tschicki/PS2-Portable/Documentation/assets/EE_Thermal_Pad.jpg

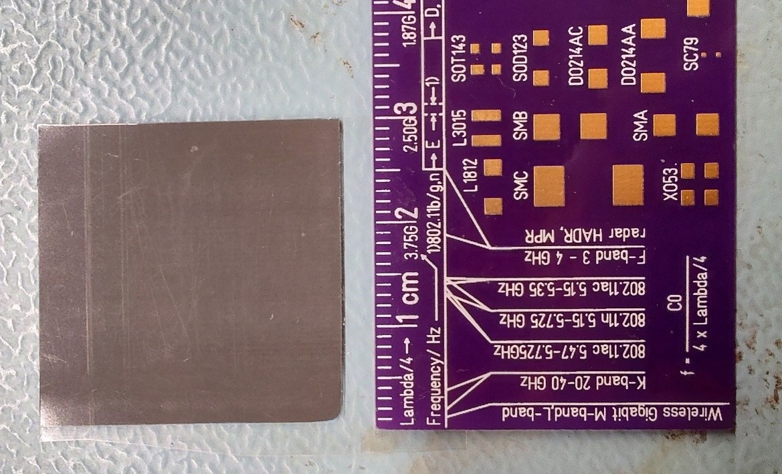
Documentation/assets/EE_Thermal_Pad.jpg
