tschicki/PS2-Portable/Documentation/assets/PS2_Impedances_Back.png

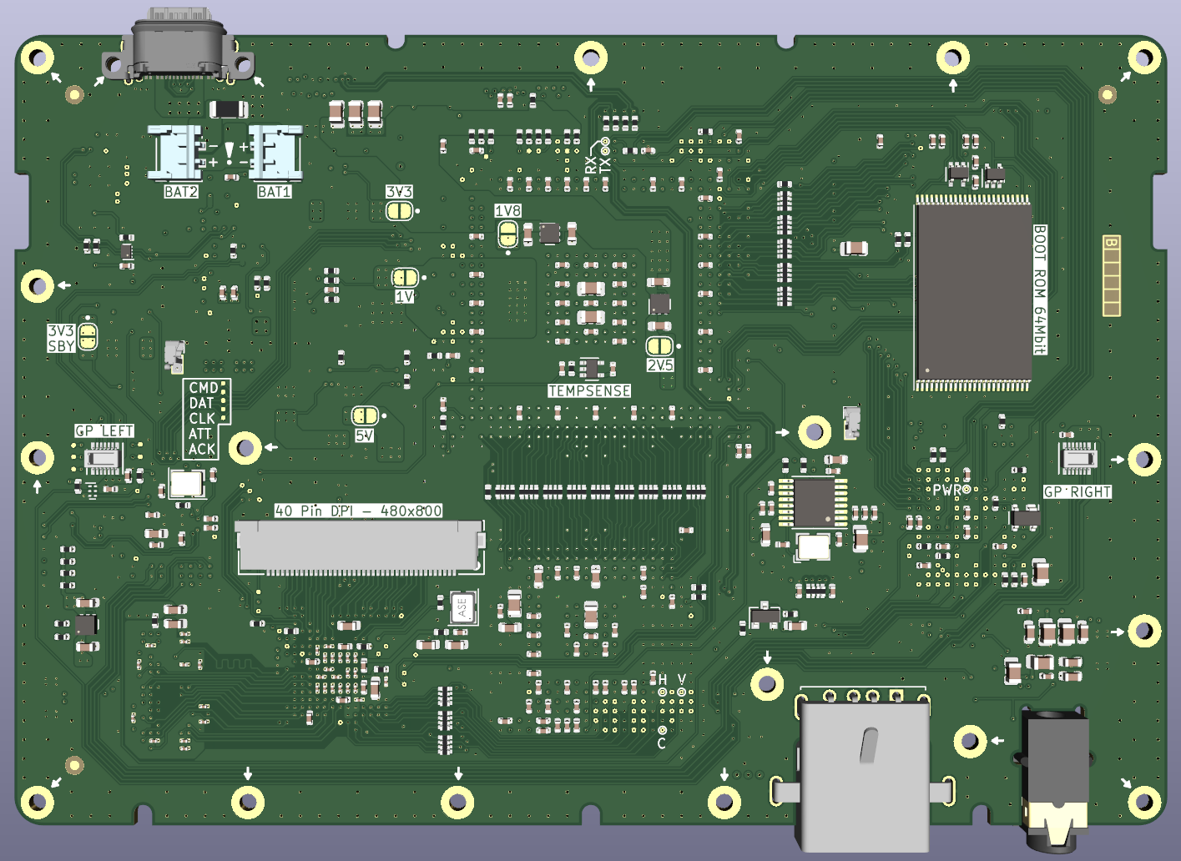
Documentation/assets/PS2_Impedances_Back.png
