tschicki/PS2-Portable/Electronics/PS2_79004_Rev_0_4/Images/LCD_Pinout.PNG

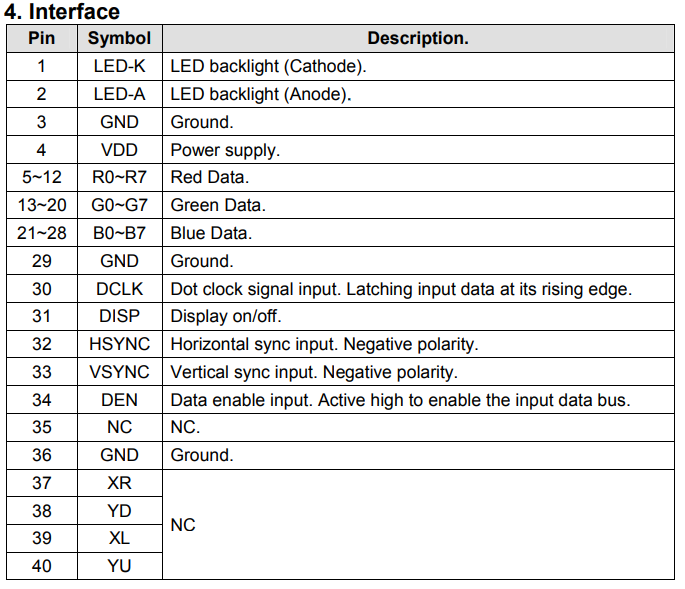
Electronics/PS2_79004_Rev_0_4/Images/LCD_Pinout.PNG
