tschicki/PS2-Portable/SysCon Firmware/SysCon_FW/ps2_video_processor/sdc/input.PNG

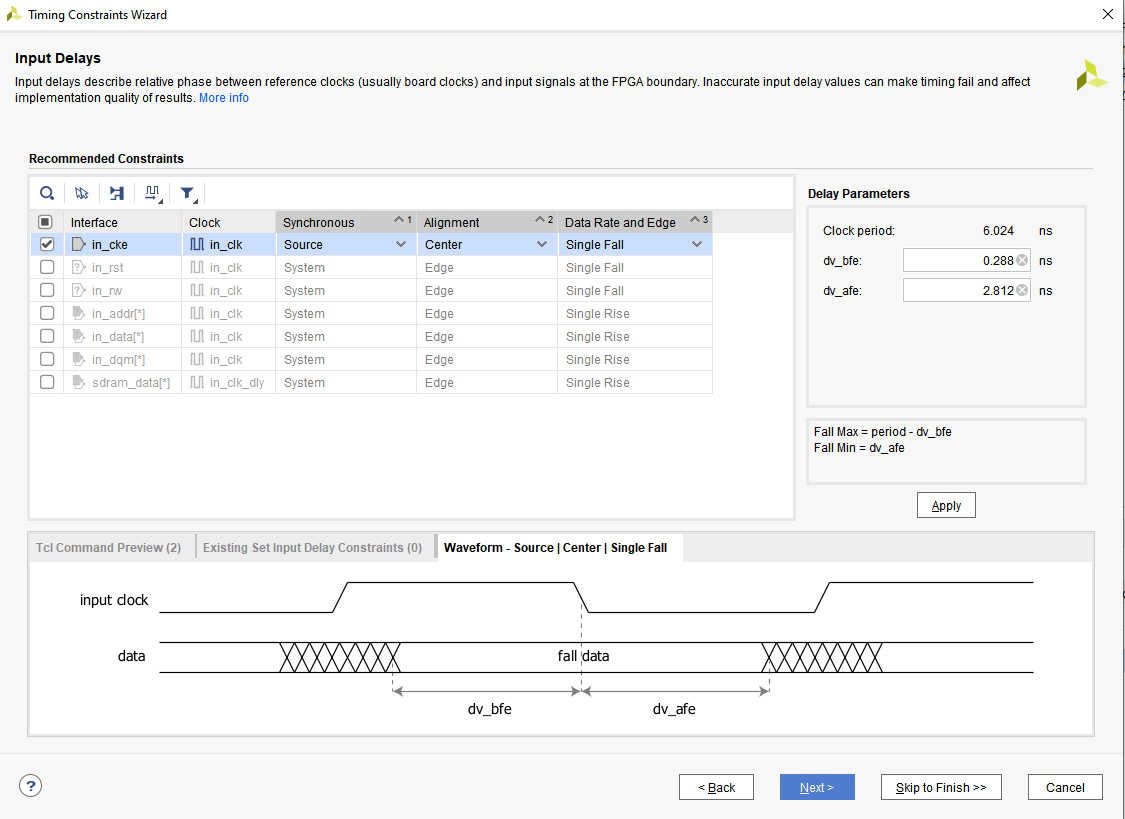
SysCon Firmware/SysCon_FW/ps2_video_processor/sdc/input.PNG
