tschicki/PS2-Portable/SysCon Firmware/SysCon_FW/ps2_video_processor/sdc/output1.PNG

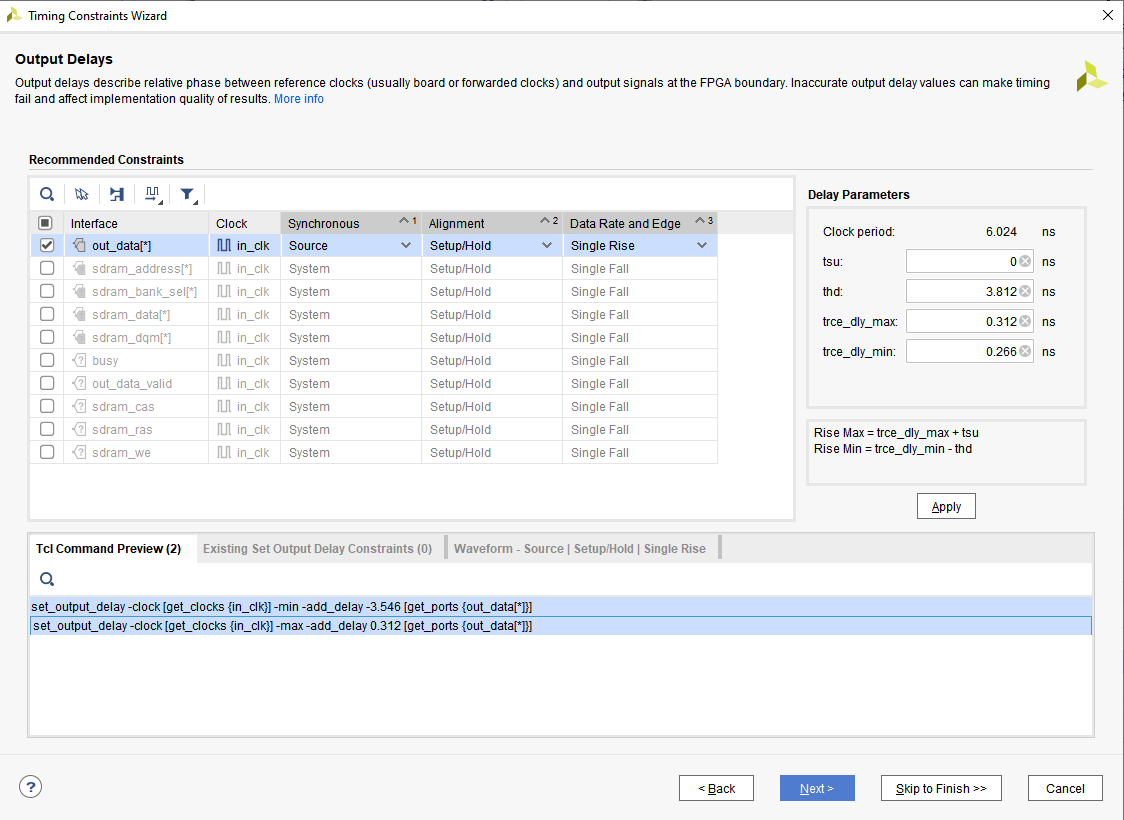
SysCon Firmware/SysCon_FW/ps2_video_processor/sdc/output1.PNG
