tschicki/PS2-Portable/Electronics/PS2_79004_Rev_0_4/Images/Ordering.png

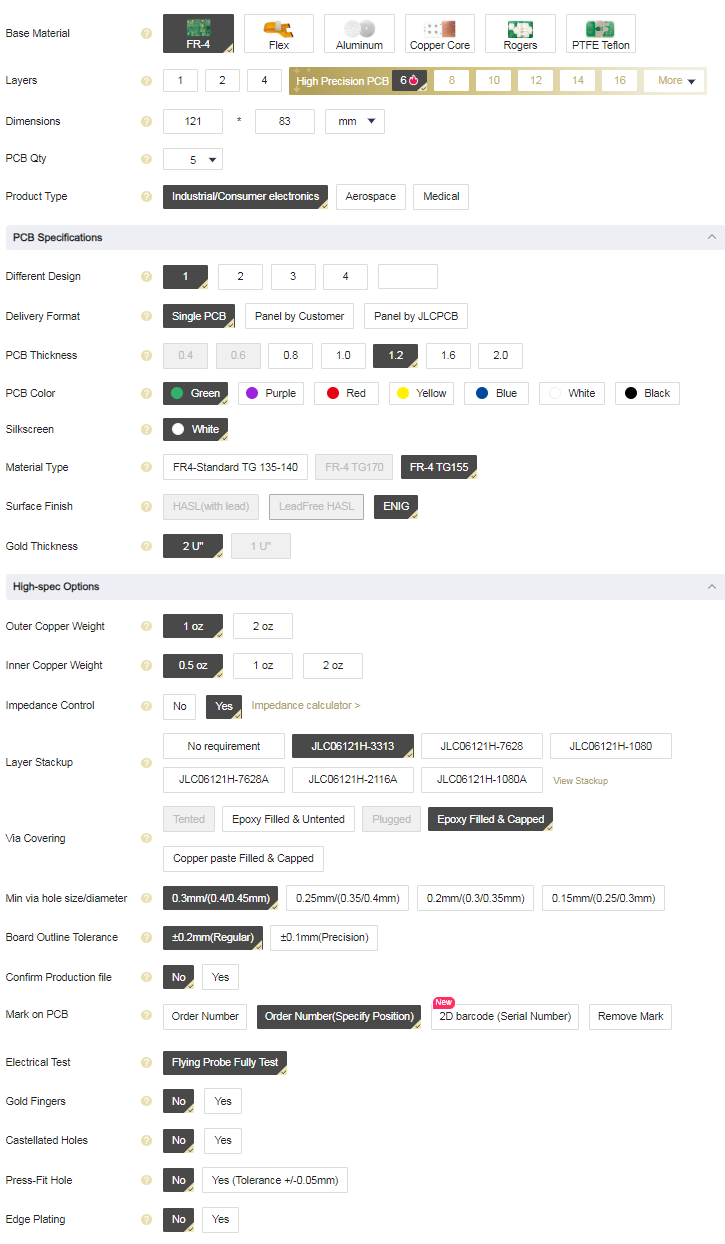
Electronics/PS2_79004_Rev_0_4/Images/Ordering.png
