tschicki/PS2-Portable/Solidworks/uSD2PSX/uSD2PSX_Base.SLDPRT

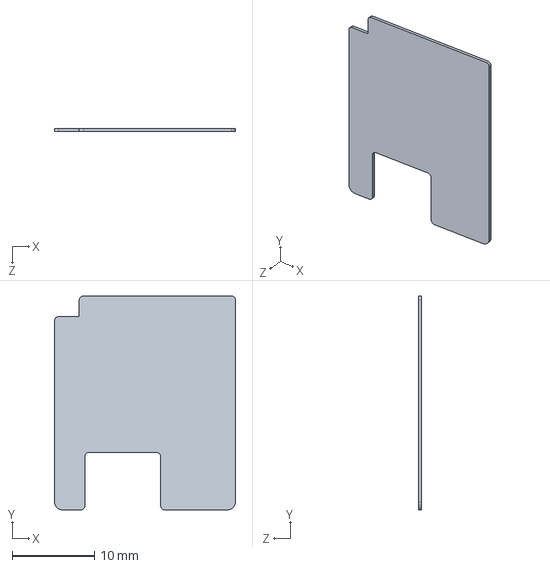
[picture p54: CAD file, 2025-11-29]
Solidworks/uSD2PSX/uSD2PSX_Base.SLDPRT
22.0 x 26.0 x 0.4 mm
