tschicki/PS2-Portable/_LIBRARIES/3D/FTSH-105-01-F-DV-K.stp

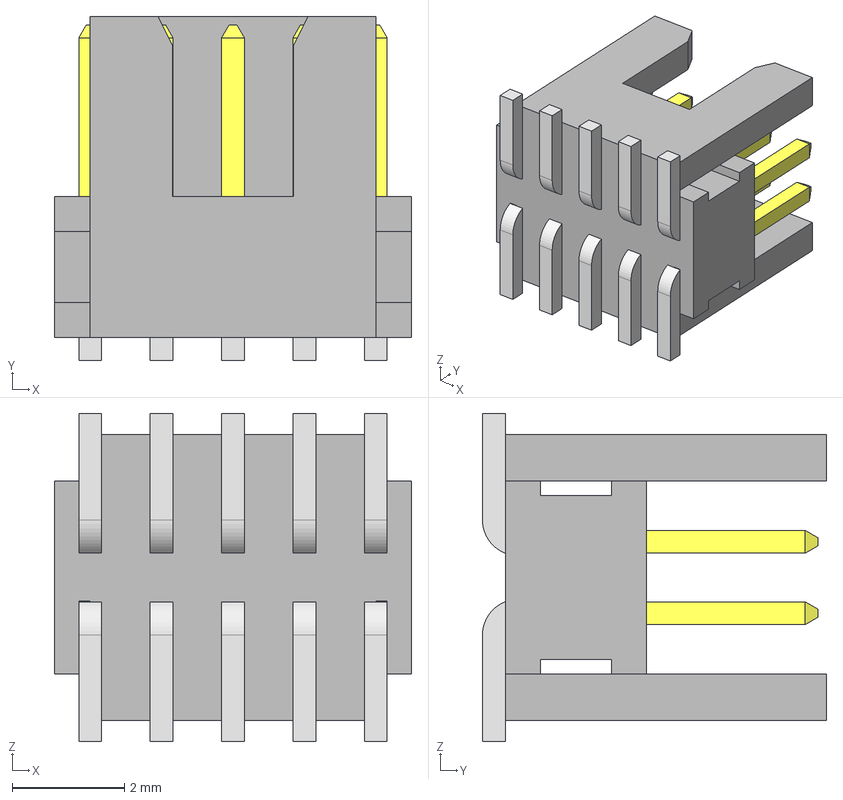
[picture p55: CAD file, 2025-11-29]
_LIBRARIES/3D/FTSH-105-01-F-DV-K.stp
6.35 x 6.12 x 5.84 mm
FTSH-105-01-F-DV-K_pins2
FTSH-105-01-F-DV-K_pins1
FTSH-105-01-F-DV-K_body
