tschicki/PS2-Portable/Solidworks/Button_Cover.SLDPRT

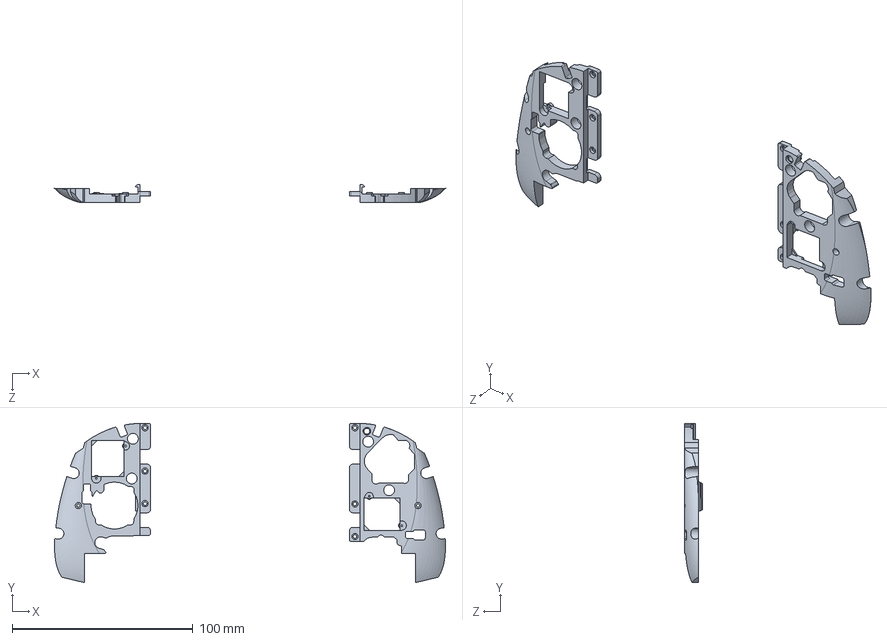
[picture p56: CAD file, 2025-11-29]
Solidworks/Button_Cover.SLDPRT
216.4 x 88.1 x 10.2 mm
