tschicki/PS2-Portable/Solidworks/CBA_Export/Gamepad_Right_export.SLDPRT

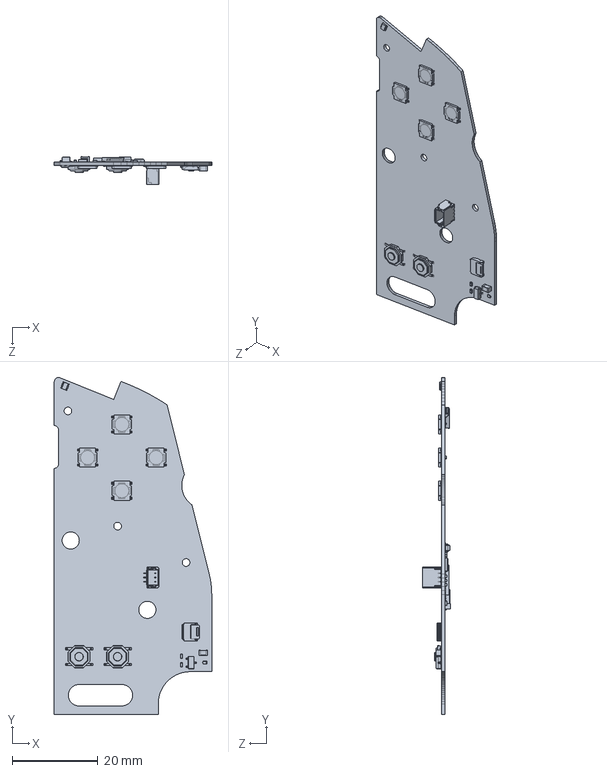
[picture p57: CAD file, 2025-11-29]
Solidworks/CBA_Export/Gamepad_Right_export.SLDPRT
36.8 x 78.7 x 6.50 mm
