tschicki/PS2-Portable/Solidworks/OTS_Parts/3DSXL_Screen_Lens.SLDPRT

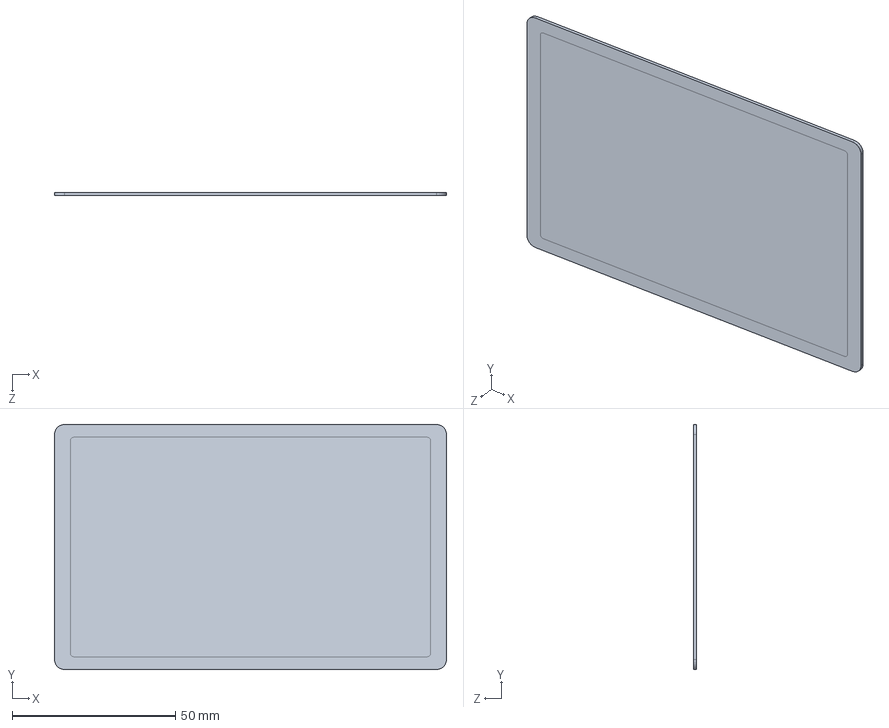
[picture p58: CAD file, 2025-11-29]
Solidworks/OTS_Parts/3DSXL_Screen_Lens.SLDPRT
120.0 x 75.0 x 1.00 mm
