tschicki/PS2-Portable/Solidworks/Output/Output Assembly/DPAD Sanding Tool.SLDPRT

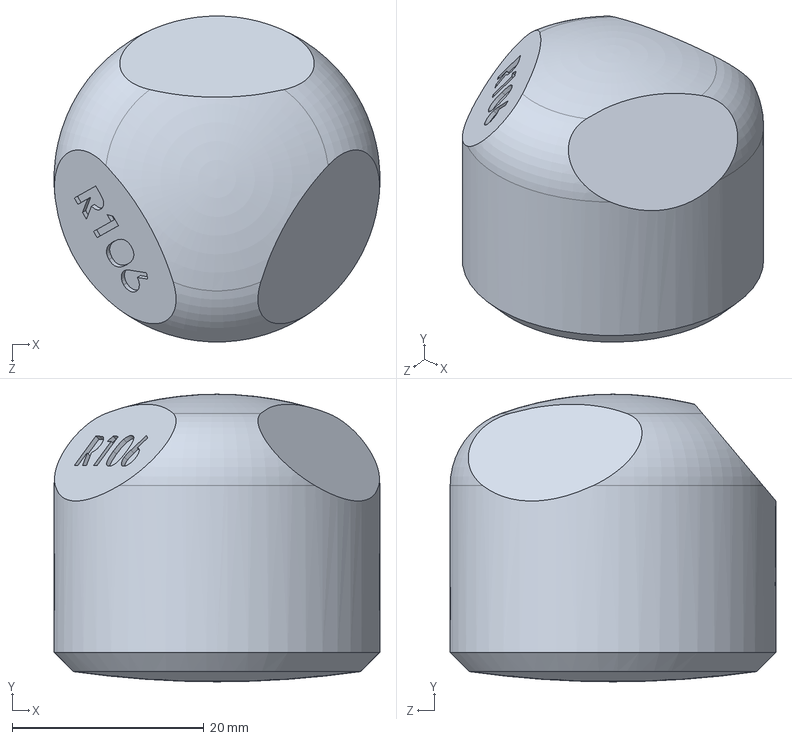
[picture p59: CAD file, 2026-04-04]
Solidworks/Output/Output Assembly/DPAD Sanding Tool.SLDPRT
34.0 x 30.0 x 34.0 mm
