tschicki/PS2-Portable/Solidworks/Output/STEP/Speaker Plug REF2016.STEP

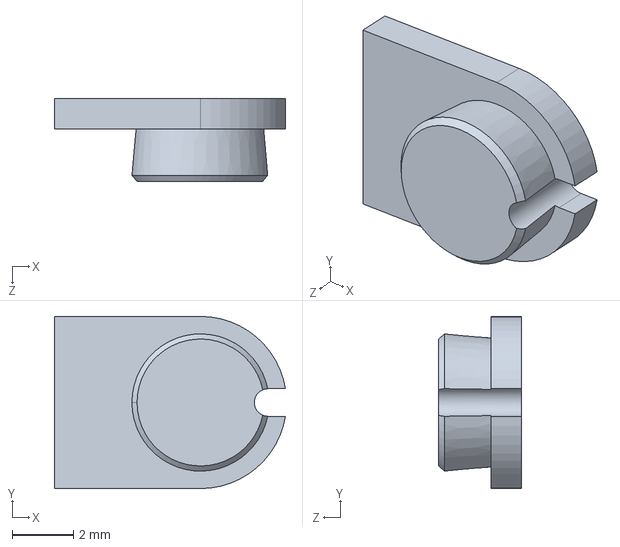
[picture p60: CAD file, 2026-04-04]
Solidworks/Output/STEP/Speaker Plug REF2016.STEP
7.51 x 5.60 x 2.70 mm
