tschicki/PS2-Portable/Solidworks/Output/STL/Export - Travel Case Top REF2020-1.STL

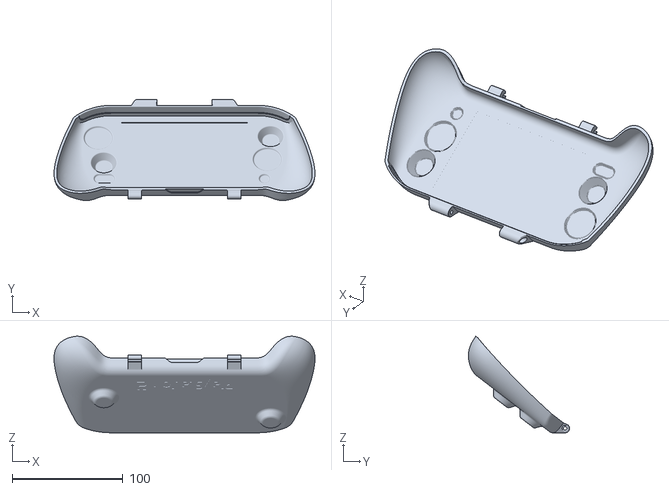
[picture p61: CAD file, 2026-04-04]
Solidworks/Output/STL/Export - Travel Case Top REF2020-1.STL
236.2 x 91.6 x 87.4
