tschicki/PS2-Portable/_LIBRARIES/3D/DF40C-80DP-0.4V_51_.step

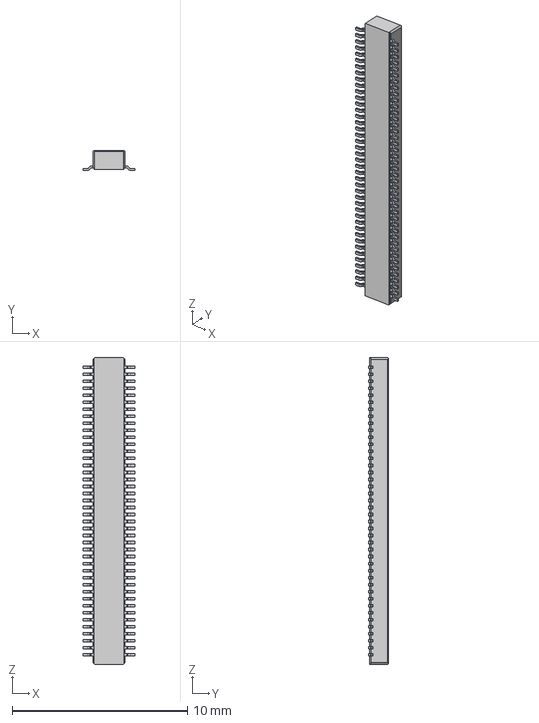
[picture p62: CAD file, 2025-11-29]
_LIBRARIES/3D/DF40C-80DP-0.4V_51_.step
2.97 x 1.14 x 17.5 mm
