tschicki/PS2-Portable/Solidworks/OTS_Parts/Switch_Joystick.SLDPRT

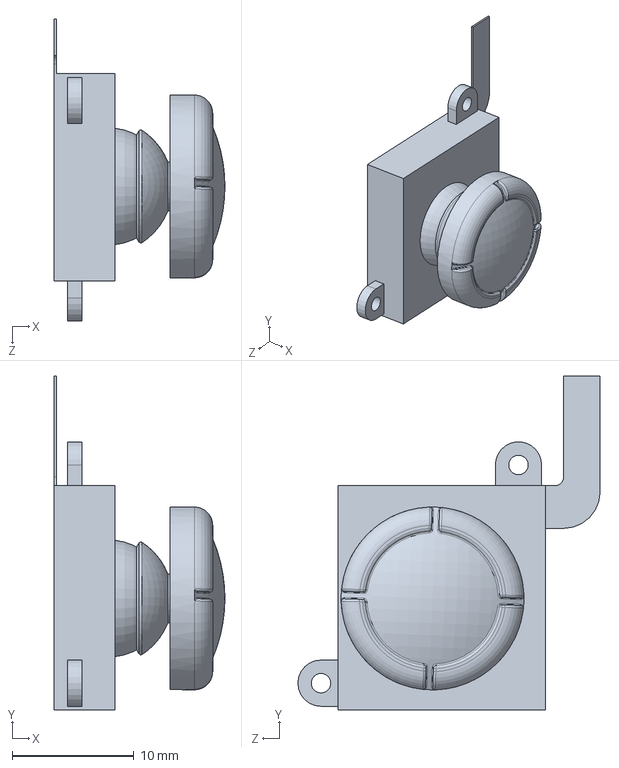
[picture p63: CAD file, 2025-11-29]
Solidworks/OTS_Parts/Switch_Joystick.SLDPRT
14.0 x 27.4 x 24.8 mm
