tschicki/PS2-Portable/Solidworks/Output/Output Assembly/PS2 Heatsink REF3000.SLDPRT

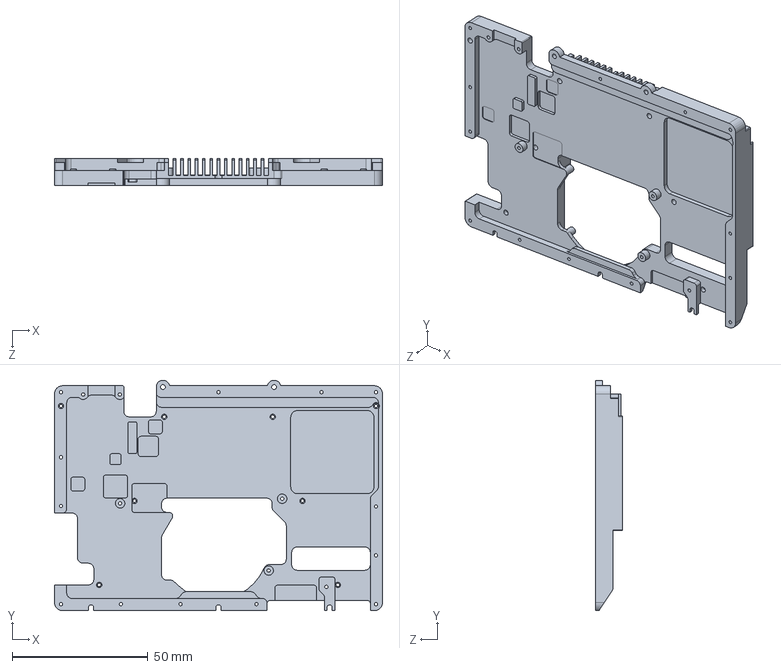
[picture p64: CAD file, 2026-04-04]
Solidworks/Output/Output Assembly/PS2 Heatsink REF3000.SLDPRT
121.0 x 85.0 x 10.0 mm
