tschicki/PS2-Portable/Solidworks/Output/STEP/L2 Button REF2011.STEP

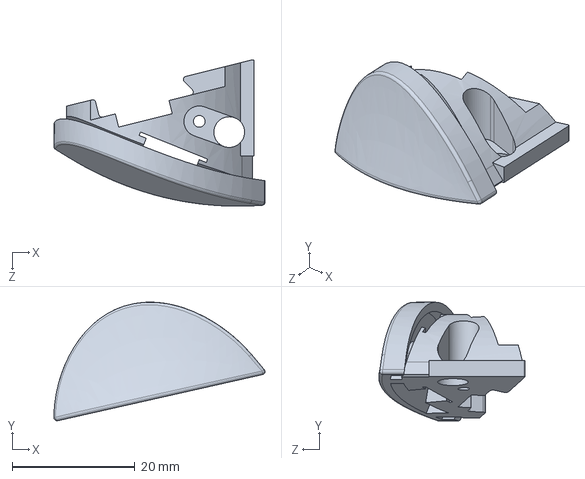
[picture p65: CAD file, 2026-04-04]
Solidworks/Output/STEP/L2 Button REF2011.STEP
34.4 x 19.3 x 23.9 mm
