tschicki/PS2-Portable/Solidworks/Output/STL/Export - Battery Compartment Left REF2004-1.STL

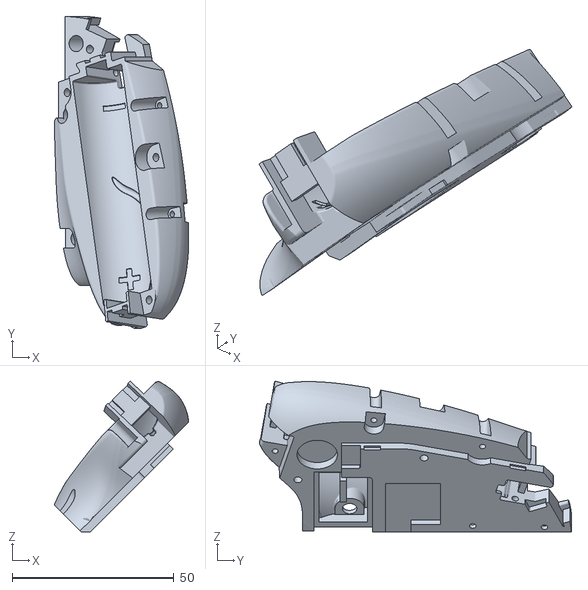
[picture p66: CAD file, 2026-04-04]
Solidworks/Output/STL/Export - Battery Compartment Left REF2004-1.STL
41.5 x 96.3 x 46.6
