tschicki/PS2-Portable/Solidworks/uSD2PSX/uSD2PSX_PCBA.SLDPRT

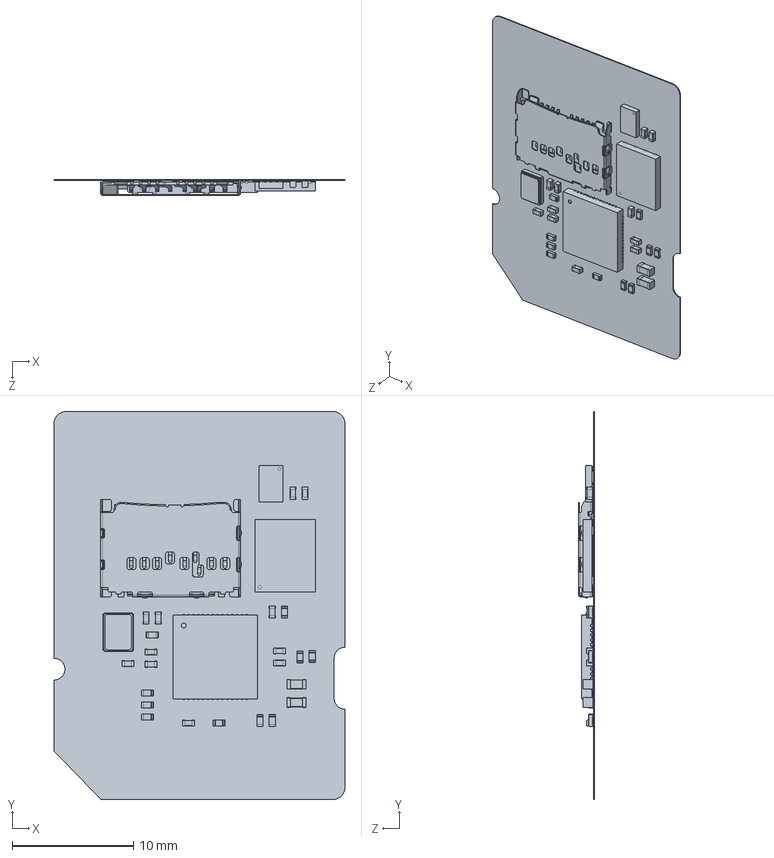
[picture p67: CAD file, 2025-11-29]
Solidworks/uSD2PSX/uSD2PSX_PCBA.SLDPRT
24.0 x 32.0 x 1.34 mm
