tschicki/PS2-Portable/_LIBRARIES/3D/EAST1616RGBA0.STEP

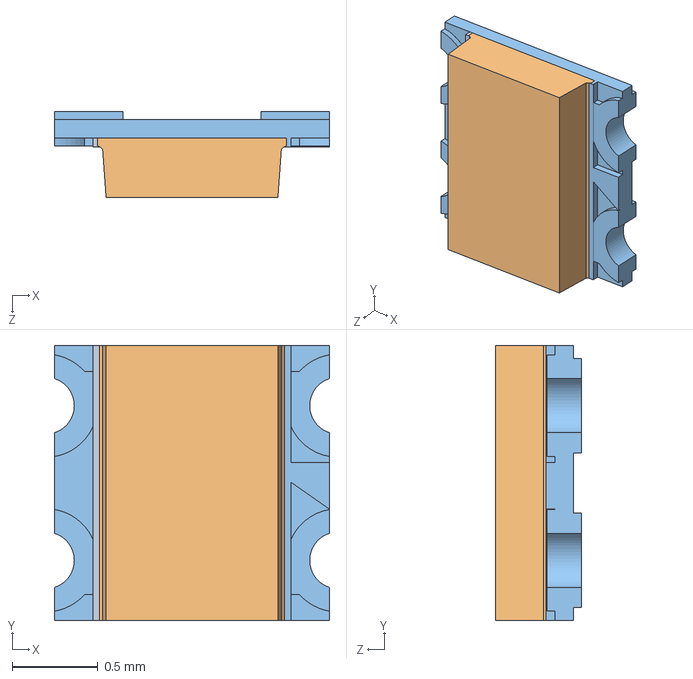
[picture p68: CAD file, 2025-11-29]
_LIBRARIES/3D/EAST1616RGBA0.STEP
1.60 x 1.60 x 0.5 mm
