tschicki/PS2-Portable/Solidworks/Mainboard/PS2_USB_A_90k.SLDPRT

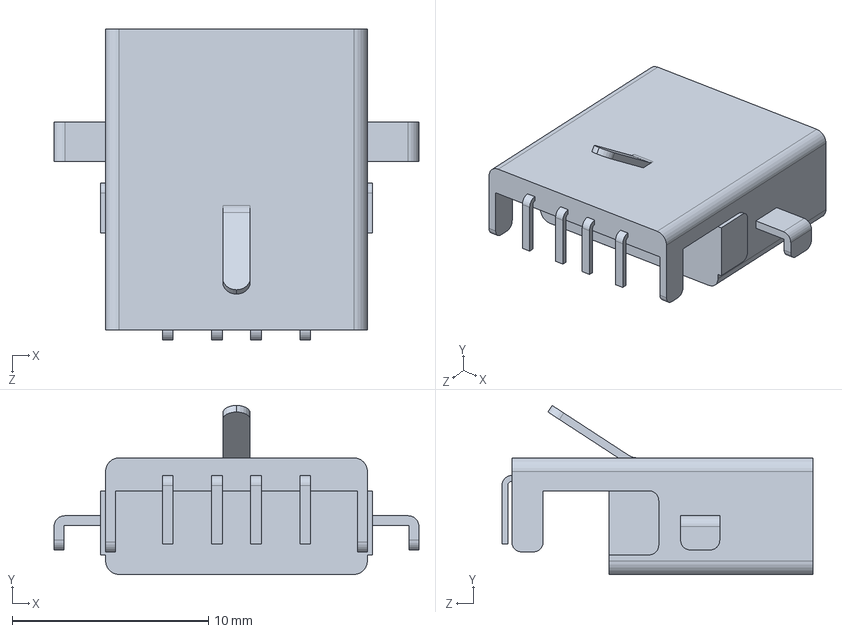
[picture p69: CAD file, 2025-11-29]
Solidworks/Mainboard/PS2_USB_A_90k.SLDPRT
18.6 x 8.62 x 15.9 mm
