tschicki/PS2-Portable/Solidworks/MemoryCard_Cover.SLDPRT

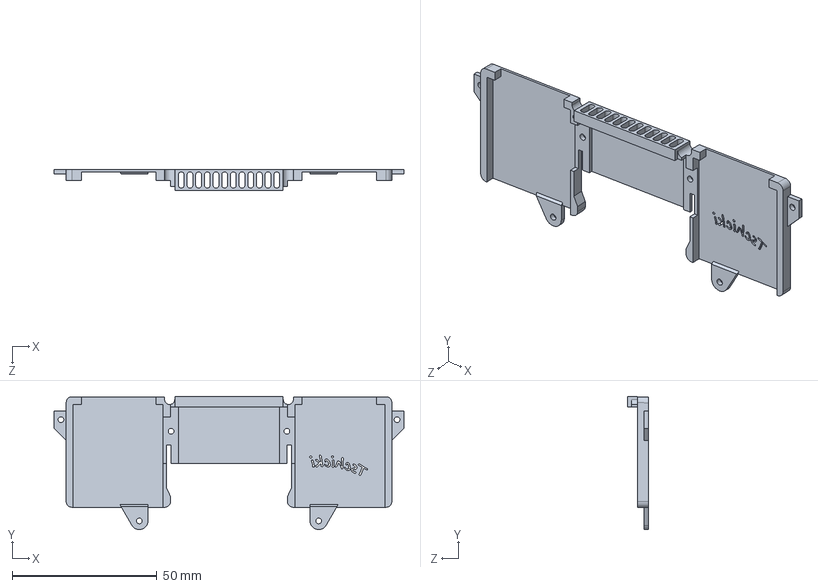
[picture p70: CAD file, 2025-11-29]
Solidworks/MemoryCard_Cover.SLDPRT
121.0 x 46.1 x 7.20 mm
