tschicki/PS2-Portable/Solidworks/OTS_Parts/D-PAD PSVITA2000.SLDPRT

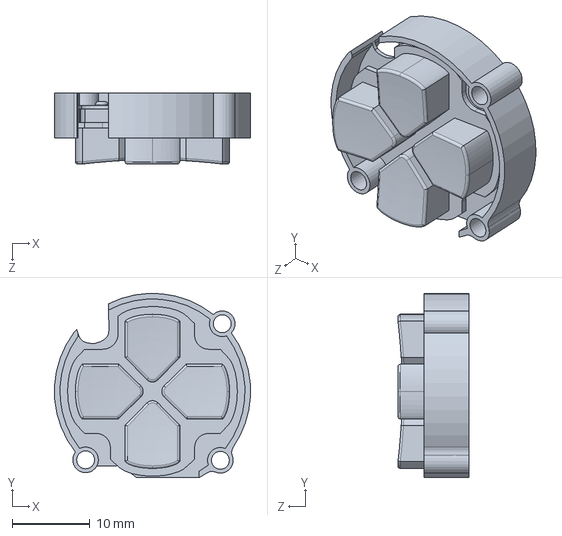
[picture p71: CAD file, 2025-11-29]
Solidworks/OTS_Parts/D-PAD PSVITA2000.SLDPRT
25.2 x 23.6 x 9.14 mm
