tschicki/PS2-Portable/Solidworks/Output/STEP/Battery Compartment Left REF2004.STEP

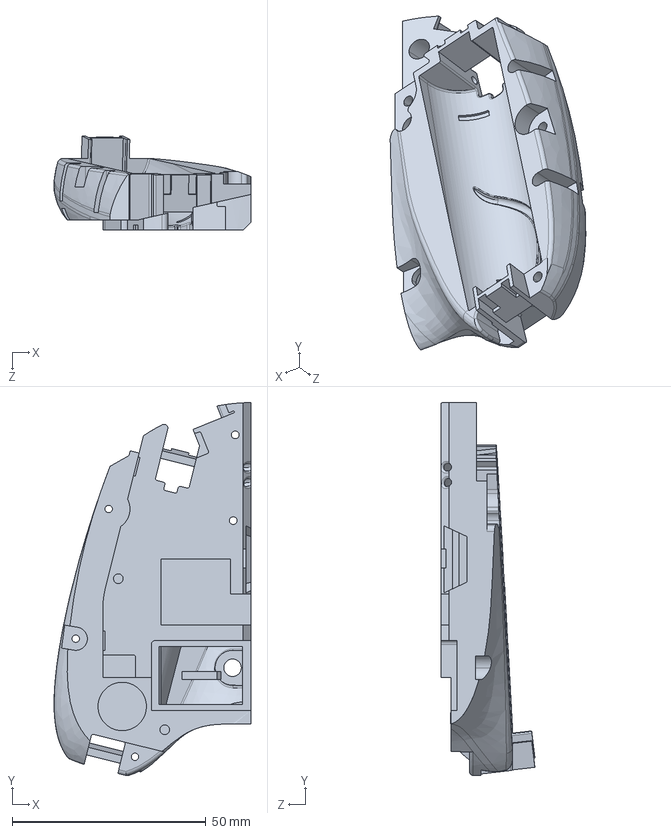
[picture p72: CAD file, 2026-04-04]
Solidworks/Output/STEP/Battery Compartment Left REF2004.STEP
50.9 x 96.3 x 24.2 mm
