tschicki/PS2-Portable/Solidworks/Output/STL/Export - Screen Lens Frame REF2008-1.STL

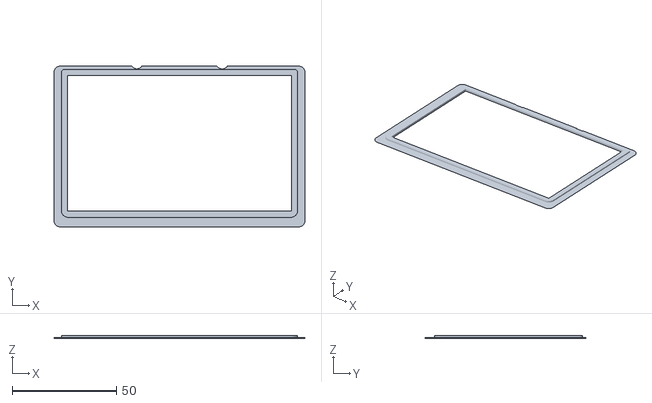
[picture p73: CAD file, 2026-04-04]
Solidworks/Output/STL/Export - Screen Lens Frame REF2008-1.STL
120.5 x 77.2 x 1.30
