tschicki/PS2-Portable/Solidworks/Gamepad_Flex.SLDPRT

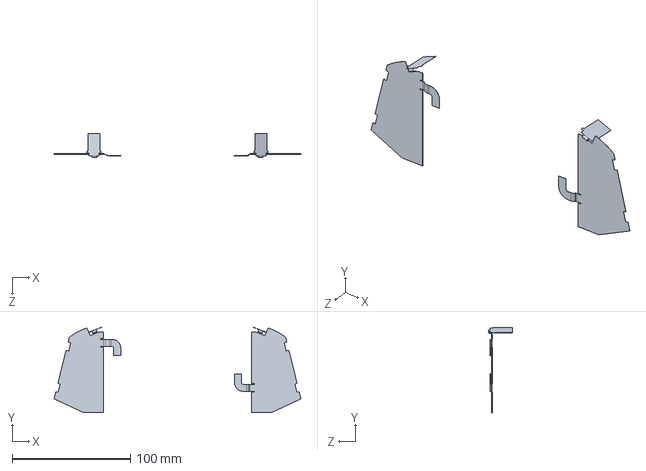
[picture p74: CAD file, 2025-11-29]
Solidworks/Gamepad_Flex.SLDPRT
208.9 x 72.1 x 20.0 mm
