tschicki/PS2-Portable/Solidworks/Mainboard/CXD2980CGB.SLDPRT

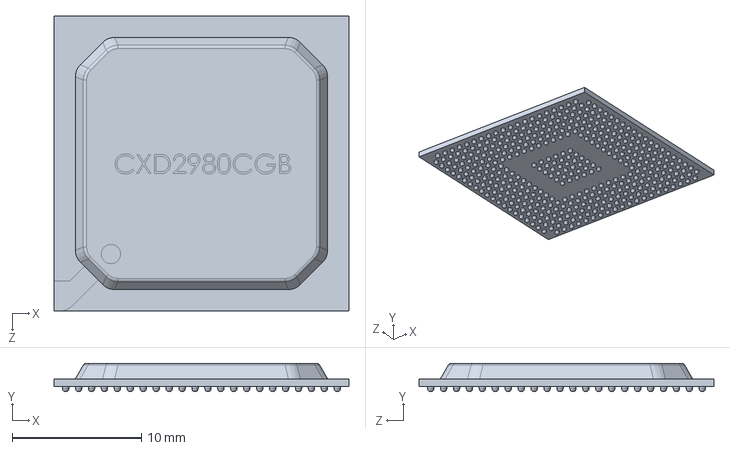
[picture p75: CAD file, 2025-11-29]
Solidworks/Mainboard/CXD2980CGB.SLDPRT
22.8 x 2.20 x 22.8 mm
