tschicki/PS2-Portable/Solidworks/OTS_Parts/Start_Select_PSVITA2000.SLDPRT

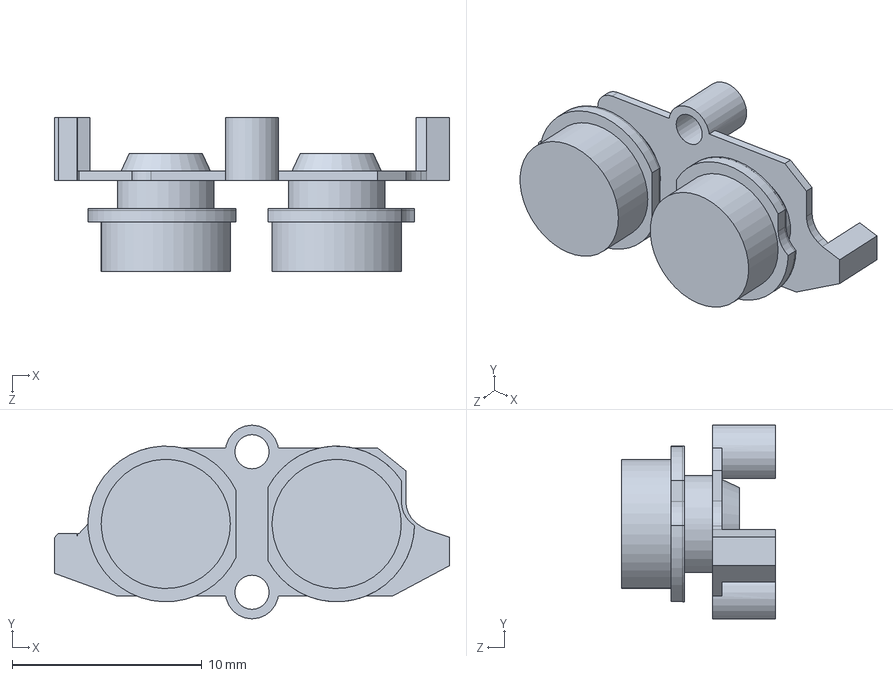
[picture p76: CAD file, 2025-11-29]
Solidworks/OTS_Parts/Start_Select_PSVITA2000.SLDPRT
20.8 x 10.2 x 8.10 mm
