tschicki/PS2-Portable/Solidworks/Output/STL/Export - Lower Display Mount REF2009-1.STL

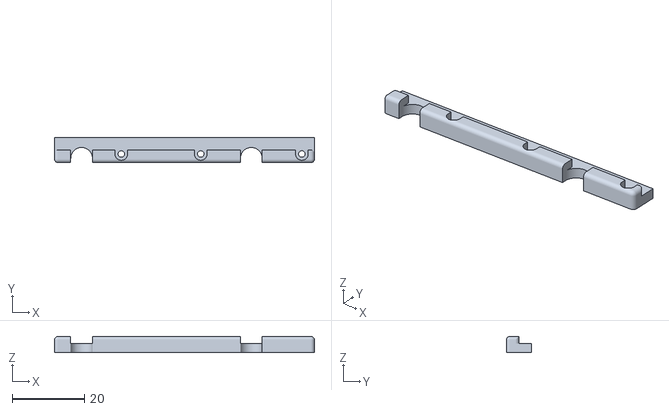
[picture p77: CAD file, 2026-04-04]
Solidworks/Output/STL/Export - Lower Display Mount REF2009-1.STL
72.0 x 7.00 x 4.50
