tschicki/PS2-Portable/Solidworks/Gamepad_Outline.SLDPRT

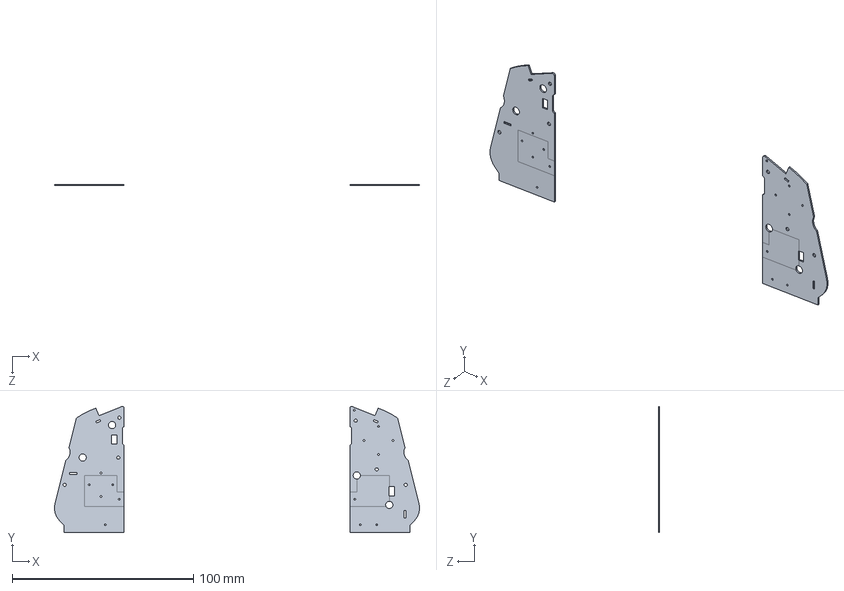
[picture p78: CAD file, 2025-11-29]
Solidworks/Gamepad_Outline.SLDPRT
201.2 x 69.5 x 0.8 mm
