tschicki/PS2-Portable/Solidworks/Mainboard/CXD3098AQ.SLDPRT

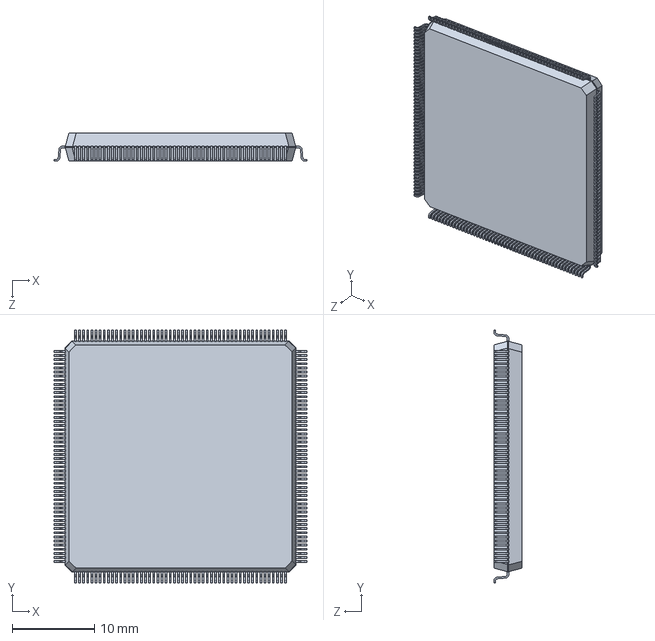
[picture p79: CAD file, 2025-11-29]
Solidworks/Mainboard/CXD3098AQ.SLDPRT
30.7 x 30.7 x 3.40 mm
