tschicki/PS2-Portable/Solidworks/OTS_Parts/Switch_Lite_Fan.SLDPRT

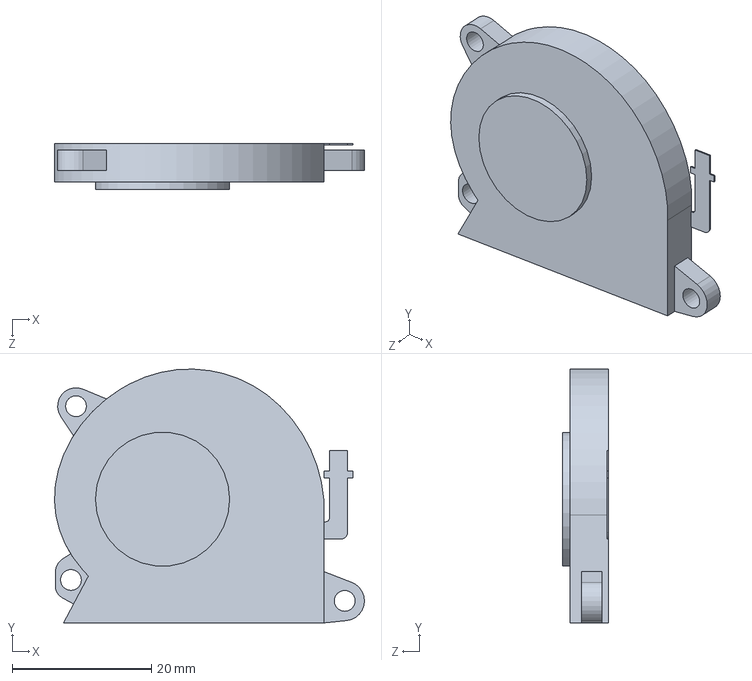
[picture p80: CAD file, 2025-11-29]
Solidworks/OTS_Parts/Switch_Lite_Fan.SLDPRT
44.6 x 36.5 x 6.60 mm
