tschicki/PS2-Portable/Solidworks/Output/Output Assembly/Backside Vent Cover REF2014.SLDPRT

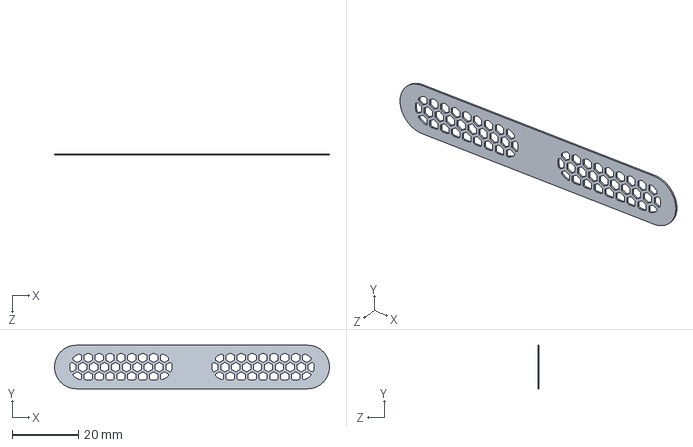
[picture p81: CAD file, 2025-11-29]
Solidworks/Output/Output Assembly/Backside Vent Cover REF2014.SLDPRT
83.2 x 13.2 x 0.45 mm
