tschicki/PS2-Portable/Solidworks/Output/STL/Export - Speaker Cover Right REF2007-1.STL

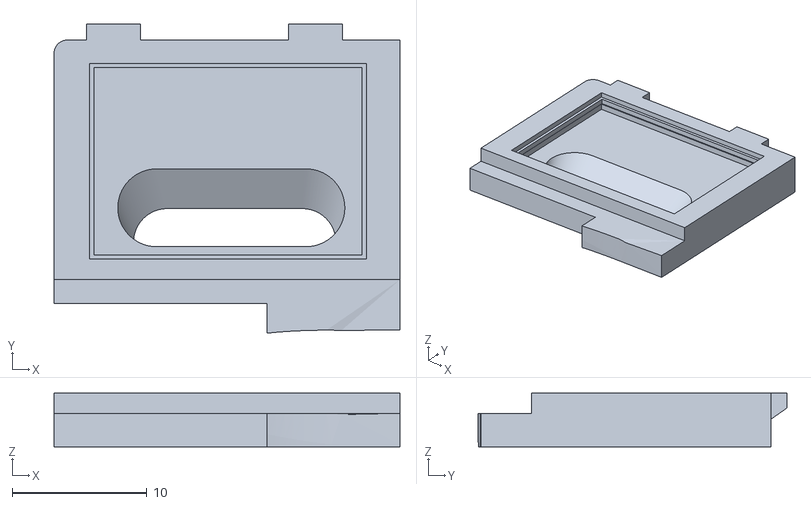
[picture p82: CAD file, 2026-04-04]
Solidworks/Output/STL/Export - Speaker Cover Right REF2007-1.STL
25.7 x 22.9 x 4.00
