tschicki/PS2-Portable/_LIBRARIES/3D/DF40C(2.0)-50DS.stp

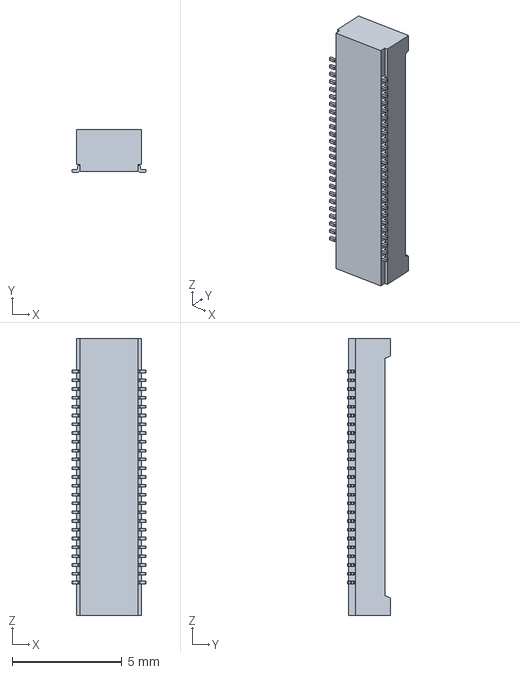
[picture p83: CAD file, 2025-11-29]
_LIBRARIES/3D/DF40C(2.0)-50DS.stp
3.38 x 1.95 x 12.6 mm
