tschicki/PS2-Portable/Solidworks/Mainboard/TSOP50-II.SLDPRT

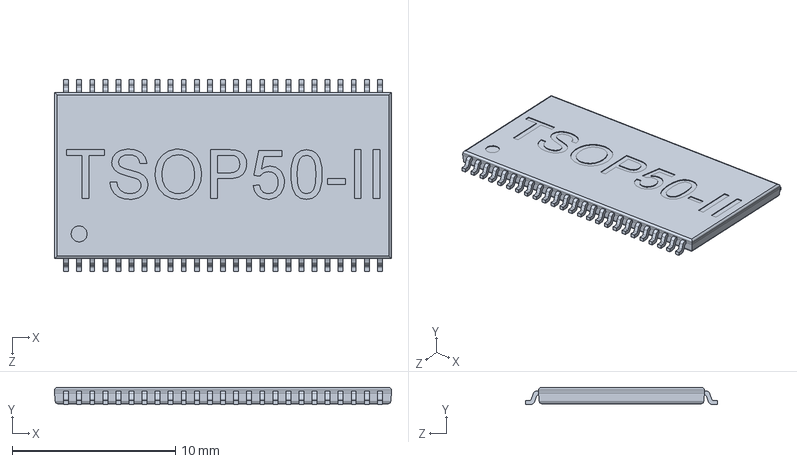
[picture p84: CAD file, 2025-11-29]
Solidworks/Mainboard/TSOP50-II.SLDPRT
20.6 x 1.05 x 11.8 mm
