tschicki/PS2-Portable/Solidworks/Output/Output Assembly/Display Stand REF2019.SLDPRT

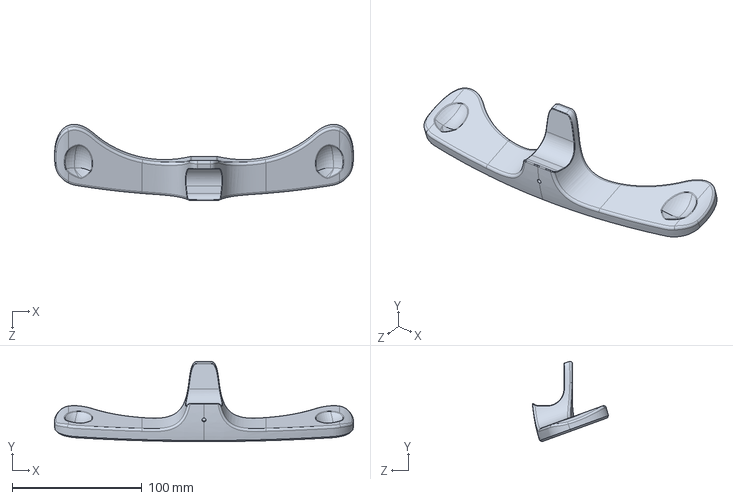
[picture p85: CAD file, 2025-11-29]
Solidworks/Output/Output Assembly/Display Stand REF2019.SLDPRT
230.4 x 61.9 x 58.8 mm
