tschicki/PS2-Portable/Solidworks/Output/STL/Export - Travel Case Latch Right REF2023-1.STL

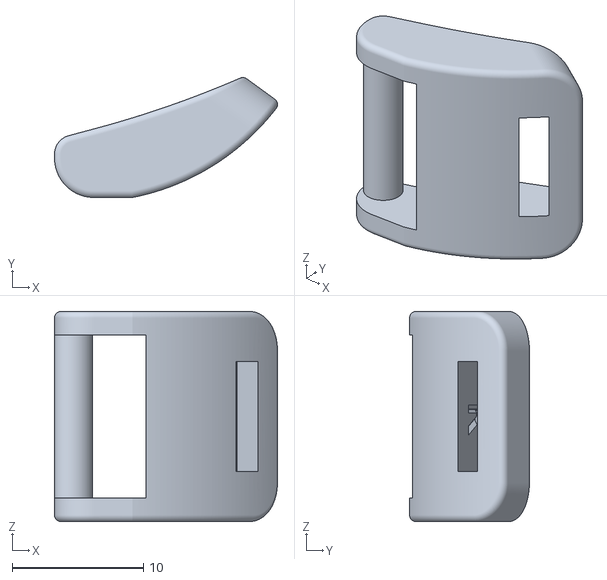
[picture p86: CAD file, 2026-04-04]
Solidworks/Output/STL/Export - Travel Case Latch Right REF2023-1.STL
17.0 x 9.13 x 16.0
