tschicki/PS2-Portable/_LIBRARIES/3D/CX70M-24P1.step

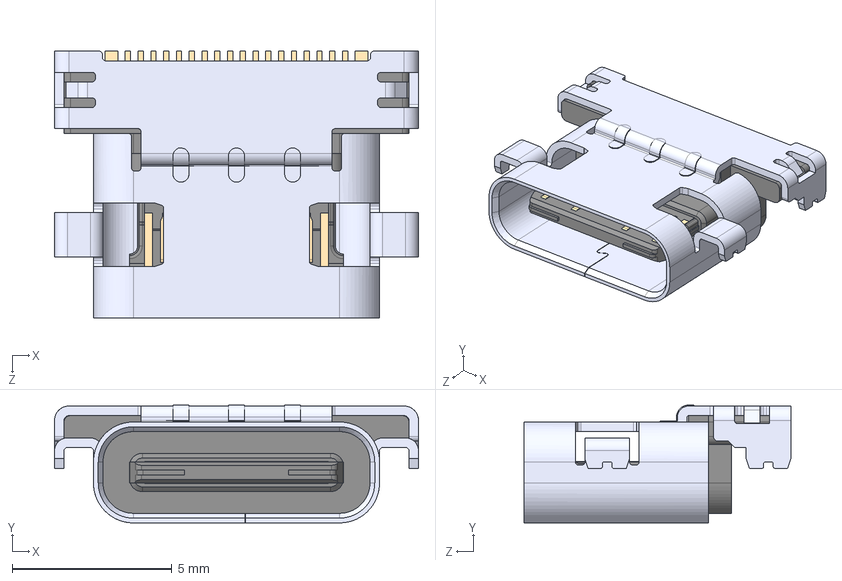
[picture p87: CAD file, 2025-11-29]
_LIBRARIES/3D/CX70M-24P1.step
11.4 x 3.69 x 8.35 mm
