tschicki/PS2-Portable/Solidworks/Mainboard/JST_BM02B-SURS-TF_DIY.SLDPRT

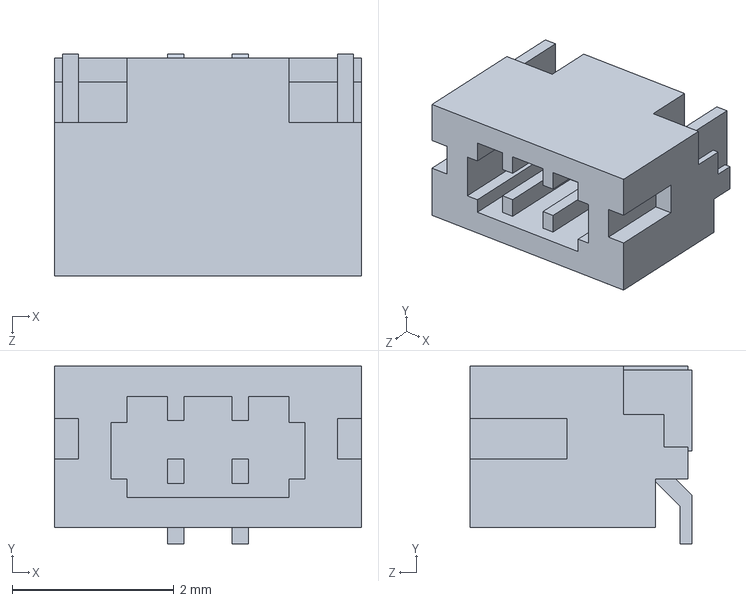
[picture p88: CAD file, 2025-11-29]
Solidworks/Mainboard/JST_BM02B-SURS-TF_DIY.SLDPRT
3.80 x 2.20 x 2.75 mm
