tschicki/PS2-Portable/Solidworks/OTS_Parts/vibration_motor_10mm.SLDPRT

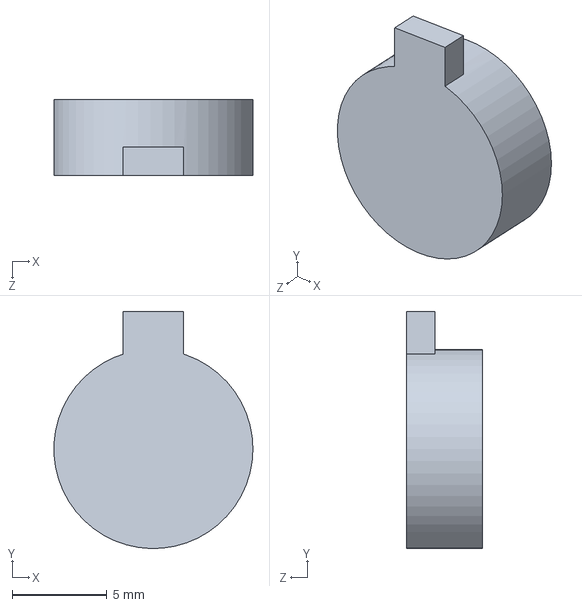
[picture p89: CAD file, 2025-11-29]
Solidworks/OTS_Parts/vibration_motor_10mm.SLDPRT
10.5 x 12.5 x 4.00 mm
