tschicki/PS2-Portable/Solidworks/Output/STEP/R2 Button REF2012.STEP

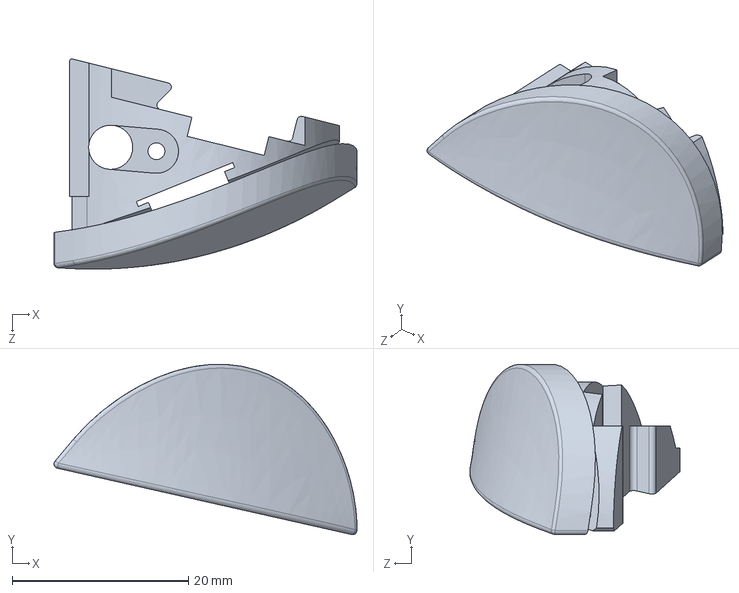
[picture p90: CAD file, 2026-04-04]
Solidworks/Output/STEP/R2 Button REF2012.STEP
34.4 x 19.3 x 23.9 mm
