tschicki/PS2-Portable/Solidworks/Output/STL/Export - MemoryCard Cover REF2013-1.STL

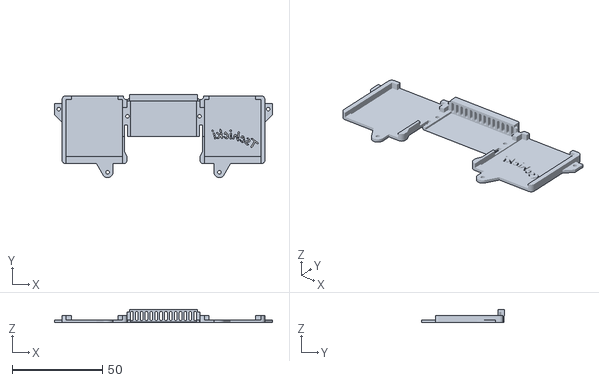
[picture p91: CAD file, 2026-04-04]
Solidworks/Output/STL/Export - MemoryCard Cover REF2013-1.STL
121.0 x 46.2 x 7.20
