tschicki/PS2-Portable/Solidworks/Speaker_Cover.SLDPRT

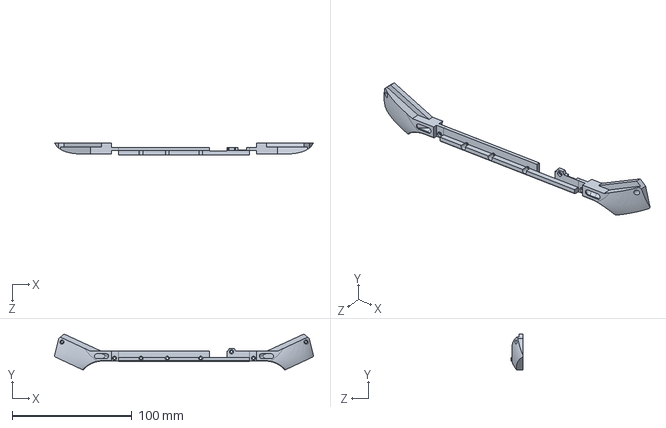
[picture p92: CAD file, 2025-11-29]
Solidworks/Speaker_Cover.SLDPRT
216.7 x 30.1 x 10.4 mm
