tschicki/PS2-Portable/_LIBRARIES/3D/W25Q16JVUXIQ_TR.step

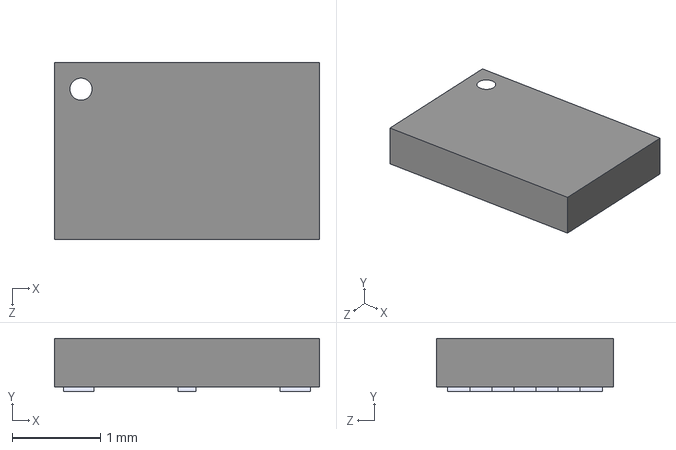
[picture p93: CAD file, 2025-11-29]
_LIBRARIES/3D/W25Q16JVUXIQ_TR.step
3.00 x 0.6 x 2.00 mm
