tschicki/PS2-Portable/Solidworks/OTS_Parts/LED_EAST1616RGBA0.SLDPRT

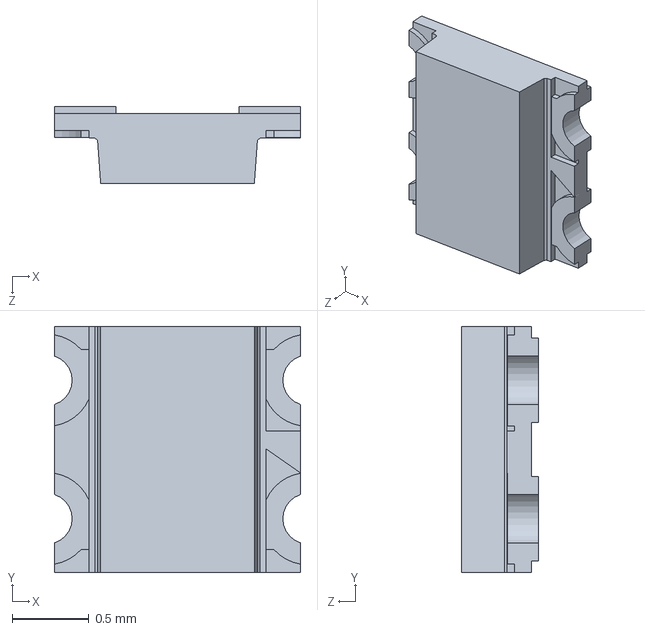
[picture p94: CAD file, 2025-11-29]
Solidworks/OTS_Parts/LED_EAST1616RGBA0.SLDPRT
1.60 x 1.60 x 0.5 mm
