tschicki/PS2-Portable/Solidworks/Output/STL/Export - uSD2PSX Frame REF2017-1.STL

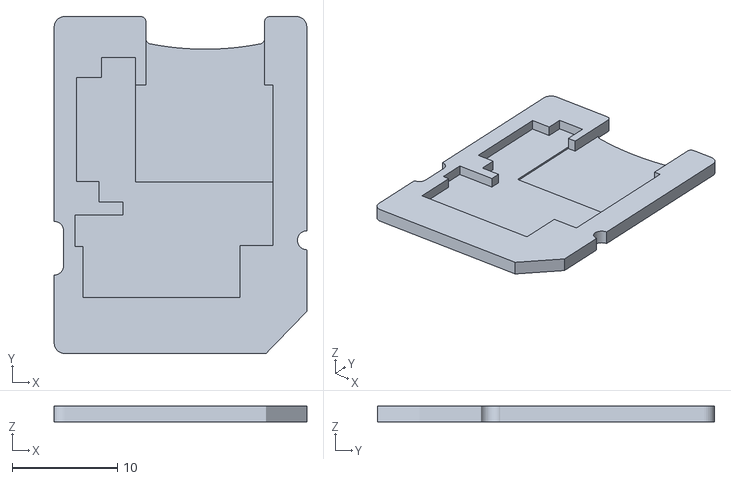
[picture p95: CAD file, 2026-04-04]
Solidworks/Output/STL/Export - uSD2PSX Frame REF2017-1.STL
24.0 x 32.0 x 1.50
