tschicki/PS2-Portable/Solidworks/R1-L1_Bar.SLDPRT

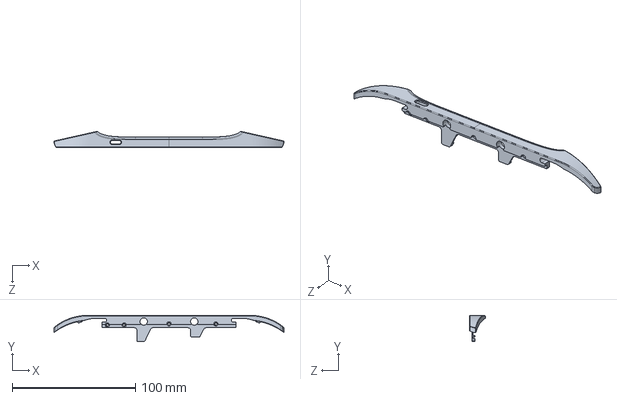
[picture p96: CAD file, 2025-11-29]
Solidworks/R1-L1_Bar.SLDPRT
186.4 x 21.2 x 13.3 mm
