tschicki/PS2-Portable/_LIBRARIES/3D/SOD-923_0P6X0P85_ONS.step

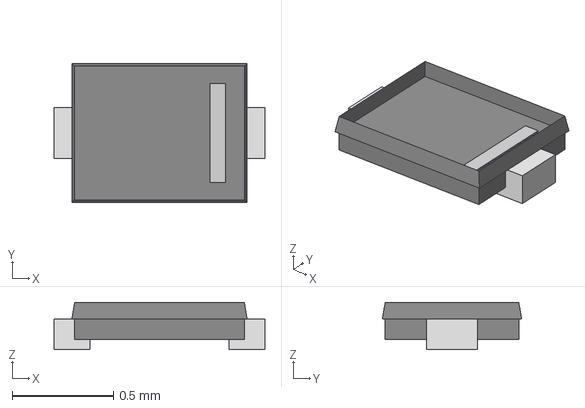
[picture p97: CAD file, 2025-11-29]
_LIBRARIES/3D/SOD-923_0P6X0P85_ONS.step
1.04 x 0.688 x 0.234 mm
