tschicki/PS2-Portable/Solidworks/OTS_Parts/KSC222J LFS.SLDPRT

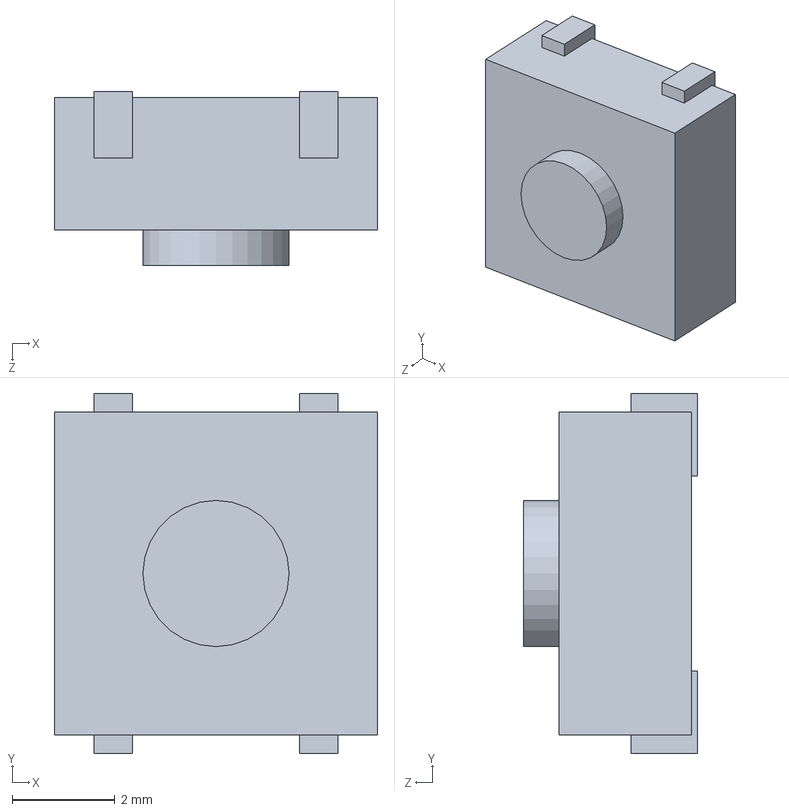
[picture p98: CAD file, 2025-11-29]
Solidworks/OTS_Parts/KSC222J LFS.SLDPRT
6.30 x 7.02 x 3.40 mm
