tschicki/PS2-Portable/_LIBRARIES/3D/FTDI - FT4232H Module.stp

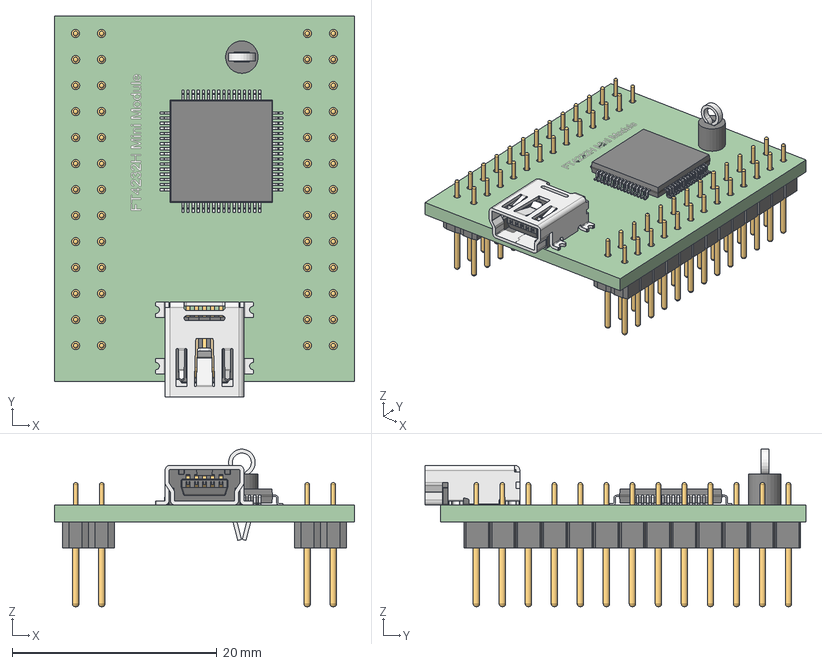
[picture p99: CAD file, 2025-11-29]
_LIBRARIES/3D/FTDI - FT4232H Module.stp
29.3 x 37.2 x 15.4 mm
FTDI - FT4232H Mini Module PCB
Keystone Electronics - 5006 PC TEST POINT COMPACT BLACK
Würth Elektronik - 65100516121 CONN RCPT USB2.0 MINI B SMD
Samtec - TD-113-T-A CONN HEADER VERT 26POS 2.54MM x 2
Package - 64-LQFP
