tschicki/PS2-Portable/Solidworks/OTS_Parts/Keystone_209.SLDPRT

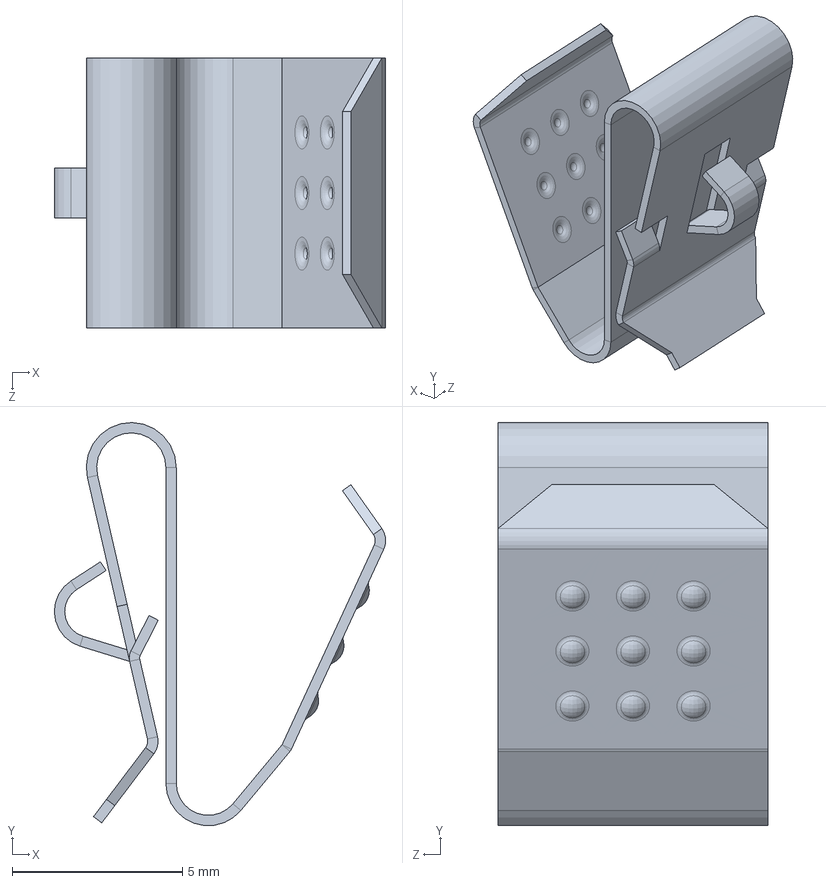
[picture p100: CAD file, 2025-11-29]
Solidworks/OTS_Parts/Keystone_209.SLDPRT
9.73 x 11.8 x 7.92 mm
