tschicki/PS2-Portable/Solidworks/R2-L2_Button.SLDPRT

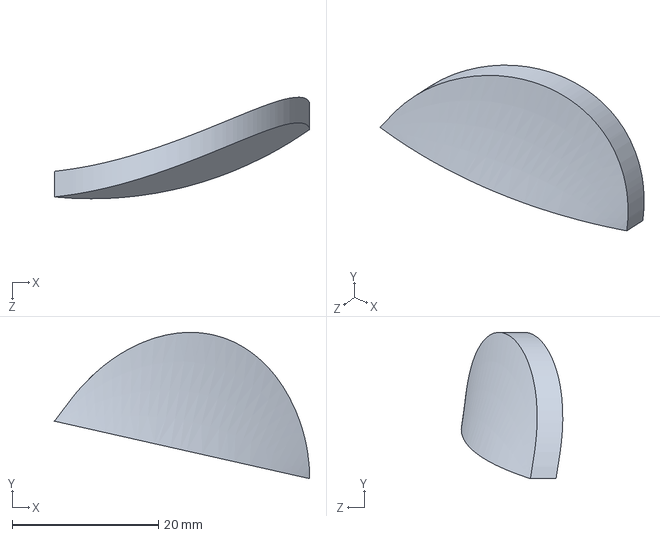
[picture p101: CAD file, 2025-11-29]
Solidworks/R2-L2_Button.SLDPRT
34.8 x 20.0 x 13.9 mm
