tschicki/PS2-Portable/_LIBRARIES/3D/LTST-C155KGJRKT.STEP

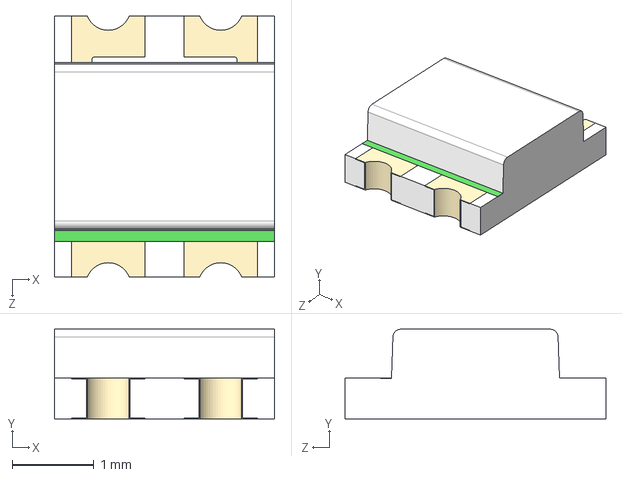
[picture p102: CAD file, 2025-11-29]
_LIBRARIES/3D/LTST-C155KGJRKT.STEP
2.70 x 1.10 x 3.20 mm
