tschicki/PS2-Portable/Solidworks/OTS_Parts/Home PSVITA2000.SLDPRT

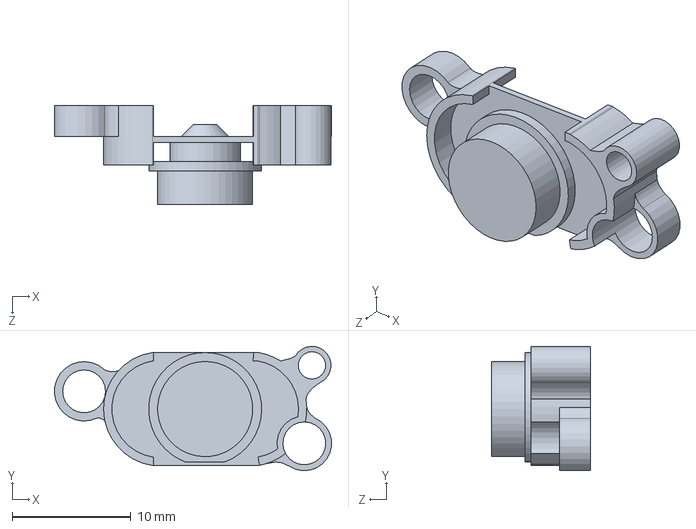
[picture p103: CAD file, 2025-11-29]
Solidworks/OTS_Parts/Home PSVITA2000.SLDPRT
23.3 x 10.5 x 8.30 mm
