tschicki/PS2-Portable/Solidworks/Output/Output Assembly/Travel Case Bot REF2021.SLDPRT

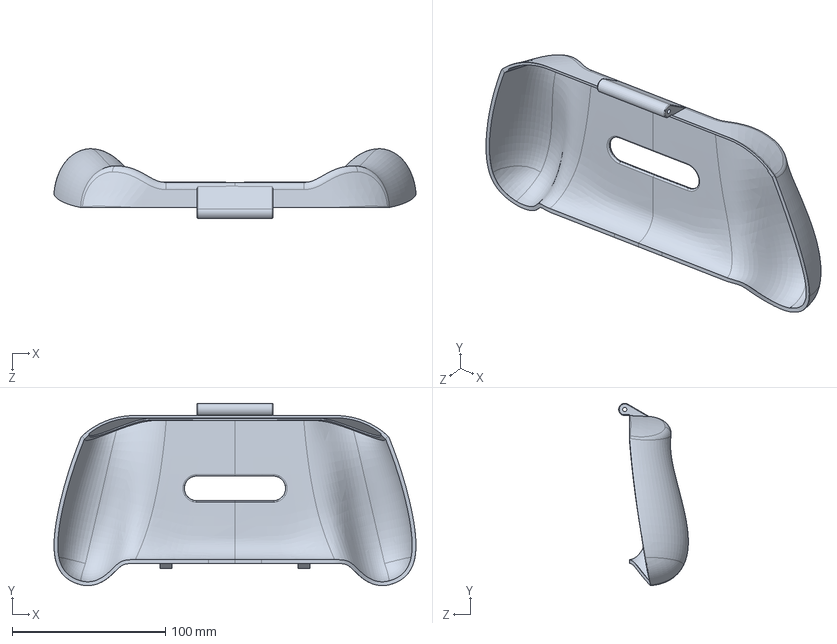
[picture p104: CAD file, 2025-11-29]
Solidworks/Output/Output Assembly/Travel Case Bot REF2021.SLDPRT
236.2 x 119.0 x 45.5 mm
