tschicki/PS2-Portable/_LIBRARIES/3D/TL3301NFxxxxG.stp

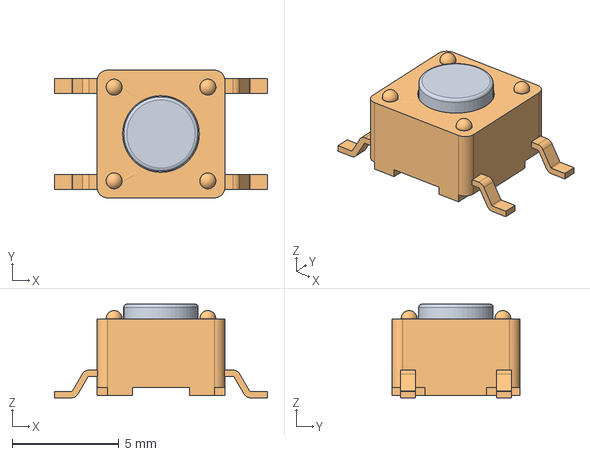
[picture p105: CAD file, 2025-11-29]
_LIBRARIES/3D/TL3301NFxxxxG.stp
10.0 x 6.00 x 4.40 mm
