tschicki/PS2-Portable/Solidworks/OTS_Parts/Attack Button PSVITA2000.SLDPRT

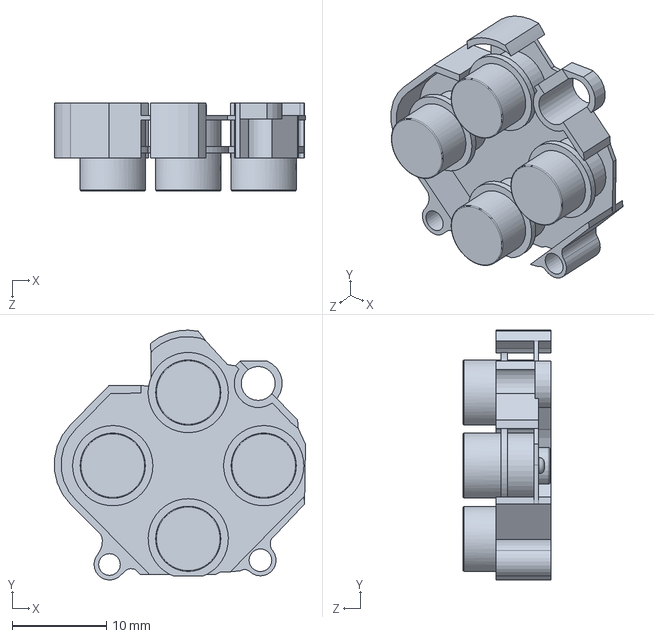
[picture p106: CAD file, 2025-11-29]
Solidworks/OTS_Parts/Attack Button PSVITA2000.SLDPRT
26.6 x 26.5 x 9.30 mm
