tschicki/PS2-Portable/Solidworks/Output/STL/Export - Button Cover Right REF2003-1.STL

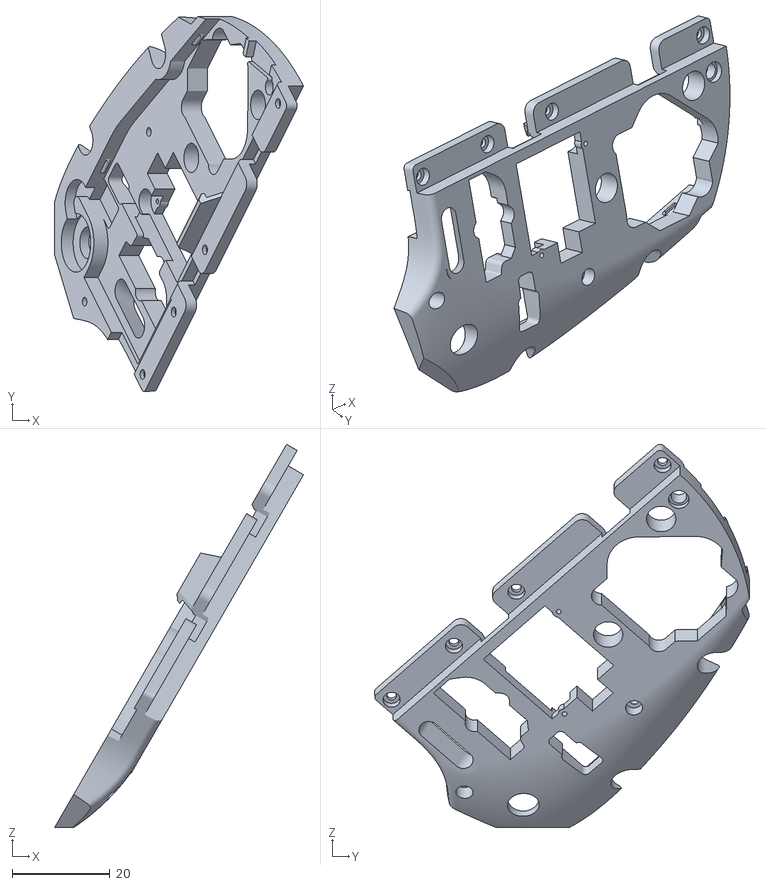
[picture p107: CAD file, 2026-04-04]
Solidworks/Output/STL/Export - Button Cover Right REF2003-1.STL
50.8 x 76.5 x 78.3
