tschicki/PS2-Portable/Solidworks/OTS_Parts/Bivar_PLP1_100.SLDPRT

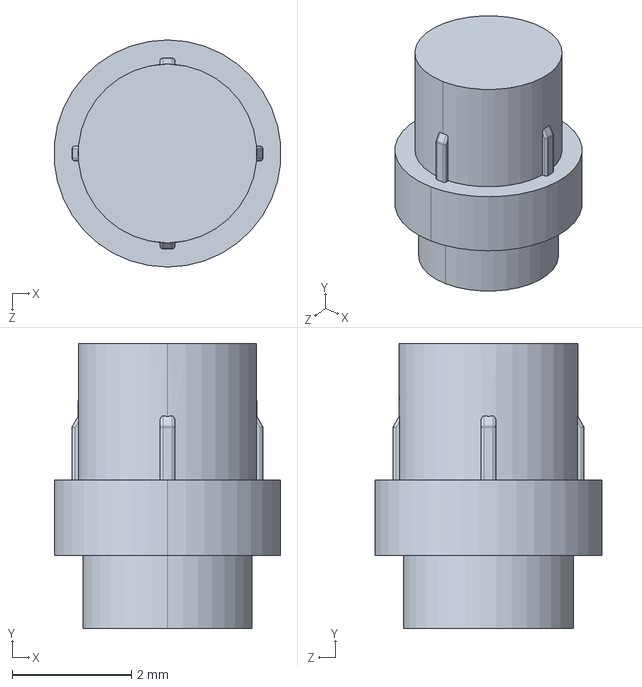
[picture p108: CAD file, 2025-11-29]
Solidworks/OTS_Parts/Bivar_PLP1_100.SLDPRT
3.80 x 4.78 x 3.81 mm
