tschicki/PS2-Portable/_LIBRARIES/3D/SM03B-SRSS-TB_LF__SN_.step

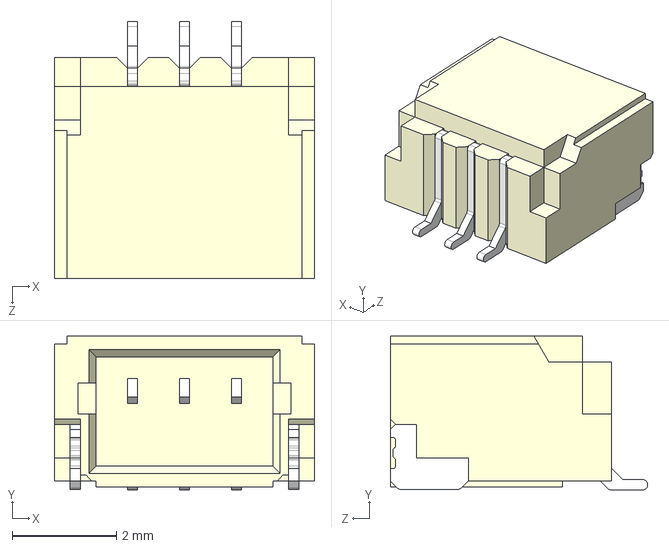
[picture p109: CAD file, 2025-11-29]
_LIBRARIES/3D/SM03B-SRSS-TB_LF__SN_.step
5.00 x 2.96 x 4.95 mm
