tschicki/PS2-Portable/Solidworks/Display_Stand.SLDPRT

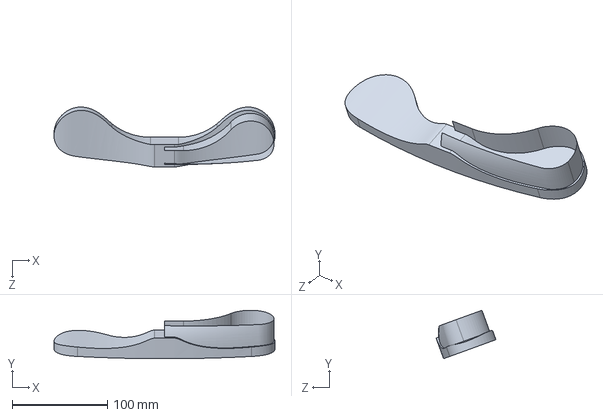
[picture p110: CAD file, 2025-11-29]
Solidworks/Display_Stand.SLDPRT
232.1 x 50.9 x 62.9 mm
