tschicki/PS2-Portable/Solidworks/OTS_Parts/switch_oled_speaker.SLDPRT

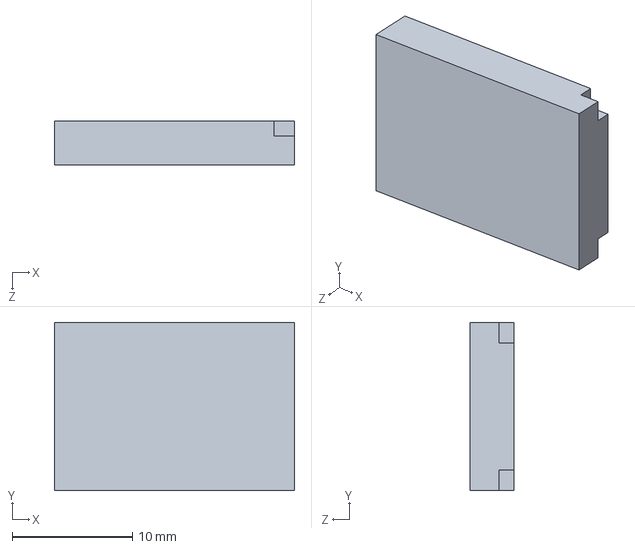
[picture p111: CAD file, 2025-11-29]
Solidworks/OTS_Parts/switch_oled_speaker.SLDPRT
20.0 x 14.0 x 3.65 mm
