tschicki/PS2-Portable/_LIBRARIES/3D/PS2_Controller_Socket.STEP

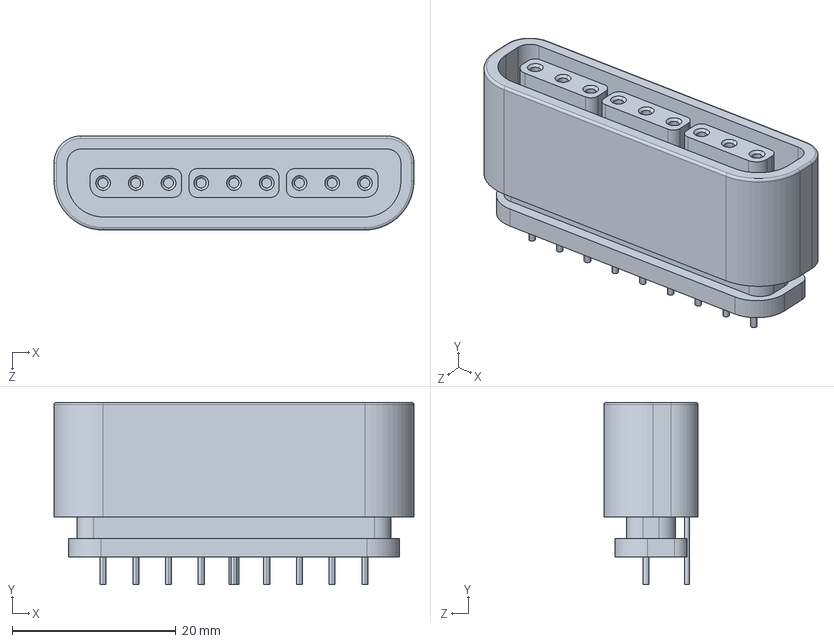
[picture p112: CAD file, 2025-11-29]
_LIBRARIES/3D/PS2_Controller_Socket.STEP
44.0 x 22.3 x 11.5 mm
