tschicki/PS2-Portable/Solidworks/Lower_Display_Mount.SLDPRT

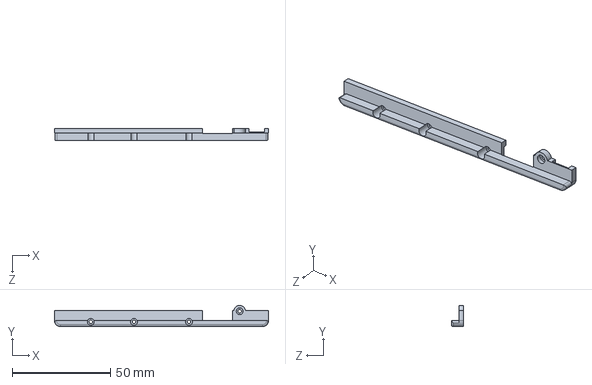
[picture p113: CAD file, 2025-11-29]
Solidworks/Lower_Display_Mount.SLDPRT
109.0 x 10.8 x 6.30 mm
