tschicki/PS2-Portable/Solidworks/OTS_Parts/LCD_5_INCH.SLDPRT

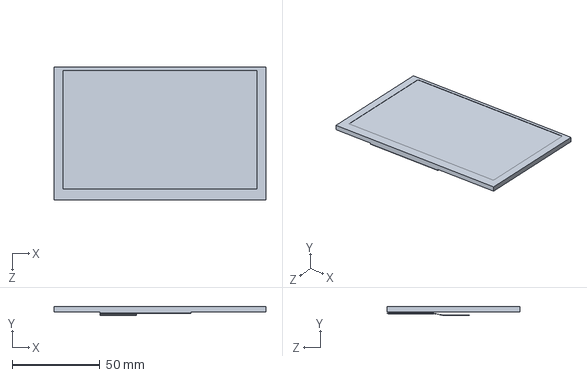
[picture p114: CAD file, 2025-11-29]
Solidworks/OTS_Parts/LCD_5_INCH.SLDPRT
120.7 x 5.00 x 75.9 mm
