tschicki/PS2-Portable/Solidworks/Output/Output Assembly/R1-L1 Bar REF2010.SLDPRT

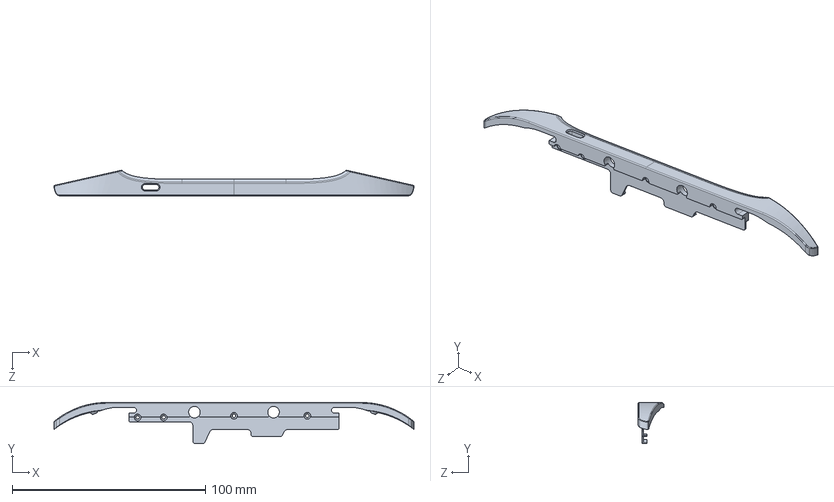
[picture p115: CAD file, 2025-11-29]
Solidworks/Output/Output Assembly/R1-L1 Bar REF2010.SLDPRT
186.4 x 21.2 x 13.3 mm
