tschicki/PS2-Portable/Solidworks/Output/STEP/Rumble Sleeve REF2015.STEP

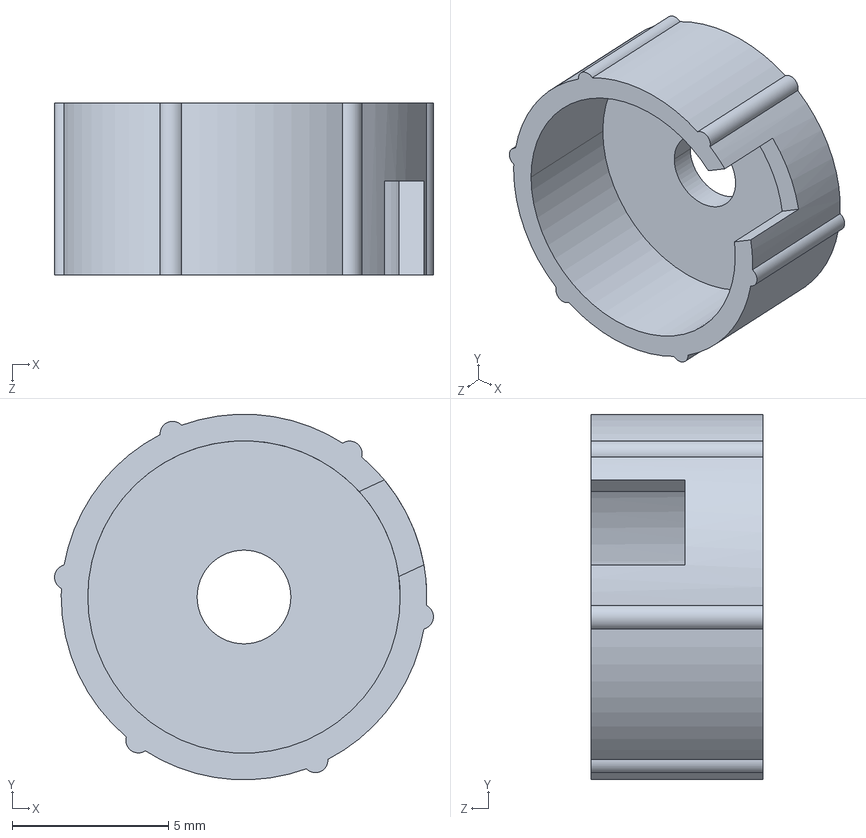
[picture p116: CAD file, 2026-04-04]
Solidworks/Output/STEP/Rumble Sleeve REF2015.STEP
12.1 x 11.7 x 5.50 mm
