tschicki/PS2-Portable/_LIBRARIES/3D/spm5030.step

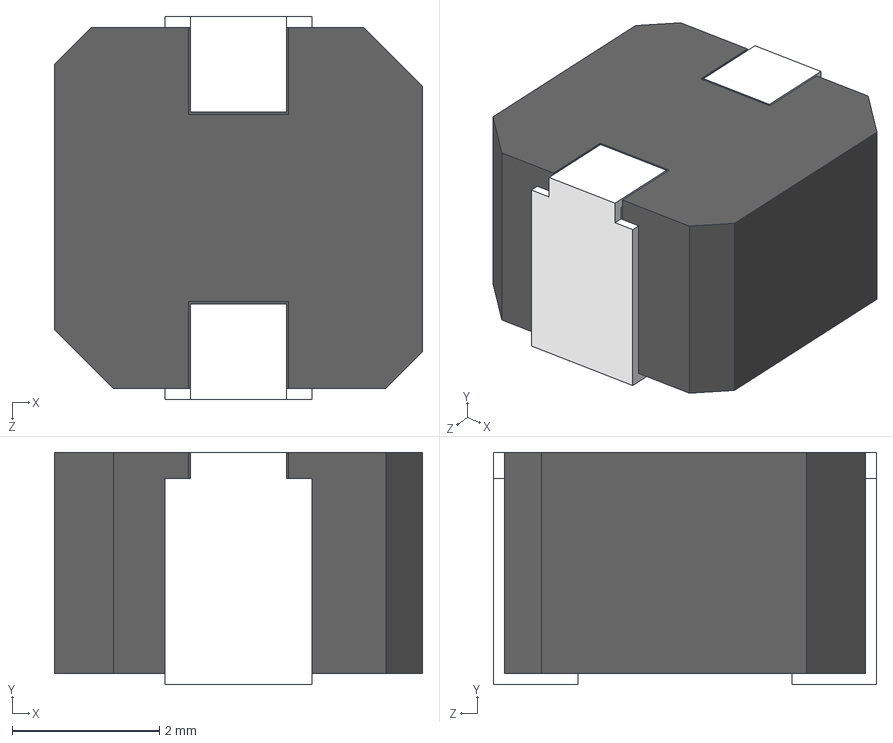
[picture p117: CAD file, 2025-11-29]
_LIBRARIES/3D/spm5030.step
5.00 x 3.15 x 5.20 mm
