tschicki/PS2-Portable/Solidworks/MemoryCard_Flex.SLDPRT

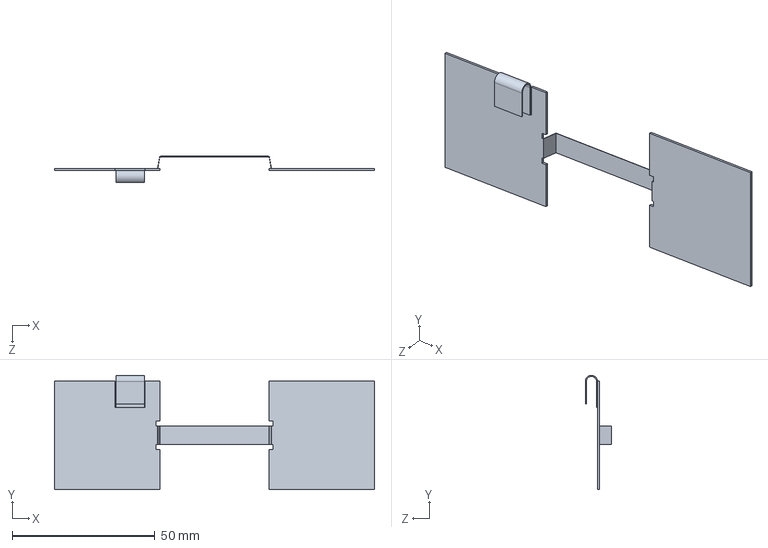
[picture p118: CAD file, 2025-11-29]
Solidworks/MemoryCard_Flex.SLDPRT
112.0 x 40.1 x 9.25 mm
