tschicki/PS2-Portable/_LIBRARIES/3D/1048_18650_holder.step

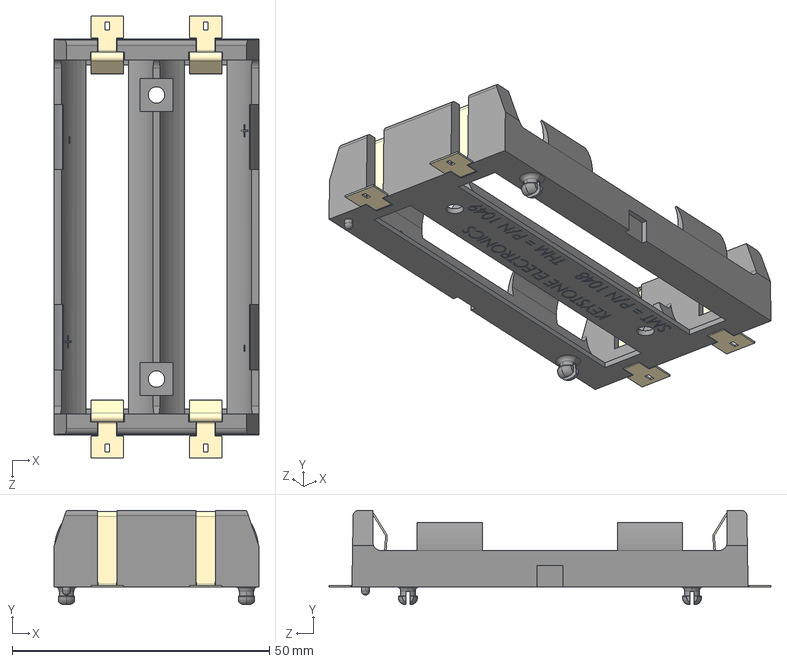
[picture p119: CAD file, 2025-11-29]
_LIBRARIES/3D/1048_18650_holder.step
39.8 x 18.3 x 86.0 mm
