tschicki/PS2-Portable/Solidworks/Output/STEP/Button Cover Left REF2002.STEP

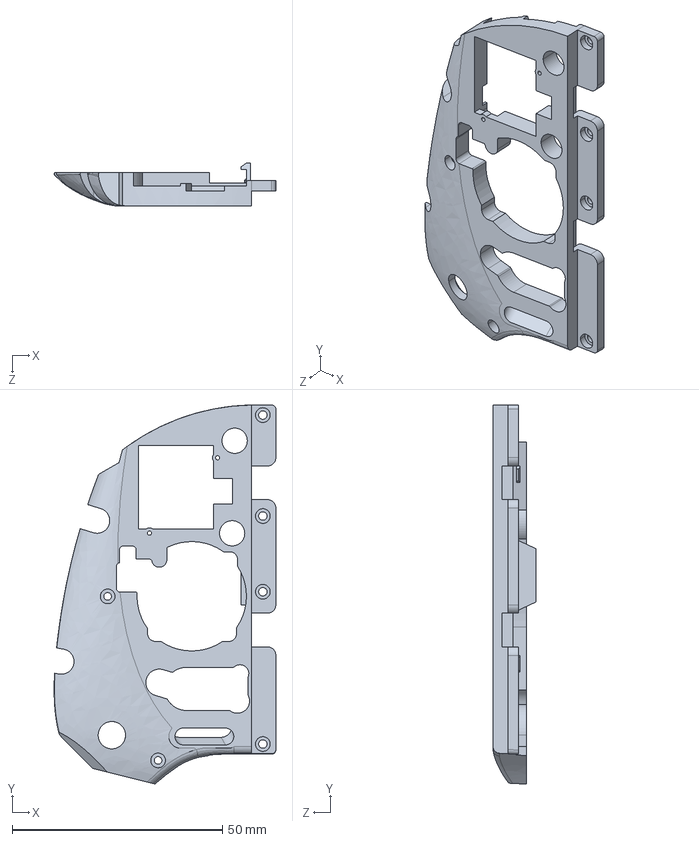
[picture p120: CAD file, 2026-04-04]
Solidworks/Output/STEP/Button Cover Left REF2002.STEP
52.7 x 90.1 x 10.2 mm
