tschicki/PS2-Portable/Solidworks/Output/STL/Export - DPAD Sanding Tool-1.STL

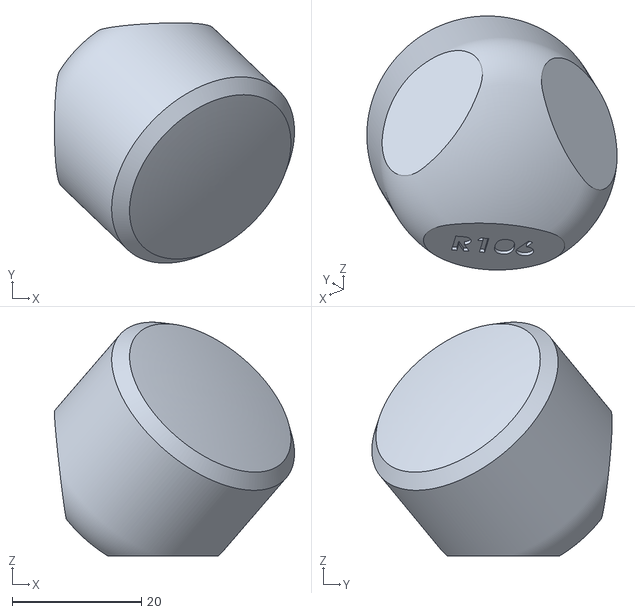
[picture p121: CAD file, 2026-04-04]
Solidworks/Output/STL/Export - DPAD Sanding Tool-1.STL
37.2 x 37.2 x 36.2
