tschicki/PS2-Portable/_LIBRARIES/3D/5134TR.step

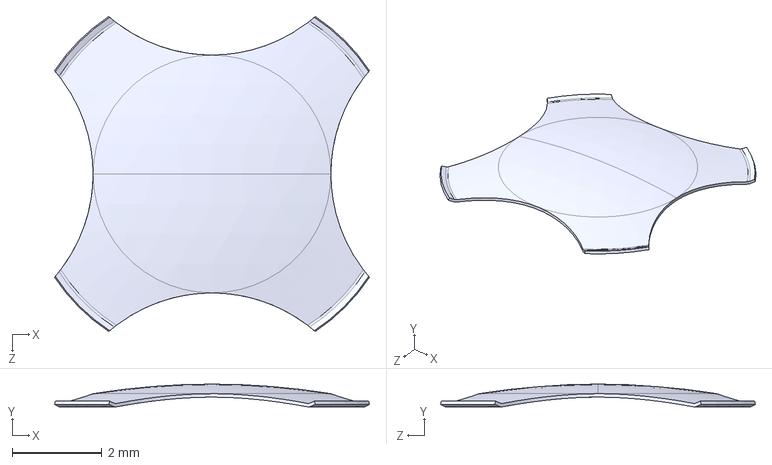
[picture p122: CAD file, 2025-11-29]
_LIBRARIES/3D/5134TR.step
7.01 x 0.508 x 7.01 mm
