tschicki/PS2-Portable/Solidworks/Output/Output Assembly/Heatsink Tapping Tool.SLDPRT

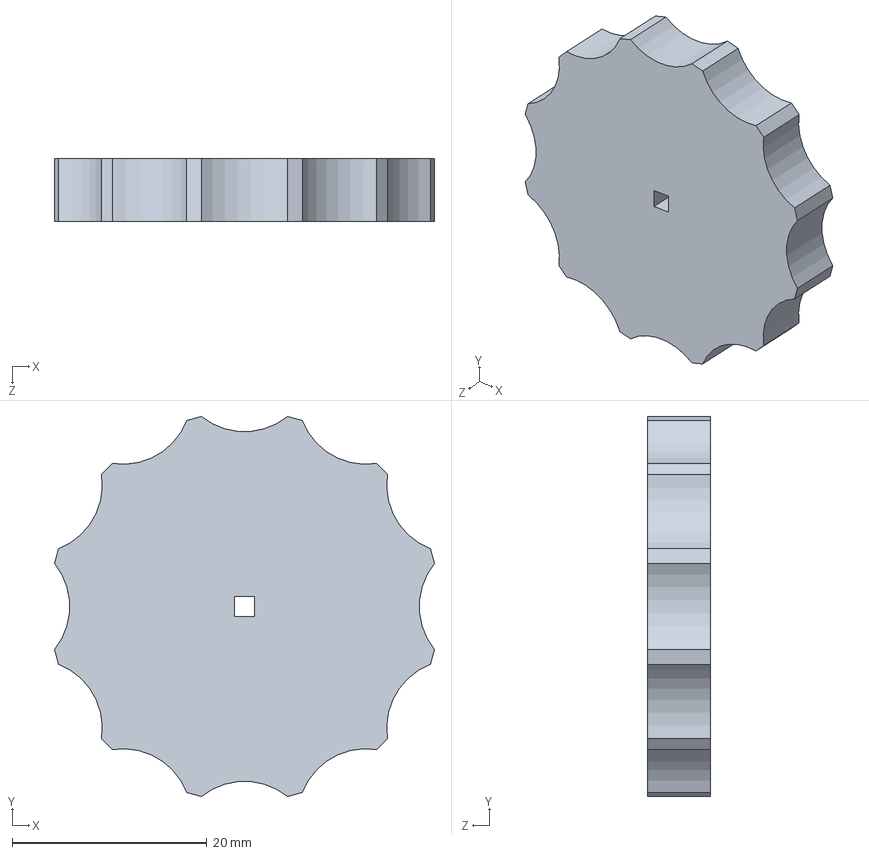
[picture p123: CAD file, 2025-11-29]
Solidworks/Output/Output Assembly/Heatsink Tapping Tool.SLDPRT
39.0 x 39.0 x 6.50 mm
