tschicki/PS2-Portable/_LIBRARIES/3D/CUI_DEVICES_SJ-3524-SMT-TR.step

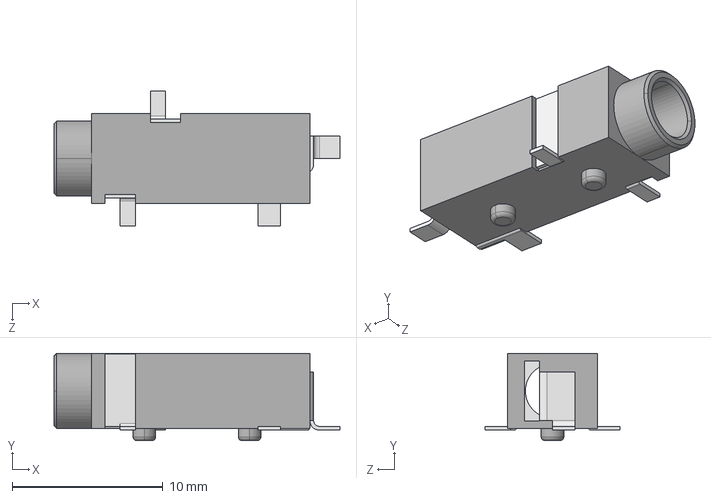
[picture p124: CAD file, 2025-11-29]
_LIBRARIES/3D/CUI_DEVICES_SJ-3524-SMT-TR.step
19.0 x 5.80 x 9.00 mm
