tschicki/PS2-Portable/Solidworks/Output/STL/Export - Travel Case Bot REF2021-1.STL

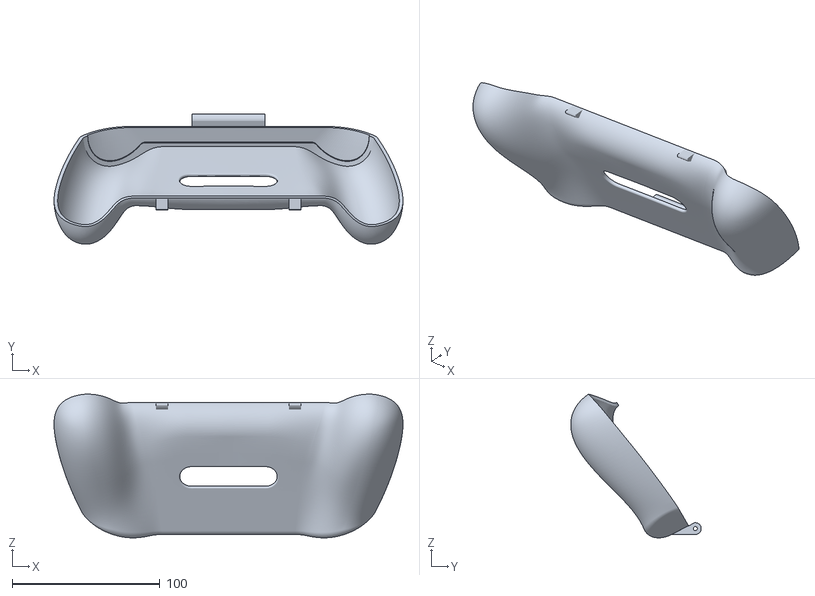
[picture p125: CAD file, 2026-04-04]
Solidworks/Output/STL/Export - Travel Case Bot REF2021-1.STL
236.2 x 88.3 x 97.3
