tschicki/PS2-Portable/Solidworks/Output/Output Assembly/Travel Case Top REF2020.SLDPRT

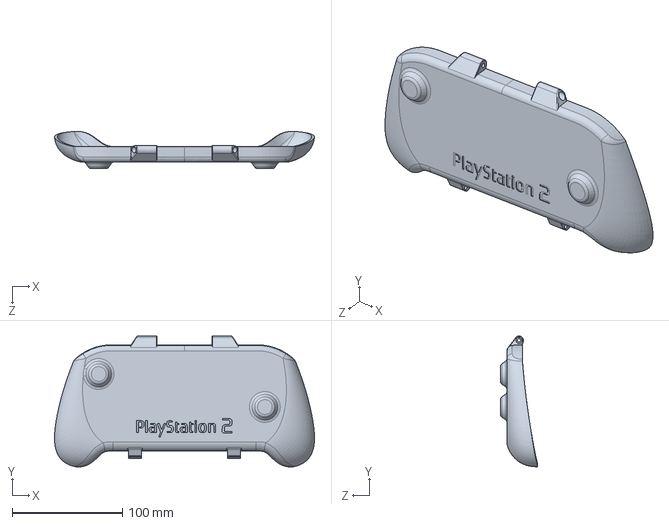
[picture p126: CAD file, 2025-11-29]
Solidworks/Output/Output Assembly/Travel Case Top REF2020.SLDPRT
236.2 x 119.0 x 33.9 mm
