tschicki/PS2-Portable/Solidworks/Output/STL/Export - L2 Button REF2011-1.STL

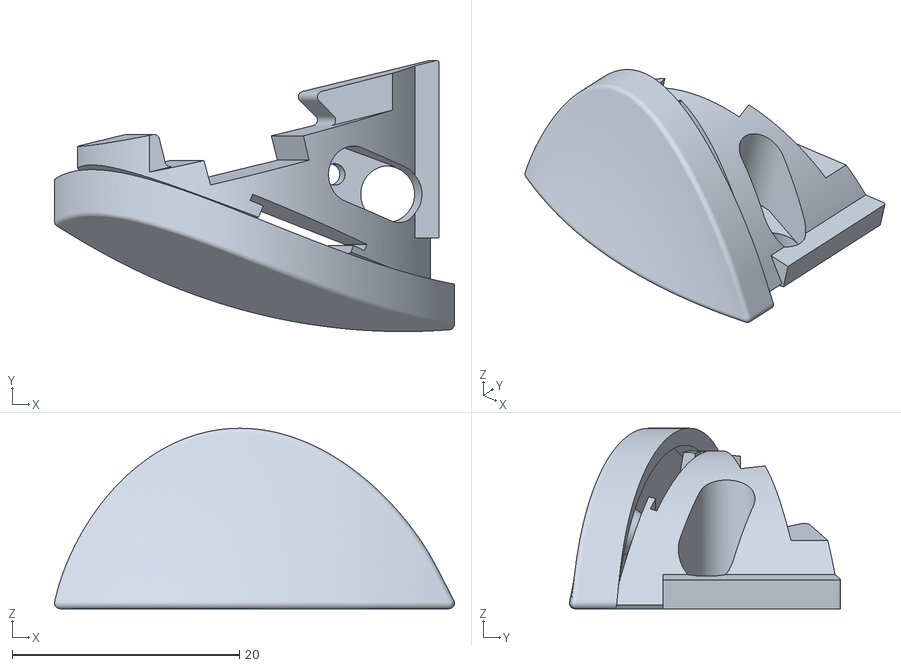
[picture p127: CAD file, 2026-04-04]
Solidworks/Output/STL/Export - L2 Button REF2011-1.STL
35.2 x 23.9 x 15.9
