tschicki/PS2-Portable/_LIBRARIES/3D/PowerPAK 1212-8.STEP

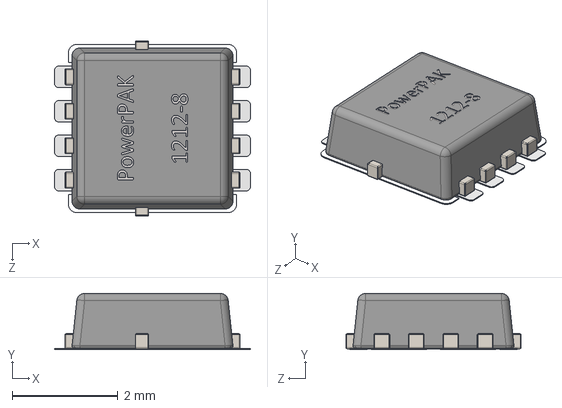
[picture p128: CAD file, 2025-11-29]
_LIBRARIES/3D/PowerPAK 1212-8.STEP
3.70 x 1.06 x 3.30 mm
