tschicki/PS2-Portable/Solidworks/Output/STL/Export - Display Stand REF2019-1.STL

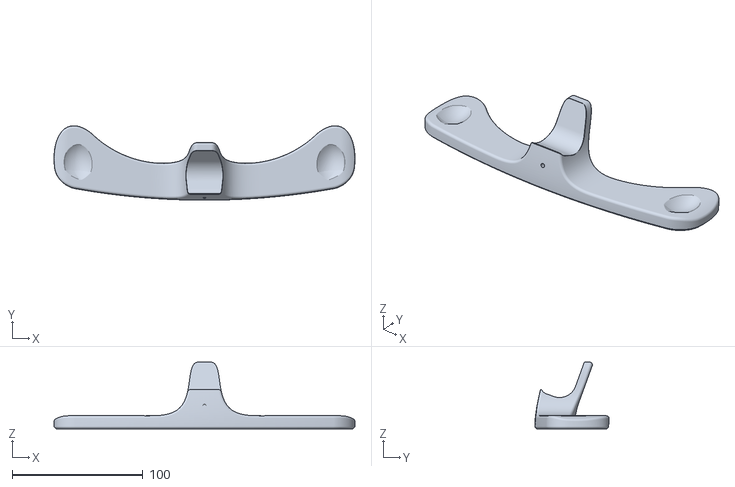
[picture p129: CAD file, 2026-04-04]
Solidworks/Output/STL/Export - Display Stand REF2019-1.STL
230.4 x 57.0 x 51.0
