tschicki/PS2-Portable/_LIBRARIES/3D/DF40C-40DP.stp

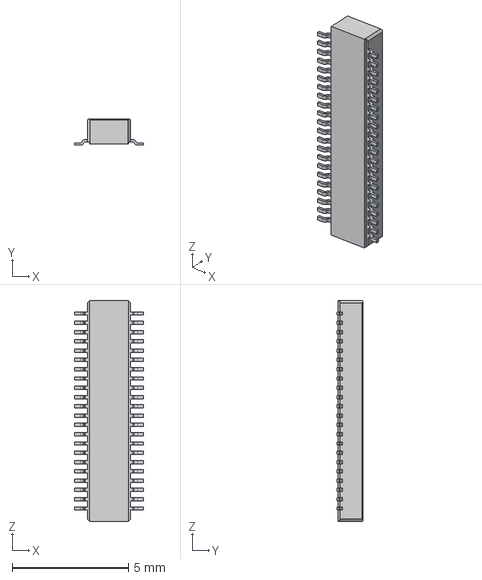
[picture p130: CAD file, 2025-11-29]
_LIBRARIES/3D/DF40C-40DP.stp
2.97 x 1.14 x 9.52 mm
