tschicki/PS2-Portable/Solidworks/Output/STL/Export - R2 Button REF2012-1.STL

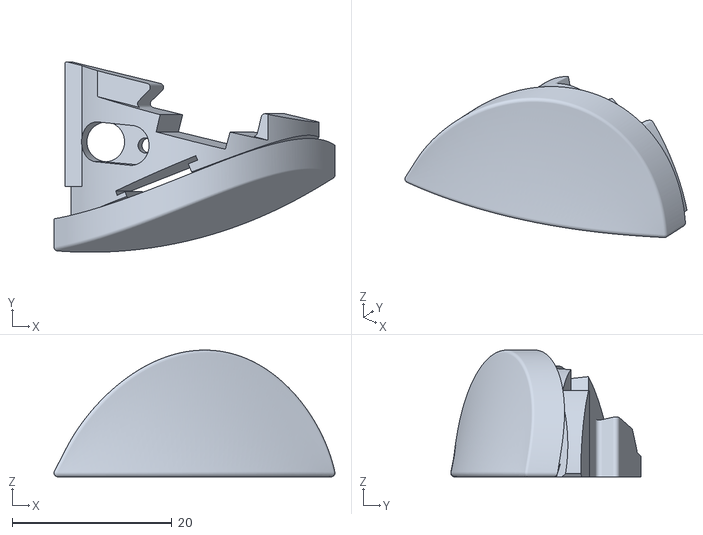
[picture p131: CAD file, 2026-04-04]
Solidworks/Output/STL/Export - R2 Button REF2012-1.STL
35.2 x 23.9 x 15.9
