tschicki/PS2-Portable/_LIBRARIES/3D/SJ-43504-SMT-TR.step

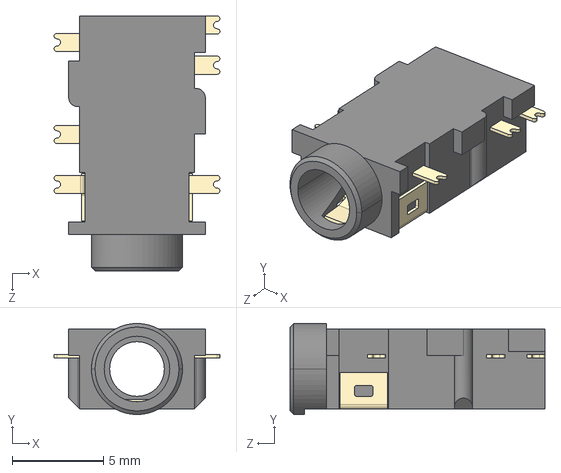
[picture p132: CAD file, 2025-11-29]
_LIBRARIES/3D/SJ-43504-SMT-TR.step
9.10 x 5.00 x 14.0 mm
