tschicki/PS2-Portable/_LIBRARIES/3D/DF40C-40DS.stp

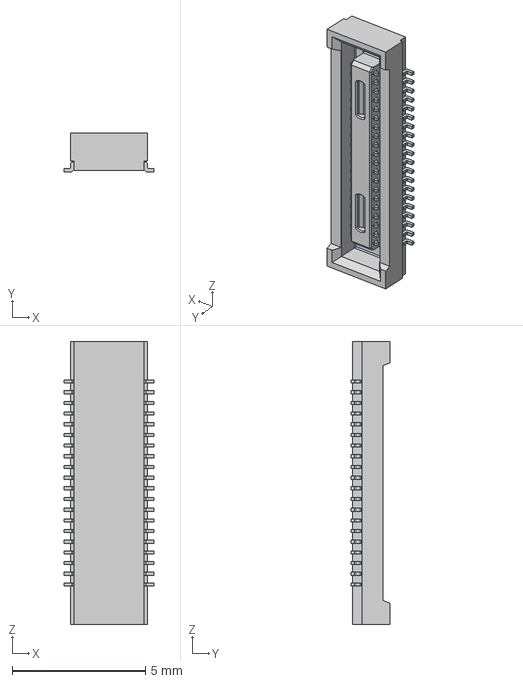
[picture p133: CAD file, 2025-11-29]
_LIBRARIES/3D/DF40C-40DS.stp
3.38 x 1.45 x 10.6 mm
