tschicki/PS2-Portable/SysCon Firmware/SysCon_FW/inc/BQ25792_Registers.h

#ifndef BQ25792_Registers_h
#define BQ25792_Registers_h
#include <stdint.h>
#include <stdio.h>
#include <string.h>


#define BQ_NO_OF_REGS UINT8_C(0x49)

/*Register Map*/
#define REG00_MINIMAL_SYSTEM_VOLTAGE UINT8_C(0x00)
    #define REG00_VSYSMIN_MASK UINT8_C(0x3F)
    #define REG00_VSYSMIN_POS UINT8_C(0x00)
#define REG01_CHARGE_VOLTAGE_LIMIT UINT8_C(0x01)
    #define REG01_VREG_MASK UINT8_C(0x07)
    #define REG01_VREG_POS UINT8_C(0x08)
#define REG02_CHARGE_VOLTAGE_LIMIT UINT8_C(0x02)
    #define REG02_VREG_MASK UINT8_C(0xFF)
    #define REG02_VREG_POS UINT8_C(0x00)
#define REG03_CHARGE_CURRENT_LIMIT UINT8_C(0x03)
    #define REG03_ICHG_MASK UINT8_C(0x01)
    #define REG03_ICHG_POS UINT8_C(0x08)
#define REG04_CHARGE_CURRENT_LIMIT UINT8_C(0x04)
    #define REG04_ICHG_MASK UINT8_C(0xFF)
    #define REG04_ICHG_POS UINT8_C(0x00)
#define REG05_INPUT_VOLTAGE_LIMIT UINT8_C(0x05)
    #define REG05_VINDPM_MASK UINT8_C(0xFF)
    #define REG05_VINDPM_POS UINT8_C(0x00)
#define REG06_INPUT_CURRENT_LIMIT UINT8_C(0x06)
    #define REG06_IINDPM_MASK UINT8_C(0x01)
    #define REG06_IINDPM_POS UINT8_C(0x08)
#define REG07_INPUT_CURRENT_LIMIT UINT8_C(0x07)
    #define REG07_IINDPM_MASK UINT8_C(0xFF)
    #define REG07_IINDPM_POS UINT8_C(0x00)
#define REG08_PRECHARGE_CONTROL UINT8_C(0x08)
    #define REG08_IPRECHG_MASK UINT8_C(0x3F)
    #define REG08_VBATLOWV_MASK UINT8_C(0xC0)
    #define REG08_IPRECHG_POS UINT8_C(0x00)
    #define REG08_VBATLOWV_POS UINT8_C(0x06)
#define REG09_TERMINATION_CONTROL UINT8_C(0x09)
    #define REG09_ITERM_MASK UINT8_C(0x1F)
    #define REG09_REG_RST_MASK UINT8_C(0x40)
    #define REG09_ITERM_POS UINT8_C(0x00)
    #define REG09_REG_RST_POS UINT8_C(0x06)
#define REG0A_RE_CHARGE_CONTROL UINT8_C(0x0A)
    #define REG0A_VRECHG_MASK UINT8_C(0x0F)
    #define REG0A_TRECHG_MASK UINT8_C(0x30)
    #define REG0A_CELL_MASK UINT8_C(0xC0)
    #define REG0A_VRECHG_POS UINT8_C(0x00)
    #define REG0A_TRECHG_POS UINT8_C(0x04)
    #define REG0A_CELL_POS UINT8_C(0x06)
#define REG0B_VOTG_REGULATION UINT8_C(0x0B)
    #define REG0B_VOTG_MASK UINT8_C(0x07)
    #define REG0B_VOTG_POS UINT8_C(0x08)
#define REG0C_VOTG_REGULATION UINT8_C(0x0C)
    #define REG0C_VOTG_MASK UINT8_C(0xFF)
    #define REG0C_VOTG_POS UINT8_C(0x00)
#define REG0D_IOTG_REGULATION UINT8_C(0x0D)
    #define REG0D_IOTG_MASK UINT8_C(0x7F)
    #define REG0D_PRECHG_TMR_MASK UINT8_C(0x80)
    #define REG0D_IOTG_POS UINT8_C(0x00)
    #define REG0D_PRECHG_TMR_POS UINT8_C(0x07)
#define REG0E_TIMER_CONTROL UINT8_C(0x0E)
    #define REG0E_TMR2X_EN_MASK UINT8_C(0x01)
    #define REG0E_CHG_TMR_MASK UINT8_C(0x06)
    #define REG0E_EN_CHG_TMR_MASK UINT8_C(0x08)
    #define REG0E_EN_PRECHG_TMR_MASK UINT8_C(0x10)
    #define REG0E_EN_TRICHG_TMR_MASK UINT8_C(0x20)
    #define REG0E_TOPOFF_TMR_MASK UINT8_C(0xC0)
    #define REG0E_TMR2X_EN_POS UINT8_C(0x00)
    #define REG0E_CHG_TMR_POS UINT8_C(0x01)
    #define REG0E_EN_CHG_TMR_POS UINT8_C(0x03)
    #define REG0E_EN_PRECHG_TMR_POS UINT8_C(0x04)
    #define REG0E_EN_TRICHG_TMR_POS UINT8_C(0x05)
    #define REG0E_TOPOFF_TMR_POS UINT8_C(0x06)
#define REG0F_CHARGER_CONTROL_0 UINT8_C(0x0F)
    #define REG0F_EN_TERM_MASK UINT8_C(0x02)
    #define REG0F_EN_HIZ_MASK UINT8_C(0x04)
    #define REG0F_FORCE_ICO_MASK UINT8_C(0x08)
    #define REG0F_EN_ICO_MASK UINT8_C(0x10)
    #define REG0F_EN_CHG_MASK UINT8_C(0x20)
    #define REG0F_FORCE_IBATDIS_MASK UINT8_C(0x40)
    #define REG0F_EN_AUTO_IBATDIS_MASK UINT8_C(0x80)
    #define REG0F_EN_TERM_POS UINT8_C(0x01)
    #define REG0F_EN_HIZ_POS UINT8_C(0x02)
    #define REG0F_FORCE_ICO_POS UINT8_C(0x08)
    #define REG0F_EN_ICO_POS UINT8_C(0x03)
    #define REG0F_EN_CHG_POS UINT8_C(0x05)
    #define REG0F_FORCE_IBATDIS_POS UINT8_C(0x06)
    #define REG0F_EN_AUTO_IBATDIS_POS UINT8_C(0x07)
#define REG10_CHARGER_CONTROL_1 UINT8_C(0x10)
    #define REG10_WATCHDOG_MASK UINT8_C(0x07)
    #define REG10_WD_RST_MASK UINT8_C(0x08)
    #define REG10_VAC_OVP_MASK UINT8_C(0x30)
    #define REG10_WATCHDOG_POS UINT8_C(0x00)
    #define REG10_WD_RST_POS UINT8_C(0x03)
    #define REG10_VAC_OVP_POS UINT8_C(0x04)
#define REG11_CHARGER_CONTROL_2 UINT8_C(0x11)
    #define REG11_SDRV_DLY_MASK UINT8_C(0x01)
    #define REG11_SDRV_CTRL_MASK UINT8_C(0x06)
    #define REG11_HVDCP_EN_MASK UINT8_C(0x08)
    #define REG11_EN_9V_MASK UINT8_C(0x10)
    #define REG11_EN_12V_MASK UINT8_C(0x20)
    #define REG11_AUTO_INDET_EN_MASK UINT8_C(0x40)
    #define REG11_FORCE_IDENT_MASK UINT8_C(0x80)
    #define REG11_SDRV_DLY_POS UINT8_C(0x00)
    #define REG11_SDRV_CTRL_POS UINT8_C(0x01)
    #define REG11_HVDCP_EN_POS UINT8_C(0x03)
    #define REG11_EN_9V_POS UINT8_C(0x04)
    #define REG11_EN_12V_POS UINT8_C(0x05)
    #define REG11_AUTO_INDET_EN_POS UINT8_C(0x06)
    #define REG11_FORCE_IDENT_POS UINT8_C(0x07)
#define REG12_CHARGER_CONTROL_3 UINT8_C(0x12)
    #define REG12_DIS_FWD_OOA_MASK UINT8_C(0x01)
    #define REG12_DIS_OTG_OOA_MASK UINT8_C(0x02)
    #define REG12_DIS_LDO_MASK UINT8_C(0x04)
    #define REG12_WKUP_DLY_MASK UINT8_C(0x08)
    #define REG12_PFM_FWD_DIS_MASK UINT8_C(0x10)
    #define REG12_PFM_OTG_DIS_MASK UINT8_C(0x20)
    #define REG12_EN_OTG_MASK UINT8_C(0x40)
    #define REG12_DIS_ACDRV_MASK UINT8_C(0x80)
    #define REG12_DIS_FWD_OOA_POS UINT8_C(0x00)
    #define REG12_DIS_OTG_OOA_POS UINT8_C(0x01)
    #define REG12_DIS_LDO_POS UINT8_C(0x02)
    #define REG12_WKUP_DLY_POS UINT8_C(0x03)
    #define REG12_PFM_FWD_DIS_POS UINT8_C(0x04)
    #define REG12_PFM_OTG_DIS_POS UINT8_C(0x05)
    #define REG12_EN_OTG_POS UINT8_C(0x06)
    #define REG12_DIS_ACDRV_POS UINT8_C(0x07)
#define REG13_CHARGER_CONTROL_4 UINT8_C(0x13)
    #define REG13_EN_IBUS_OCP_MASK UINT8_C(0x01)
    #define REG13_FORCE_VINDPM_DET_MASK UINT8_C(0x02)
    #define REG13_DIS_VOTG_UVP_MASK UINT8_C(0x04)
    #define REG13_DIS_VSYS_SHORT_MASK UINT8_C(0x08)
    #define REG13_DIS_STAT_MASK UINT8_C(0x10)
    #define REG13_PWM_FREQ_MASK UINT8_C(0x20)
    #define REG13_EN_ACDRV1_MASK UINT8_C(0x40)
    #define REG13_EN_ACDRV2_MASK UINT8_C(0x80)
    #define REG13_EN_IBUS_OCP_POS UINT8_C(0x00)
    #define REG13_FORCE_VINDPM_DET_POS UINT8_C(0x01)
    #define REG13_DIS_VOTG_UVP_POS UINT8_C(0x02)
    #define REG13_DIS_VSYS_SHORT_POS UINT8_C(0x03)
    #define REG13_DIS_STAT_POS UINT8_C(0x04)
    #define REG13_PWM_FREQ_POS UINT8_C(0x05)
    #define REG13_EN_ACDRV1_POS UINT8_C(0x06)
    #define REG13_EN_ACDRV2_POS UINT8_C(0x07)
#define REG14_CHARGER_CONTROL_5 UINT8_C(0x14)
    #define REG14_EN_BATOC_MASK UINT8_C(0x01)
    #define REG14_EN_EXTILIM_MASK UINT8_C(0x02)
    #define REG14_EN_IINDPM_MASK UINT8_C(0x04)
    #define REG14_IBAT_REG_MASK UINT8_C(0x18)
    #define REG14_EN_IBAT_MASK UINT8_C(0x20)
    #define REG14_SFET_PRESENT_MASK UINT8_C(0x80)
    #define REG14_EN_BATOC_POS UINT8_C(0x00)
    #define REG14_EN_EXTILIM_POS UINT8_C(0x01)
    #define REG14_EN_IINDPM_POS UINT8_C(0x02)
    #define REG14_IBAT_REG_POS UINT8_C(0x03)
    #define REG14_EN_IBAT_POS UINT8_C(0x05)
    #define REG14_SFET_PRESENT_POS UINT8_C(0x07)
#define REG15_RESERVED UINT8_C(0x15)
#define REG16_TEMPERATURE_CONTROL UINT8_C(0x16)
    #define REG16_VAC2_PD_EN_MASK UINT8_C(0x02)
    #define REG16_VAC1_PD_EN_MASK UINT8_C(0x04)
    #define REG16_VBUS_PD_EN_MASK UINT8_C(0x08)
    #define REG16_TSHUT_MASK UINT8_C(0x30)
    #define REG16_TREG_MASK UINT8_C(0xC0)
    #define REG16_VAC2_PD_EN_POS UINT8_C(0x01)
    #define REG16_VAC1_PD_EN_POS UINT8_C(0x02)
    #define REG16_VBUS_PD_EN_POS UINT8_C(0x03)
    #define REG16_TSHUT_POS UINT8_C(0x04)
    #define REG16_TREG_POS UINT8_C(0x06)
#define REG17_NTC_CONTROL_0 UINT8_C(0x17)
    #define REG17_JEITA_ISETC_MASK UINT8_C(0x06)
    #define REG17_JEITA_ISETH_MASK UINT8_C(0x18)
    #define REG17_JEITA_VSET_MASK UINT8_C(0xE0)
    #define REG17_JEITA_ISETC_POS UINT8_C(0x01)
    #define REG17_JEITA_ISETH_POS UINT8_C(0x03)
    #define REG17_JEITA_VSET_POS UINT8_C(0x05)
#define REG18_NTC_CONTROL_1 UINT8_C(0x18)
    #define REG18_TS_IGNORE_MASK UINT8_C(0x01)
    #define REG18_BCOLD_MASK UINT8_C(0x02)
    #define REG18_BHOT_MASK UINT8_C(0x0C)
    #define REG18_TS_WARM_MASK UINT8_C(0x30)
    #define REG18_TS_COOL_MASK UINT8_C(0xC0)
    #define REG18_TS_IGNORE_POS UINT8_C(0x00)
    #define REG18_BCOLD_POS UINT8_C(0x01)
    #define REG18_BHOT_POS UINT8_C(0x02)
    #define REG18_TS_WARM_POS UINT8_C(0x04)
    #define REG18_TS_COOL_POS UINT8_C(0x06)
#define REG19_ICO_CURRENT_LIMIT UINT8_C(0x19)
    #define REG19_ICO_ILIM_MASK UINT8_C(0x01)
    #define REG19_ICO_ILIM_POS UINT8_C(0x08)
#define REG1A_ICO_CURRENT_LIMIT UINT8_C(0x1A)
    #define REG1A_ICO_ILIM_MASK UINT8_C(0xFF)
    #define REG1A_ICO_ILIM_POS UINT8_C(0x00)
#define REG1B_CHARGER_STATUS_0 UINT8_C(0x1B)
    #define REG1B_VBUS_PRESENT_STAT_MASK UINT8_C(0x01)
    #define REG1B_AC1_PRESENT_STAT_MASK UINT8_C(0x02)
    #define REG1B_AC2_PRESENT_STAT_MASK UINT8_C(0x04)
    #define REG1B_PG_STAT_MASK UINT8_C(0x08)
    #define REG1B_POORSRC_STAT_MASK UINT8_C(0x10)
    #define REG1B_WD_STAT_MASK UINT8_C(0x20)
    #define REG1B_VINDPM_STAT_MASK UINT8_C(0x40)
    #define REG1B_IINDPM_STAT_MASK UINT8_C(0x80)
    #define REG1B_VBUS_PRESENT_STAT_POS UINT8_C(0x00)
    #define REG1B_AC1_PRESENT_STAT_POS UINT8_C(0x01)
    #define REG1B_AC2_PRESENT_STAT_POS UINT8_C(0x02)
    #define REG1B_PG_STAT_POS UINT8_C(0x03)
    #define REG1B_POORSRC_STAT_POS UINT8_C(0x04)
    #define REG1B_WD_STAT_POS UINT8_C(0x05)
    #define REG1B_VINDPM_STAT_POS UINT8_C(0x06)
    #define REG1B_IINDPM_STAT_POS UINT8_C(0x07)
#define REG1C_CHARGER_STATUS_1 UINT8_C(0x1C)
    #define REG1C_BC12_DONE_STAT_MASK UINT8_C(0x01)
    #define REG1C_VBUS_STAT_MASK UINT8_C(0x1E)
    #define REG1C_CHG_STAT_MASK UINT8_C(0xE0)
    #define REG1C_BC12_DONE_STAT_POS UINT8_C(0x00)
    #define REG1C_VBUS_STAT_POS UINT8_C(0x01)
    #define REG1C_CHG_STAT_POS UINT8_C(0x05)
#define REG1D_CHARGER_STATUS_2 UINT8_C(0x1D)
    #define REG1D_VBAT_PRESENT_STAT_MASK UINT8_C(0x01)
    #define REG1D_DPDM_STAT_MASK UINT8_C(0x02)
    #define REG1D_TREG_STAT_MASK UINT8_C(0x04)
    #define REG1D_ICO_STAT_MASK UINT8_C(0xC0)
    #define REG1D_VBAT_PRESENT_STAT_POS UINT8_C(0x00)
    #define REG1D_DPDM_STAT_POS UINT8_C(0x01)
    #define REG1D_TREG_STAT_POS UINT8_C(0x02)
    #define REG1D_ICO_STAT_POS UINT8_C(0x06)
#define REG1E_CHARGER_STATUS_3 UINT8_C(0x1E)
    #define REG1E_PRECHG_TMR_STAT_MASK UINT8_C(0x02)
    #define REG1E_TRICHG_TMR_STAT_MASK UINT8_C(0x04)
    #define REG1E_CHG_TMR_STAT_MASK UINT8_C(0x08)
    #define REG1E_VSYS_STAT_MASK UINT8_C(0x10)
    #define REG1E_ADC_DONE_STAT_MASK UINT8_C(0x20)
    #define REG1E_ACRB1_STAT_MASK UINT8_C(0x40)
    #define REG1E_ACRB2_STAT_MASK UINT8_C(0x80)
    #define REG1E_PRECHG_TMR_STAT_POS UINT8_C(0x01)
    #define REG1E_TRICHG_TMR_STAT_POS UINT8_C(0x02)
    #define REG1E_CHG_TMR_STAT_POS UINT8_C(0x03)
    #define REG1E_VSYS_STAT_POS UINT8_C(0x04)
    #define REG1E_ADC_DONE_STAT_POS UINT8_C(0x05)
    #define REG1E_ACRB1_STAT_POS UINT8_C(0x06)
    #define REG1E_ACRB2_STAT_POS UINT8_C(0x07)
#define REG1F_CHARGER_STATUS_4 UINT8_C(0x1F)
    #define REG1F_TS_HOT_STAT_MASK UINT8_C(0x01)
    #define REG1F_TS_WARM_STAT_MASK UINT8_C(0x02)
    #define REG1F_TS_COOL_STAT_MASK UINT8_C(0x04)
    #define REG1F_TS_COLD_STAT_MASK UINT8_C(0x08)
    #define REG1F_VBATOTG_LOW_STAT_MASK UINT8_C(0x10)
    #define REG1F_TS_HOT_STAT_POS UINT8_C(0x00)
    #define REG1F_TS_WARM_STAT_POS UINT8_C(0x01)
    #define REG1F_TS_COOL_STAT_POS UINT8_C(0x02)
    #define REG1F_TS_COLD_STAT_POS UINT8_C(0x03)
    #define REG1F_VBATOTG_LOW_STAT_POS UINT8_C(0x04)
#define REG20_FAULT_STATUS_0 UINT8_C(0x20)
    #define REG20_VAC1_OVP_STAT_MASK UINT8_C(0x01)
    #define REG20_VAC2_OVP_STAT_MASK UINT8_C(0x02)
    #define REG20_CONV_OCP_STAT_MASK UINT8_C(0x04)
    #define REG20_IBAT_OCP_STAT_MASK UINT8_C(0x08)
    #define REG20_IBUS_OCP_STAT_MASK UINT8_C(0x10)
    #define REG20_VBAT_OVP_STAT_MASK UINT8_C(0x20)
    #define REG20_VBUS_OVP_STAT_MASK UINT8_C(0x40)
    #define REG20_IBAT_REG_STAT_MASK UINT8_C(0x80)
    #define REG20_VAC1_OVP_STAT_POS UINT8_C(0x00)
    #define REG20_VAC2_OVP_STAT_POS UINT8_C(0x01)
    #define REG20_CONV_OCP_STAT_POS UINT8_C(0x02)
    #define REG20_IBAT_OCP_STAT_POS UINT8_C(0x03)
    #define REG20_IBUS_OCP_STAT_POS UINT8_C(0x04)
    #define REG20_VBAT_OVP_STAT_POS UINT8_C(0x05)
    #define REG20_VBUS_OVP_STAT_POS UINT8_C(0x06)
    #define REG20_IBAT_REG_STAT_POS UINT8_C(0x07)
#define REG21_FAULT_STATUS_1 UINT8_C(0x21)
    #define REG21_TSHUT_STAT_MASK UINT8_C(0x04)
    #define REG21_OTG_UVP_STAT_MASK UINT8_C(0x10)
    #define REG21_OTG_OVP_STAT_MASK UINT8_C(0x20)
    #define REG21_VSYS_OVP_STAT_MASK UINT8_C(0x40)
    #define REG21_VSYS_SHORT_STAT_MASK UINT8_C(0x80)
    #define REG21_TSHUT_STAT_POS UINT8_C(0x02)
    #define REG21_OTG_UVP_STAT_POS UINT8_C(0x04)
    #define REG21_OTG_OVP_STAT_POS UINT8_C(0x05)
    #define REG21_VSYS_OVP_STAT_POS UINT8_C(0x06)
    #define REG21_VSYS_SHORT_STAT_POS UINT8_C(0x07)
#define REG22_CHARGER_FLAG_0 UINT8_C(0x22)
    #define REG22_VBUS_PRESENT_FLAG_MASK UINT8_C(0x01)
    #define REG22_AC1_PRESENT_FLAG_MASK UINT8_C(0x02)
    #define REG22_AC2_PRESENT_FLAG_MASK UINT8_C(0x04)
    #define REG22_PG_FLAG_MASK UINT8_C(0x08)
    #define REG22_POORSRC_FLAG_MASK UINT8_C(0x10)
    #define REG22_WD_FLAG_MASK UINT8_C(0x20)
    #define REG22_VINDPM_FLAG_MASK UINT8_C(0x40)
    #define REG22_IINDPM_FLAG_MASK UINT8_C(0x80)
    #define REG22_VBUS_PRESENT_FLAG_POS UINT8_C(0x00)
    #define REG22_AC1_PRESENT_FLAG_POS UINT8_C(0x01)
    #define REG22_AC2_PRESENT_FLAG_POS UINT8_C(0x02)
    #define REG22_PG_FLAG_POS UINT8_C(0x03)
    #define REG22_POORSRC_FLAG_POS UINT8_C(0x04)
    #define REG22_WD_FLAG_POS UINT8_C(0x05)
    #define REG22_VINDPM_FLAG_POS UINT8_C(0x06)
    #define REG22_IINDPM_FLAG_POS UINT8_C(0x07)
#define REG23_CHARGER_FLAG_1 UINT8_C(0x23)
    #define REG23_BC12_DONE_FLAG_MASK UINT8_C(0x01)
    #define REG23_VBAT_PRESENT_FLAG_MASK UINT8_C(0x02)
    #define REG23_TREG_FLAG_MASK UINT8_C(0x04)
    #define REG23_VBUS_FLAG_MASK UINT8_C(0x10)
    #define REG23_ICO_FLAG_MASK UINT8_C(0x40)
    #define REG23_CHG_FLAG_MASK UINT8_C(0x80)
    #define REG23_BC12_DONE_FLAG_POS UINT8_C(0x00)
    #define REG23_VBAT_PRESENT_FLAG_POS UINT8_C(0x01)
    #define REG23_TREG_FLAG_POS UINT8_C(0x02)
    #define REG23_VBUS_FLAG_POS UINT8_C(0x04)
    #define REG23_ICO_FLAG_POS UINT8_C(0x06)
    #define REG23_CHG_FLAG_POS UINT8_C(0x07)
#define REG24_CHARGER_FLAG_2 UINT8_C(0x24)
    #define REG24_TOPOFF_TMR_FLAG_MASK UINT8_C(0x01)
    #define REG24_PRECHG_TMR_FLAG_MASK UINT8_C(0x02)
    #define REG24_TRICHG_TMR_FLAG_MASK UINT8_C(0x04)
    #define REG24_CHG_TMR_FLAG_MASK UINT8_C(0x08)
    #define REG24_VSYS_FLAG_MASK UINT8_C(0x10)
    #define REG24_ADC_DONE_FLAG_MASK UINT8_C(0x20)
    #define REG24_DPDM_DONE_FLAG_MASK UINT8_C(0x40)
    #define REG24_TOPOFF_TMR_FLAG_POS UINT8_C(0x00)
    #define REG24_PRECHG_TMR_FLAG_POS UINT8_C(0x01)
    #define REG24_TRICHG_TMR_FLAG_POS UINT8_C(0x02)
    #define REG24_CHG_TMR_FLAG_POS UINT8_C(0x03)
    #define REG24_VSYS_FLAG_POS UINT8_C(0x04)
    #define REG24_ADC_DONE_FLAG_POS UINT8_C(0x05)
    #define REG24_DPDM_DONE_FLAG_POS UINT8_C(0x06)
#define REG25_CHARGER_FLAG_3 UINT8_C(0x25)
    #define REG25_TS_HOT_FLAG_MASK UINT8_C(0x01)
    #define REG25_TS_WARM_FLAG_MASK UINT8_C(0x02)
    #define REG25_TS_COOL_FLAG_MASK UINT8_C(0x04)
    #define REG25_TS_COLD_FLAG_MASK UINT8_C(0x08)
    #define REG25_VBATOTG_LOW_FLAG_MASK UINT8_C(0x10)
    #define REG25_TS_HOT_FLAG_POS UINT8_C(0x00)
    #define REG25_TS_WARM_FLAG_POS UINT8_C(0x01)
    #define REG25_TS_COOL_FLAG_POS UINT8_C(0x02)
    #define REG25_TS_COLD_FLAG_POS UINT8_C(0x03)
    #define REG25_VBATOTG_LOW_FLAG_POS UINT8_C(0x04)
#define REG26_FAULT_FLAG_0 UINT8_C(0x26)
    #define REG26_VAC1_OVP_FLAG_MASK UINT8_C(0x01)
    #define REG26_VAC2_OVP_FLAG_MASK UINT8_C(0x02)
    #define REG26_CONV_OCP_FLAG_MASK UINT8_C(0x04)
    #define REG26_IBAT_OCP_FLAG_MASK UINT8_C(0x08)
    #define REG26_IBUS_OCP_FLAG_MASK UINT8_C(0x10)
    #define REG26_VBAT_OVP_FLAG_MASK UINT8_C(0x20)
    #define REG26_VBUS_OVP_FLAG_MASK UINT8_C(0x40)
    #define REG26_IBAT_REG_FLAG_MASK UINT8_C(0x80)
    #define REG26_VAC1_OVP_FLAG_POS UINT8_C(0x00)
    #define REG26_VAC2_OVP_FLAG_POS UINT8_C(0x01)
    #define REG26_CONV_OCP_FLAG_POS UINT8_C(0x02)
    #define REG26_IBAT_OCP_FLAG_POS UINT8_C(0x03)
    #define REG26_IBUS_OCP_FLAG_POS UINT8_C(0x04)
    #define REG26_VBAT_OVP_FLAG_POS UINT8_C(0x05)
    #define REG26_VBUS_OVP_FLAG_POS UINT8_C(0x06)
    #define REG26_IBAT_REG_FLAG_POS UINT8_C(0x07)
#define REG27_FAULT_FLAG_1 UINT8_C(0x27)
    #define REG27_TSHUT_FLAG_MASK UINT8_C(0x04)
    #define REG27_OTG_UVP_FLAG_MASK UINT8_C(0x10)
    #define REG27_OTG_OVP_FLAG_MASK UINT8_C(0x20)
    #define REG27_VSYS_OVP_FLAG_MASK UINT8_C(0x40)
    #define REG27_VSYS_SHORT_FLAG_MASK UINT8_C(0x80)
    #define REG27_TSHUT_FLAG_POS UINT8_C(0x02)
    #define REG27_OTG_UVP_FLAG_POS UINT8_C(0x04)
    #define REG27_OTG_OVP_FLAG_POS UINT8_C(0x05)
    #define REG27_VSYS_OVP_FLAG_POS UINT8_C(0x06)
    #define REG27_VSYS_SHORT_FLAG_POS UINT8_C(0x07)
#define REG28_CHARGER_MASK_0 UINT8_C(0x28)
#define REG29_CHARGER_MASK_1 UINT8_C(0x29)
#define REG2A_CHARGER_MASK_2 UINT8_C(0x2A)
#define REG2B_CHARGER_MASK_3 UINT8_C(0x2B)
#define REG2C_FAULT_MASK_0 UINT8_C(0x2C)
#define REG2D_FAULT_MASK_1 UINT8_C(0x2D)

/*Reg2E to Reg45 ADC control and ADC outputs---------------------------------------------------------*/
#define REG2E_ADC_CONTROL UINT8_C(0x2E)
    #define REG2E_ADC_AVG_INIT_MASK UINT8_C(0x04)
    #define REG2E_ADC_AVG_INIT_POS UINT8_C(0x02)
    #define REG2E_ADC_AVG_MASK UINT8_C(0x08)
    #define REG2E_ADC_AVG_POS UINT8_C(0x03)
    #define REG2E_ADC_SAMPLE_MASK UINT8_C(0x30)
    #define REG2E_ADC_SAMPLE_POS UINT8_C(0x04)
    #define REG2E_ADC_RATE_MASK UINT8_C(0x40)
    #define REG2E_ADC_RATE_POS UINT8_C(0x06)
    #define REG2E_ADC_EN_MASK UINT8_C(0x80)
    #define REG2E_ADC_EN_POS UINT8_C(0x07)
#define REG2F_ADC_FUNCTION_DISABLE_0 UINT8_C(0x2F)
    #define REG2F_TDIE_ADC_DIS_MASK UINT8_C(0x02)
    #define REG2F_TS_ADC_DIS_MASK UINT8_C(0x04)
    #define REG2F_VSYS_ADC_DIS_MASK UINT8_C(0x08)
    #define REG2F_VBAT_ADC_DIS_MASK UINT8_C(0x10)
    #define REG2F_VBUS_ADC_DIS_MASK UINT8_C(0x20)
    #define REG2F_IBAT_ADC_DIS_MASK UINT8_C(0x40)
    #define REG2F_IBUS_ADC_DIS_MASK UINT8_C(0x80)
    #define REG2F_TDIE_ADC_DIS_POS UINT8_C(0x01)
    #define REG2F_TS_ADC_DIS_POS UINT8_C(0x02)
    #define REG2F_VSYS_ADC_DIS_POS UINT8_C(0x03)
    #define REG2F_VBAT_ADC_DIS_POS UINT8_C(0x04)
    #define REG2F_VBUS_ADC_DIS_POS UINT8_C(0x05)
    #define REG2F_IBAT_ADC_DIS_POS UINT8_C(0x06)
    #define REG2F_IBUS_ADC_DIS_POS UINT8_C(0x07)
#define REG30_ADC_FUNCTION_DISABLE_1 UINT8_C(0x30)
    #define REG30_VAC1_ADC_DIS_MASK UINT8_C(0x10)
    #define REG30_VAC2_ADC_DIS_MASK UINT8_C(0x20)
    #define REG30_DM_ADC_DIS_MASK UINT8_C(0x40)
    #define REG30_DP_ADC_DIS_MASK UINT8_C(0x80)
    #define REG30_VAC1_ADC_DIS_POS UINT8_C(0x04)
    #define REG30_VAC2_ADC_DIS_POS UINT8_C(0x05)
    #define REG30_DM_ADC_DIS_POS UINT8_C(0x06)
    #define REG30_DP_ADC_DIS_POS UINT8_C(0x07)
#define REG31_IBUS_ADC_H UINT8_C(0x31)
#define REG31_IBUS_ADC_L UINT8_C(0x32)
#define REG33_IBAT_ADC_H UINT8_C(0x33)
#define REG33_IBAT_ADC_L UINT8_C(0x34)
#define REG35_VBUS_ADC_H UINT8_C(0x35)
#define REG35_VBUS_ADC_L UINT8_C(0x36)
#define REG37_VAC1_ADC_H UINT8_C(0x37)
#define REG37_VAC1_ADC_L UINT8_C(0x38)
#define REG39_VAC2_ADC_H UINT8_C(0x39)
#define REG39_VAC2_ADC_L UINT8_C(0x3A)
#define REG3B_VBAT_ADC_H UINT8_C(0x3B)
#define REG3B_VBAT_ADC_L UINT8_C(0x3C)
#define REG3D_VSYS_ADC_H UINT8_C(0x3D)
#define REG3D_VSYS_ADC_L UINT8_C(0x3E)
#define REG3F_TS_ADC_H UINT8_C(0x3F)
#define REG3F_TS_ADC_L UINT8_C(0x40)
#define REG41_TDIE_ADC_H UINT8_C(0x41)
#define REG41_TDIE_ADC_L UINT8_C(0x42)
#define REG43_DP_ADC_H UINT8_C(0x43)
#define REG43_DP_ADC_L UINT8_C(0x44)
#define REG45_DM_ADC_H UINT8_C(0x45)
#define REG45_DM_ADC_L UINT8_C(0x46)
/*-----------------------------------------------------------------------------------*/
#define REG47_DPDM_DRIVER UINT8_C(0x47)
#define REG48_PART_INFORMATION UINT8_C(0x48)
    #define REG48_PN_MASK UINT8_C(0x38)
    #define REG48_DEV_REV_MASK UINT8_C(0x07)
    #define REG48_PN_POS UINT8_C(0x03)
    #define REG48_DEV_REV_POS UINT8_C(0x00)


// set bits for the upper byte of registers containing values >8bit - when a parameter is split between lower and upper byte
#define BQ25792_SET_BITS_UPPER(reg_data, bitname, data) \
    ((reg_data & ~(bitname##_MASK)) |                   \
     ((data >> bitname##_POS) & bitname##_MASK))

// set bits for the 8 bit regs and lower byte of registers that contain values >8bit
#define BQ25792_SET_BITS(reg_data, bitname, data) \
    ((reg_data & ~(bitname##_MASK)) |             \
     ((data << bitname##_POS) & bitname##_MASK))

#define BQ25792_GET_BITS(reg_data, bitname) \
    ((reg_data & (bitname##_MASK)) >>       \
     (bitname##_POS))

#endif
