tschicki/PS2-Portable/SysCon Firmware/SysCon_FW/inc/MAX17320_Registers.h

#ifndef MAX17320_Registers_h
#define MAX17320_Registers_h

#include <stdint.h>
#include <stdio.h>
#include <string.h>

/*Register Map*/
#define REG6F_LEAKCURRREP UINT8_C(0x6F)
    #define REG6F_REPLEAKCURRENT_MASK UINT16_C(0x7FFF)
    #define REG6F_REPLEAKCURRENT_POS UINT8_C(0x0)
#define REG00_STATUS1 UINT8_C(0x00)
    #define REG00_POR_MASK UINT16_C(0x0002)
    #define REG00_POR_POS UINT8_C(0x01)
    #define REG00_IMN_MASK UINT16_C(0x0004)
    #define REG00_IMN_POS UINT8_C(0x02)
    #define REG00_IMX_MASK UINT16_C(0x0040)
    #define REG00_IMX_POS UINT8_C(0x06)
    #define REG00_DSOCI_MASK UINT16_C(0x0080)
    #define REG00_DSOCI_POS UINT8_C(0x07)
    #define REG00_VMN_MASK UINT16_C(0x0100)
    #define REG00_VMN_POS UINT8_C(0x08)
    #define REG00_TMN_MASK UINT16_C(0x0200)
    #define REG00_TMN_POS UINT8_C(0x09)
    #define REG00_SMN_MASK UINT16_C(0x0400)
    #define REG00_SMN_POS UINT8_C(0x0A)
    #define REG00_VMX_MASK UINT16_C(0x1000)
    #define REG00_VMX_POS UINT8_C(0x0C)
    #define REG00_TMX_MASK UINT16_C(0x2000)
    #define REG00_TMX_POS UINT8_C(0x0D)
    #define REG00_SMX_MASK UINT16_C(0x4000)
    #define REG00_SMX_POS UINT8_C(0x0E)
    #define REG00_PA_MASK UINT16_C(0x8000)
    #define REG00_PA_POS UINT8_C(0x0F)
#define REGB0_STATUS2 UINT8_C(0xB0)
    #define REGB0_HIB_MASK UINT16_C(0x0002)
    #define REGB0_HIB_POS UINT8_C(0x01)
#define REGD9_PROTSTATUS UINT8_C(0xD9)
    #define REGD9_SHIP_MASK UINT16_C(0x0001)
    #define REGD9_SHIP_POS UINT8_C(0x0)
    #define REGD9_RESDFAULT_MASK UINT16_C(0x0002)
    #define REGD9_RESDFAULT_POS UINT8_C(0x01)
    #define REGD9_ODCP_MASK UINT16_C(0x0004)
    #define REGD9_ODCP_POS UINT8_C(0x02)
    #define REGD9_UVP_MASK UINT16_C(0x0008)
    #define REGD9_UVP_POS UINT8_C(0x03)
    #define REGD9_TOOHOTD_MASK UINT16_C(0x0010)
    #define REGD9_TOOHOTD_POS UINT8_C(0x04)
    #define REGD9_DIEHOT_MASK UINT16_C(0x0020)
    #define REGD9_DIEHOT_POS UINT8_C(0x05)
    #define REGD9_PERMFAIL_MASK UINT16_C(0x0040)
    #define REGD9_PERMFAIL_POS UINT8_C(0x06)
    #define REGD9_IMBALANCE_MASK UINT16_C(0x0080)
    #define REGD9_IMBALANCE_POS UINT8_C(0x07)
    #define REGD9_PREQF_MASK UINT16_C(0x0100)
    #define REGD9_PREQF_POS UINT8_C(0x08)
    #define REGD9_QOVFLW_MASK UINT16_C(0x0200)
    #define REGD9_QOVFLW_POS UINT8_C(0x09)
    #define REGD9_OCCP_MASK UINT16_C(0x0400)
    #define REGD9_OCCP_POS UINT8_C(0x0A)
    #define REGD9_OVP_MASK UINT16_C(0x0800)
    #define REGD9_OVP_POS UINT8_C(0x0B)
    #define REGD9_TOOCOLDC_MASK UINT16_C(0x1000)
    #define REGD9_TOOCOLDC_POS UINT8_C(0x0C)
    #define REGD9_FULL_MASK UINT16_C(0x2000)
    #define REGD9_FULL_POS UINT8_C(0x0D)
    #define REGD9_TOOHOTC_MASK UINT16_C(0x4000)
    #define REGD9_TOOHOTC_POS UINT8_C(0x0E)
    #define REGD9_CHGWDT_MASK UINT16_C(0x8000)
    #define REGD9_CHGWDT_POS UINT8_C(0x0F)
#define REGAF_PROTALRT UINT8_C(0xAF)
    #define REGAF_LDET_MASK UINT16_C(0x0001)
    #define REGAF_LDET_POS UINT8_C(0x0)
    #define REGAF_RESDFAULT_MASK UINT16_C(0x0002)
    #define REGAF_RESDFAULT_POS UINT8_C(0x01)
    #define REGAF_ODCP_MASK UINT16_C(0x0004)
    #define REGAF_ODCP_POS UINT8_C(0x02)
    #define REGAF_UVP_MASK UINT16_C(0x0008)
    #define REGAF_UVP_POS UINT8_C(0x03)
    #define REGAF_TOOHOTD_MASK UINT16_C(0x0010)
    #define REGAF_TOOHOTD_POS UINT8_C(0x04)
    #define REGAF_DIEHOT_MASK UINT16_C(0x0020)
    #define REGAF_DIEHOT_POS UINT8_C(0x05)
    #define REGAF_PERMFAIL_MASK UINT16_C(0x0040)
    #define REGAF_PERMFAIL_POS UINT8_C(0x06)
    #define REGAF_IMBALANCE_MASK UINT16_C(0x0080)
    #define REGAF_IMBALANCE_POS UINT8_C(0x07)
    #define REGAF_PREQF_MASK UINT16_C(0x0100)
    #define REGAF_PREQF_POS UINT8_C(0x08)
    #define REGAF_QOVFLW_MASK UINT16_C(0x0200)
    #define REGAF_QOVFLW_POS UINT8_C(0x09)
    #define REGAF_OCCP_MASK UINT16_C(0x0400)
    #define REGAF_OCCP_POS UINT8_C(0x0A)
    #define REGAF_OVP_MASK UINT16_C(0x0800)
    #define REGAF_OVP_POS UINT8_C(0x0B)
    #define REGAF_TOOCOLDC_MASK UINT16_C(0x1000)
    #define REGAF_TOOCOLDC_POS UINT8_C(0x0C)
    #define REGAF_FULL_MASK UINT16_C(0x2000)
    #define REGAF_FULL_POS UINT8_C(0x0D)
    #define REGAF_TOOHOTC_MASK UINT16_C(0x4000)
    #define REGAF_TOOHOTC_POS UINT8_C(0x0E)
    #define REGAF_CHGWDT_MASK UINT16_C(0x8000)
    #define REGAF_CHGWDT_POS UINT8_C(0x0F)
#define REGF1_HPROTCFG2 UINT8_C(0xF1)
    #define REGF1_CHGS_MASK UINT16_C(0x0001)
    #define REGF1_CHGS_POS UINT8_C(0x0)
    #define REGF1_DISS_MASK UINT16_C(0x0002)
    #define REGF1_DISS_POS UINT8_C(0x01)
    #define REGF1_PBEN_MASK UINT16_C(0x0008)
    #define REGF1_PBEN_POS UINT8_C(0x03)
    #define REGF1_CPCFG_MASK UINT16_C(0x0060)
    #define REGF1_CPCFG_POS UINT8_C(0x05)
    #define REGF1_COMMOVRD_MASK UINT16_C(0x0100)
    #define REGF1_COMMOVRD_POS UINT8_C(0x08)
    #define REGF1_AOLDO_MASK UINT16_C(0xC000)
    #define REGF1_AOLDO_POS UINT8_C(0x0E)
#define REG1A_VCELL UINT8_C(0x1A)
#define REG19_AVGVCELL UINT8_C(0x19)
#define REGD8_CELL1 UINT8_C(0xD8)
#define REGD7_CELL2 UINT8_C(0xD7)
#define REGD6_CELL3 UINT8_C(0xD6)
#define REGD5_CELL4 UINT8_C(0xD5)
#define REGD4_AVGCELL1 UINT8_C(0xD4)
#define REGD3_AVGCELL2 UINT8_C(0xD3)
#define REGD2_AVGCELL3 UINT8_C(0xD2)
#define REGD1_AVGCELL4 UINT8_C(0xD1)
#define REGDA_BATT UINT8_C(0xDA)
#define REGDB_PCKP UINT8_C(0xDB)
#define REG08_MAXMINVOLT UINT8_C(0x08)
    #define REG08_MINVCELL_MASK UINT16_C(0x00FF)
    #define REG08_MINVCELL_POS UINT8_C(0x0)
    #define REG08_MAXVCELL_MASK UINT16_C(0xFF00)
    #define REG08_MAXVCELL_POS UINT8_C(0x08)
#define REG1C_CURRENT UINT8_C(0x1C)
#define REG1D_AVGCURRENT UINT8_C(0x1D)
#define REG0A_MAXMINCURR UINT8_C(0x0A)
    #define REG0A_MINCURRENT_MASK UINT16_C(0x00FF)
    #define REG0A_MINCURRENT_POS UINT8_C(0x0)
    #define REG0A_MAXCURRENT_MASK UINT16_C(0xFF00)
    #define REG0A_MAXCURRENT_POS UINT8_C(0x08)
#define REGB8_CGTEMPCO UINT8_C(0xB8)
#define REG1B_TEMP UINT8_C(0x1B)
#define REG16_AVGTA UINT8_C(0x16)
#define REG09_MAXMINTEMP UINT8_C(0x09)
    #define REG09_MINTEMPERATURE_MASK UINT16_C(0x00FF)
    #define REG09_MINTEMPERATURE_POS UINT8_C(0x0)
    #define REG09_MAXTEMPERATURE_MASK UINT16_C(0xFF00)
    #define REG09_MAXTEMPERATURE_POS UINT8_C(0x08)
#define REG34_DIETEMP UINT8_C(0x34)
#define REG40_AVGDIETEMP UINT8_C(0x40)
#define REG3A_TEMP1 UINT8_C(0x3A)
#define REG39_TEMP2 UINT8_C(0x39)
#define REG38_TEMP3 UINT8_C(0x38)
#define REG37_TEMP4 UINT8_C(0x37)
#define REG36_AVGTEMP1 UINT8_C(0x36)
#define REG35_AVGTEMP2 UINT8_C(0x35)
#define REG34_AVGTEMP3 UINT8_C(0x34)
#define REG33_AVGTEMP4 UINT8_C(0x33)
#define REGB1_POWER UINT8_C(0xB1)
#define REGB3_AVGPOWER UINT8_C(0xB3)
#define REG28_CHARGINGCURRENT UINT8_C(0x28)
#define REG2A_CHARGINGVOLTAGE UINT8_C(0x2A)
#define REG05_REPCAP UINT8_C(0x05)
#define REG06_REPSOC UINT8_C(0x06)
#define REG10_FULLCAP UINT8_C(0x10)
#define REG11_TIME_TO_EMPTY UINT8_C(0x11)
#define REG20_TIME_TO_FULL UINT8_C(0x20)
#define REG07_AGE UINT8_C(0x07)
#define REG17_CYCLES UINT8_C(0x17)
#define REG3E_TIMER UINT8_C(0x3E)
#define REGBE_TIMER_H UINT8_C(0xBE)
#define REG14_RCELL UINT8_C(0x14)
#define REGB2_VRIPPLE UINT8_C(0xB2)
#define REG3A_VEMPTY UINT8_C(0x3A)
    #define REG3A_VR_MASK UINT16_C(0x007F)
    #define REG3A_VR_POS UINT8_C(0x0)
    #define REG3A_VE_MASK UINT16_C(0xFF80)
    #define REG3A_VE_POS UINT8_C(0x07)
#define REG0B_CONFIG UINT8_C(0x0B)
    #define REG0B_PA_EN_MASK UINT16_C(0x0001)
    #define REG0B_PA_EN_POS UINT8_C(0x0)
    #define REG0B_A_EN_MASK UINT16_C(0x0004)
    #define REG0B_A_EN_POS UINT8_C(0x02)
    #define REG0B_FTHRM_MASK UINT16_C(0x0008)
    #define REG0B_FTHRM_POS UINT8_C(0x03)
    #define REG0B_ETHRM_MASK UINT16_C(0x0010)
    #define REG0B_ETHRM_POS UINT8_C(0x04)
    #define REG0B_COMMSH_MASK UINT16_C(0x0040)
    #define REG0B_COMMSH_POS UINT8_C(0x06)
    #define REG0B_SHIP_MASK UINT16_C(0x0080)
    #define REG0B_SHIP_POS UINT8_C(0x07)
    #define REG0B_DIS_BLOCKREAD_MASK UINT16_C(0x0200)
    #define REG0B_DIS_BLOCKREAD_POS UINT8_C(0x09)
    #define REG0B_PB_EN_MASK UINT16_C(0x0400)
    #define REG0B_PB_EN_POS UINT8_C(0x0A)
    #define REG0B_DIS_LDO_MASK UINT16_C(0x0800)
    #define REG0B_DIS_LDO_POS UINT8_C(0x0B)
    #define REG0B_VS_MASK UINT16_C(0x1000)
    #define REG0B_VS_POS UINT8_C(0x0C)
    #define REG0B_TS_MASK UINT16_C(0x2000)
    #define REG0B_TS_POS UINT8_C(0x0D)
    #define REG0B_SS_MASK UINT16_C(0x4000)
    #define REG0B_SS_POS UINT8_C(0x0E)
#define REGAB_CONFIG2 UINT8_C(0xAB)
    #define REGAB_DR_CFG_MASK UINT16_C(0x000C)
    #define REGAB_DR_CFG_POS UINT8_C(0x02)
    #define REGAB_T_ALRT_EN_MASK UINT16_C(0x0040)
    #define REGAB_T_ALRT_EN_POS UINT8_C(0x06)
    #define REGAB_D_SOC_EN_MASK UINT16_C(0x0080)
    #define REGAB_D_SOC_EN_POS UINT8_C(0x07)
    #define REGAB_POWR_MASK UINT16_C(0x0F00)
    #define REGAB_POWR_POS UINT8_C(0x08)
    #define REGAB_ADC_FIFO_EN_MASK UINT16_C(0x1000)
    #define REGAB_ADC_FIFO_EN_POS UINT8_C(0x0C)
    #define REGAB_AT_RT_EN_MASK UINT16_C(0x2000)
    #define REGAB_AT_RT_EN_POS UINT8_C(0x0D)
    #define REGAB_POR_CMD_MASK UINT16_C(0x8000)
    #define REGAB_POR_CMD_POS UINT8_C(0x0F)

/*NV CONFIG REGISTER ADDRESSES*/
#define N_XTABLE0_ADDRESS               UINT8_C(0x80)
#define N_XTABLE1_ADDRESS               UINT8_C(0x81)
#define N_XTABLE2_ADDRESS               UINT8_C(0x82)
#define N_XTABLE3_ADDRESS               UINT8_C(0x83)
#define N_XTABLE4_ADDRESS               UINT8_C(0x84)
#define N_XTABLE5_ADDRESS               UINT8_C(0x85)
#define N_XTABLE6_ADDRESS               UINT8_C(0x86)
#define N_XTABLE7_ADDRESS               UINT8_C(0x87)
#define N_XTABLE8_ADDRESS               UINT8_C(0x88)
#define N_XTABLE9_ADDRESS               UINT8_C(0x89)
#define N_XTABLE10_ADDRESS              UINT8_C(0x8A)
#define N_XTABLE11_ADDRESS              UINT8_C(0x8B)
#define N_VALRTTH_ADDRESS               UINT8_C(0x8C)
#define N_TALRTTH_ADDRESS               UINT8_C(0x8D)
#define N_IALRTTH_ADDRESS               UINT8_C(0x8E)
#define N_SALRTTH_ADDRESS               UINT8_C(0x8F)
#define N_OCVTABLE0_ADDRESS             UINT8_C(0x90)
#define N_OCVTABLE1_ADDRESS             UINT8_C(0x91)
#define N_OCVTABLE2_ADDRESS             UINT8_C(0x92)
#define N_OCVTABLE3_ADDRESS             UINT8_C(0x93)
#define N_OCVTABLE4_ADDRESS             UINT8_C(0x94)
#define N_OCVTABLE5_ADDRESS             UINT8_C(0x95)
#define N_OCVTABLE6_ADDRESS             UINT8_C(0x96)
#define N_OCVTABLE7_ADDRESS             UINT8_C(0x97)
#define N_OCVTABLE8_ADDRESS             UINT8_C(0x98)
#define N_OCVTABLE9_ADDRESS             UINT8_C(0x99)
#define N_OCVTABLE10_ADDRESS            UINT8_C(0x9A)
#define N_OCVTABLE11_ADDRESS            UINT8_C(0x9B)
#define N_ICHGTERM_ADDRESS              UINT8_C(0x9C)
#define N_FILTERCFG_ADDRESS             UINT8_C(0x9D)
#define N_VEMPTY_ADDRESS                UINT8_C(0x9E)
#define N_LEARNCFG_ADDRESS              UINT8_C(0x9F)
#define N_QRTABLE00_ADDRESS             UINT8_C(0xA0)
#define N_QRTABLE10_ADDRESS             UINT8_C(0xA1)
#define N_QRTABLE20_ADDRESS             UINT8_C(0xA2)
#define N_QRTABLE30_ADDRESS             UINT8_C(0xA3)
#define N_CYCLES_ADDRESS                UINT8_C(0xA4)
#define N_FULLCAPNOM_ADDRESS            UINT8_C(0xA5)
#define N_RCOMP0_ADDRESS                UINT8_C(0xA6)
#define N_TEMPCO_ADDRESS                UINT8_C(0xA7)
#define N_BATTSTATUS_ADDRESS            UINT8_C(0xA8)
    #define LEAKCURR_MASK UINT16_C(0x00FF)
    #define LEAKCURR_POS UINT8_C(0x0)
    #define CHKSUMF_MASK UINT16_C(0x0100)
    #define CHKSUMF_POS UINT8_C(0x08)
    #define LDET_MASK UINT16_C(0x0200)
    #define LDET_POS UINT8_C(0x09)
    #define FETFO_MASK UINT16_C(0x0400)
    #define FETFO_POS UINT8_C(0x0A)
    #define DFETFS_MASK UINT16_C(0x0800)
    #define DFETFS_POS UINT8_C(0x0B)
    #define CFETFS_MASK UINT16_C(0x1000)
    #define CFETFS_POS UINT8_C(0x0C)
    #define OTPF_MASK UINT16_C(0x2000)
    #define OTPF_POS UINT8_C(0x0D)
    #define OVPF_MASK UINT16_C(0x4000)
    #define OVPF_POS UINT8_C(0x0E)
    #define PERMFAIL_MASK UINT16_C(0x8000)
    #define PERMFAIL_POS UINT8_C(0x0F)
#define N_FULLCAPREP_ADDRESS            UINT8_C(0xA9)
#define N_DQTOT_ADDRESS                 UINT8_C(0xAA)
#define N_MAXMINCURR_ADDRESS            UINT8_C(0xAB)
#define N_MAXMINVOLT_ADDRESS            UINT8_C(0xAC)
#define N_MAXMINTEMP_ADDRESS            UINT8_C(0xAD)
#define N_FAULTLOG_ADDRESS              UINT8_C(0xAE)
#define N_TIMERH_ADDRESS                UINT8_C(0xAF)
#define N_CONFIG_ADDRESS                UINT8_C(0xB0)
#define N_RIPPLECFG_ADDRESS             UINT8_C(0xB1)
#define N_MISCCFG_ADDRESS               UINT8_C(0xB2)
#define N_DESIGNCAP_ADDRESS             UINT8_C(0xB3)
#define N_SBSCFG_ADDRESS                UINT8_C(0xB4)
#define N_PACKCFG_ADDRESS               UINT8_C(0xB5)
#define N_RELAXCFG_ADDRESS              UINT8_C(0xB6)
#define N_CONVGCFG_ADDRESS              UINT8_C(0xB7)
#define N_NVCFG0_ADDRESS                UINT8_C(0xB8)
#define N_NVCFG1_ADDRESS                UINT8_C(0xB9)
#define N_NVCFG2_ADDRESS                UINT8_C(0xBA)
#define N_HIBCFG_ADDRESS                UINT8_C(0xBB)
#define N_ROMID0_ADDRESS                UINT8_C(0xBC)
#define N_ROMID1_ADDRESS                UINT8_C(0xBD)
#define N_ROMID2_ADDRESS                UINT8_C(0xBE)
#define N_ROMID3_ADDRESS                UINT8_C(0xBF)
#define N_CHGCTRL1_ADDRESS              UINT8_C(0xC0)
#define N_PRESERVED1_ADDRESS            UINT8_C(0xC1)
#define N_CHGCFG0_ADDRESS               UINT8_C(0xC2)
#define N_CHGCTRL0_ADDRESS              UINT8_C(0xC3)
#define N_RGAIN_ADDRESS                 UINT8_C(0xC4)
#define N_PACKRESISTANCE_ADDRESS        UINT8_C(0xC5)
#define N_FULLSOCTHR_ADDRESS            UINT8_C(0xC6)
#define N_TTFCFG_ADDRESS                UINT8_C(0xC7)
#define N_CGAIN_ADDRESS                 UINT8_C(0xC8)
#define N_CGTEMPCO_ADDRESS              UINT8_C(0xC9)
#define N_THERMCFG_ADDRESS              UINT8_C(0xCA)
#define N_CHGCFG1_ADDRESS               UINT8_C(0xCB)
#define N_MANFCTRNAME_ADDRESS           UINT8_C(0xCC)
#define N_MANFCTRNAME1_ADDRESS          UINT8_C(0xCD)
#define N_MANFCTRNAME2_ADDRESS          UINT8_C(0xCE)
#define N_RSENSE_ADDRESS                UINT8_C(0xCF)
#define N_UVPRTTH_ADDRESS               UINT8_C(0xD0)
#define N_TPRTTH1_ADDRESS               UINT8_C(0xD1)
#define N_TPRTTH3_ADDRESS               UINT8_C(0xD2)
#define N_IPRTTH1_ADDRESS               UINT8_C(0xD3)
#define N_BALTH_ADDRESS                 UINT8_C(0xD4)
#define N_TPRTTH2_ADDRESS               UINT8_C(0xD5)
#define N_PROTMISCTH_ADDRESS            UINT8_C(0xD6)
#define N_PROTCFG_ADDRESS               UINT8_C(0xD7)
#define N_JEITAC_ADDRESS                UINT8_C(0xD8)
#define N_JEITAV_ADDRESS                UINT8_C(0xD9)
#define N_OVPRTTH_ADDRESS               UINT8_C(0xDA)
#define N_STEPCHG_ADDRESS               UINT8_C(0xDB)
#define N_DELAYCFG_ADDRESS              UINT8_C(0xDC)
#define N_ODSCTH_ADDRESS                UINT8_C(0xDD)
#define N_ODSCCFG_ADDRESS               UINT8_C(0xDE)
#define N_PROTCFG2_ADDRESS              UINT8_C(0xDF)
#define N_DPLIMIT_ADDRESS               UINT8_C(0xE0)
#define N_SCOCVLIM_ADDRESS              UINT8_C(0xE1)
#define N_AGEFCCFG_ADDRESS              UINT8_C(0xE2)
#define N_DESIGNVOLTAGE_ADDRESS         UINT8_C(0xE3)
#define N_VGAIN_ADDRESS                 UINT8_C(0xE4)
#define N_RFASTVSHDN_ADDRESS            UINT8_C(0xE5)
#define N_MANFCTRDATE_ADDRESS           UINT8_C(0xE6)
#define N_FIRSTUSED_ADDRESS             UINT8_C(0xE7)
#define N_SERIALNUMBER0_ADDRESS         UINT8_C(0xE8)
#define N_SERIALNUMBER1_ADDRESS         UINT8_C(0xE9)
#define N_SERIALNUMBER2_ADDRESS         UINT8_C(0xEA)
#define N_DEVICENAME0_ADDRESS           UINT8_C(0xEB)
#define N_DEVICENAME1_ADDRESS           UINT8_C(0xEC)
#define N_DEVICENAME2_ADDRESS           UINT8_C(0xED)
#define N_DEVICENAME3_ADDRESS           UINT8_C(0xEE)
#define N_DEVICENAME4_ADDRESS           UINT8_C(0xEF)

/*special registers*/

#define REG60_COMMAND                   UINT8_C(0x60)
#define REG61_COMMSTATUS                UINT8_C(0x61)
    #define REG61_WP_GLOBAL_MASK        UINT16_C(0x0001)
    #define REG61_WP_GLOBAL_POS         UINT8_C(0x00)
    #define REG61_NV_BUSY_MASK          UINT16_C(0x0002)
    #define REG61_NV_BUSY_POS           UINT8_C(0x01)
    #define REG61_NV_ERROR_MASK         UINT16_C(0x0004)
    #define REG61_NV_ERROR_POS          UINT8_C(0x02)
    #define REG61_WP1_MASK              UINT16_C(0x0008)
    #define REG61_WP1_POS               UINT8_C(0x03)
    #define REG61_WP2_MASK              UINT16_C(0x0010)
    #define REG61_WP2_POS               UINT8_C(0x04)
    #define REG61_WP3_MASK              UINT16_C(0x0020)
    #define REG61_WP3_POS               UINT8_C(0x05)
    #define REG61_WP4_MASK              UINT16_C(0x0040)
    #define REG61_WP4_POS               UINT8_C(0x06)
    #define REG61_WP5_MASK              UINT16_C(0x0080)
    #define REG61_WP5_POS               UINT8_C(0x07)
    #define REG61_CHG_OFF_MASK          UINT16_C(0x0100)
    #define REG61_CHG_OFF_POS           UINT8_C(0x08)
    #define REG61_DIS_OFF_MASK          UINT16_C(0x0200)
    #define REG61_DIS_OFF_POS           UINT8_C(0x09)
#define REG7F_LOCK                      UINT8_C(0x7F)


#endif
