tschicki/PS2-Portable/SysCon Firmware/SysCon_FW/ps2_video_processor/source/sprite_module.vhd

----------------------------------------------------------------------------------
-- Company: 
-- Engineer: Patrick Haid
-- 
-- Create Date: 16.02.2025 19:44:16
-- Design Name: PS2 Video Processor
-- Module Name: Sprite_Module - Behavioral
-- Project Name: Portable PS2
-- Target Devices: Trion T20
-- Tool Versions: Efinity
-- Description: 
-- 
-- Dependencies: 
-- 
-- Revision:
-- Revision 0.01 - File Created
-- Additional Comments:
-- 
----------------------------------------------------------------------------------


library IEEE;
use IEEE.STD_LOGIC_1164.ALL;
use IEEE.NUMERIC_STD.ALL;
use ieee.std_logic_unsigned.all;

library work;
use work.scaler_types.all;
use work.ram_pkg.all;


--8 bit wide sprite ram:
--sprite data #0 (1 bit per pixel)
--sprite data #1
--...

-- 8 bytes per sprite * 256 sprites = 2048 bytes in total

--Sprites
    --Color A 16 bit
    --Color B 16 bit
    
    --cursor x 16 bit (12 bit)
    --cursor y 16 bit (10 bit)
    
    --sprite#  16 bit
    
--sprite buffer
    --posX LSB
    --posX MSB
    --posY LSB
    --posY MSB
    --address
    
---> 3x block RAM: 1x 8 bit address; 1x position: 12 bit X + 10 bit Y; 12 bit color A + 12 bit color B
    --8+12+10+24 bits wide * 1024 sprites = 6912 bytes of BRAM

--firmware will need to remember the address in which the first element of each entity was written to, in order to erase it later
--should be fine, if the length of all elements is static, otherwise this could not work -> CHECK!!!

entity Sprite_Module is
Port (
    i_rst_n : in std_logic;
    i_clk : in std_logic;

    --control interface to configure all the modules
    i_data_config : in std_logic_vector(7 downto 0);
    --o_data_config : out std_logic_vector(7 downto 0);
    i_addr_config : in std_logic_vector(15 downto 0);
    i_rw_config : in std_logic;
    i_cs_config : in std_logic;
    
    --data input from scaler
    i_we : in std_logic;                               
    i_data : in std_logic_vector(23 downto 0);             
    i_addr : in std_logic_vector(9 downto 0);   
    i_line_count : in integer range 0 to 1024;
    
    --data output to CDC line buffer
    o_we : out std_logic;                               
    o_data : out std_logic_vector(23 downto 0);             
    o_addr : out std_logic_vector(9 downto 0)                     
 );
end Sprite_Module;

architecture Behavioral of Sprite_Module is

component efx_simple_dual_port_2_clk_ram is
  generic (
    RAM_WIDTH : integer := 24;
    RAM_DEPTH : integer := 1024;
    OUTREG    : boolean := true
    );
  Port (
    addra  : in  std_logic_vector((logb2(RAM_DEPTH)-1) downto 0);
    addrb  : in  std_logic_vector((logb2(RAM_DEPTH)-1) downto 0);
    dina   : in  std_logic_vector(RAM_WIDTH-1 downto 0);
    clka   : in  std_logic;
    clkb   : in  std_logic;
    wea    : in  std_logic;
    enb    : in  std_logic;
    rstb   : in  std_logic;
    regceb : in  std_logic;
    doutb  : out std_logic_vector(RAM_WIDTH-1 downto 0));
end component efx_simple_dual_port_2_clk_ram;


type state_type_write is (state_wait, 
                        state_analyze, 
                        state_write_regs,
                        state_write_buffer,
                        state_write_ram,
                        state_increment_position,
                        state_save_position
                        );
                    
type state_type_read is (state_wait, 
                        state_read_buffer,
                        state_check_empty,
                        state_check_overlap,
                        state_wait_for_drawing
                        );
                             
type state_type_draw is (state_wait, 
                        state_read_sprite,
                        state_draw_sprite
                        );
                                                            
signal write_state : state_type_write := state_wait;
signal read_state : state_type_read := state_wait;
signal draw_state : state_type_draw := state_wait;

type t_registers is array (10 downto 0) of std_logic_vector(7 downto 0);
signal register_array : t_registers;

signal current_data : std_logic_vector(7 downto 0) := (others=>'0');
signal current_addr : std_logic_vector(15 downto 0) := (others=>'0');

signal spritebuffer_data_wr, spritebuffer_data_re : std_logic_vector(53 downto 0) := (others=>'0');
signal spritebuffer_addr_wr, spritebuffer_addr_re : std_logic_vector(9 downto 0) := (others=>'0');
signal spritebuffer_we, spritebuffer_re : std_logic := '0';

signal spriteram_data_wr, spriteram_data_re : std_logic_vector(7 downto 0) := (others=>'0');
signal spriteram_addr_wr, spriteram_addr_re : std_logic_vector(10 downto 0) := (others=>'0');
signal spriteram_we, spriteram_re : std_logic := '0';
signal spriteram_addr_re_int : integer range 0 to 2048 := 0;

signal posX_wr, posY_wr, new_posX_wr, colorA_wr, colorB_wr : std_logic_vector(15 downto 0) := (others=>'0');
signal posX_int : integer range 0 to 1023 := 0;

signal read_addr : integer range 0 to 1024 := 0;

signal posX_re, posX_sec : integer range 0 to 1024 := 0;
signal posY_re, posY8_re : integer range 0 to 1024 := 0;
signal line_count : integer range 0 to 1024 := 0;
signal cur_sprite_offset : std_logic_vector(10 downto 0) := (others=>'0');
signal colorA_re, colorB_re, colorA_sec, colorB_sec : std_logic_vector(11 downto 0) := (others=>'0');

signal sec_fsm_start, sec_busy : std_logic := '0';

signal data_out : std_logic_vector(23 downto 0) := (others=>'0');             
signal addr_out : std_logic_vector(9 downto 0) := (others=>'0');
signal we_out : std_logic := '0';
signal sprite_line_to_draw : std_logic_vector(7 downto 0) := (others=>'0');
signal bit_counter, bit_sel : integer range 0 to 63 := 0;

signal we_end : std_logic := '0';
signal sprite_counter : integer range 0 to 63 := 0;
signal sprite_start, we_in1, we_in2 : std_logic := '0';
signal sprite_to_draw_flag : std_logic := '0';

signal scaling_factor, sprite_size : integer range 0 to 255 := 0;
signal sprite_line : integer range 0 to 255 := 0;

signal delay : std_logic := '0';

constant sprite_size_base : unsigned(7 downto 0) := "00001000";
begin

sprite_ram: efx_simple_dual_port_2_clk_ram
  generic map (RAM_WIDTH => 8, RAM_DEPTH => 2048, OUTREG => true) 
  port map (
    addra  => spriteram_addr_wr,
    addrb  => std_logic_vector(to_unsigned(spriteram_addr_re_int, 11)),
    dina   => spriteram_data_wr,
    clka   => i_clk,
    clkb   => i_clk,
    wea    => spriteram_we,
    enb    => spriteram_re,
    rstb   => i_rst_n,
    regceb => spriteram_re,
    doutb  => spriteram_data_re);

spritebuffer_ram: efx_simple_dual_port_2_clk_ram
  generic map (RAM_WIDTH => 30, RAM_DEPTH => 1024, OUTREG => true) 
  port map (
    addra  => spritebuffer_addr_wr,
    addrb  => spritebuffer_addr_re,
    dina   => spritebuffer_data_wr(53 downto 24),
    clka   => i_clk,
    clkb   => i_clk,
    wea    => spritebuffer_we,
    enb    => spritebuffer_re,
    rstb   => i_rst_n,
    regceb => spritebuffer_re,
    doutb  => spritebuffer_data_re(53 downto 24));

spritebuffer_color: efx_simple_dual_port_2_clk_ram
  generic map (RAM_WIDTH => 24, RAM_DEPTH => 1024, OUTREG => true) 
  port map (
    addra  => spritebuffer_addr_wr,
    addrb  => spritebuffer_addr_re,
    dina   => spritebuffer_data_wr(23 downto 0),
    clka   => i_clk,
    clkb   => i_clk,
    wea    => spritebuffer_we,
    enb    => spritebuffer_re,
    rstb   => i_rst_n,
    regceb => spritebuffer_re,
    doutb  => spritebuffer_data_re(23 downto 0));

--muxing the scaler lines and sprite lines for the linebuffer
o_we <= i_we when (we_out = '0') else
        we_out;                            
o_data <= i_data when (we_out = '0') else 
          data_out;            
o_addr <= i_addr when (we_out = '0') else 
          addr_out;    

--this FSM takes care of write accesses to the registers and ram
sprite_write:process(i_clk, i_rst_n)
begin
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
