tschicki/PS2-Portable/SysCon Firmware/SysCon_FW/inc/fpga.h

#ifndef FPGA_H
#define FPGA_H
#include "MCU_interface.h"
#include "FPGA_Registers.h"
#include "flash.h"
#include "helper_functions.h"
/*SPI INTERFACE------------------------------------------------------*/
/*lower level command stuff*/
#define SPI_PACKET_SIZE_BITSTREAM       8
#define SPI_PACKET_SIZE_FONT            8
/*FPGA SPI commands*/
#define CMD_WRITE_REG                   0x01
#define CMD_READ_REG                    0x02

/*SPRITE DEFINES------------------------------------------------------*/
#define SPRITE_DEFAULT_SCALE             1   //0 = 8x8 sprites; 1 = 16x16 sprites; everything else is untested...
#define COLOR_FONT_DESEL                 0
#define COLOR_BACK_DESEL                 1
#define COLOR_FONT_SEL                   2
#define COLOR_BACK_SEL                   3
#define COLOR_LSB                        0
#define COLOR_MSB                        1
/*VIDEO CONFIG DEFINES-------------------------------------------------------*/
/*these specify whether to load the settings from flash or store them*/
#define RES_LOAD                         0
#define RES_STORE                        1
/*possible returns when reading resolution register*/
#define RETURN_512i                      0
#define RETURN_480i                      32
#define RETURN_480p                      64
#define RETURN_256p                      96
#define RETURN_240p                      128

/*BACKLIGHT DEFINES-------------------------------------------------------*/
#define BACKLIGHT_MAX_BRIGHTNESS        100
#define BACKLIGHT_MAX_COUNT             BACKLIGHT_MAX_BRIGHTNESS*2     //pwm frequency = 150MHz / (BACKLIGHT_MAX_COUNT<<4); with 200 it is about 46kHz

/*commands for various updating functions*/
#define UPDATE_X                        0
#define UPDATE_Y                        1
#define RES_IN_X                        0
#define RES_IN_Y                        1
#define RES_OUT_X                       2
#define RES_OUT_Y                       3

/*amount of video settings per resolution*/
typedef enum video_settings
{
    NO_H_IMAGE_OFFSET = 0,    
    NO_H_IMAGE_ACTIVE,    
    NO_H_ACTIVE_PXL,      
    NO_H_PACKED_PXL,      
    NO_V_IMAGE_OFFSET,    
    NO_V_IMAGE_ACTIVE,    
    NO_INTERLACE,         
    NO_SAMPLING_DIVIDER,  
    NO_DEINTERLACER_DEBUG,
    NO_MOTION_THRESHOLD,
    NO_PHASE,
    NO_SCALING_X,
    NO_SCALING_Y,
    NO_TARGET_RES_X,
    NO_TARGET_RES_Y,

    /*this must always be the last one in the list*/
    NO_VIDEO_SETTINGS, 
}video_settings_t;


typedef enum video_resolutions
{
    RES_512i = 0,    
    RES_480i,    
    RES_480p, 
    RES_256p,
    RES_240p,     

    /*this must always be the last one in the list*/
    NO_RESOLUTIONS, 
}video_resolutions_t;
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
